dpmj/Bachelor_Thesis_TIK_Handheld_Device/ASSETS/IMAGES/DATASHEET SCREENSHOTS/ESP32_strapping_pins.png

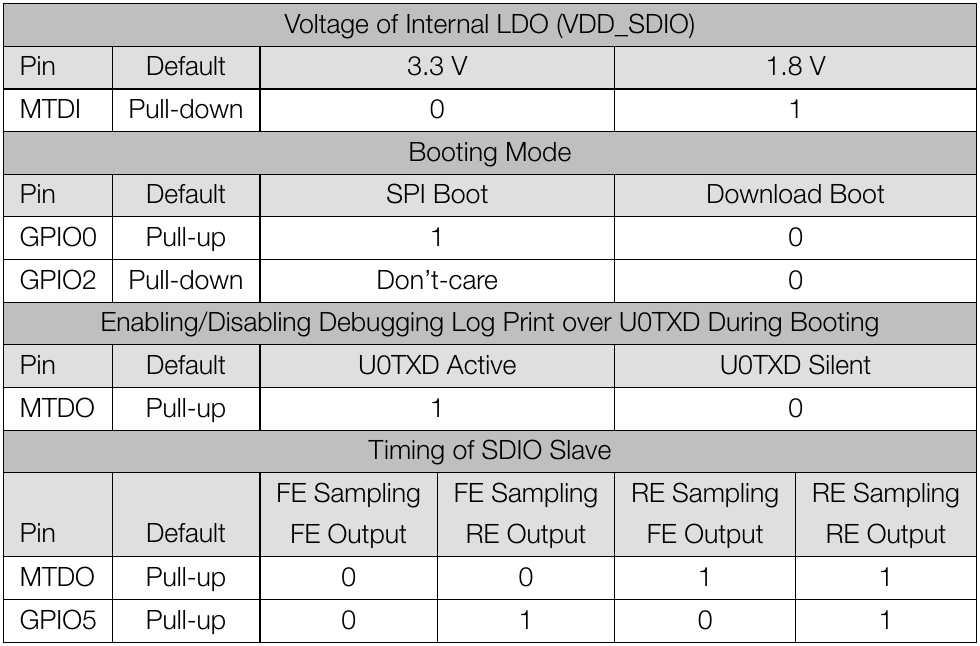
ASSETS/IMAGES/DATASHEET SCREENSHOTS/ESP32_strapping_pins.png
