dpmj/Bachelor_Thesis_TIK_Handheld_Device/ASSETS/IMAGES/PARTS/ESP32-WROOM-32D/esp32_pinout_datasheet.png

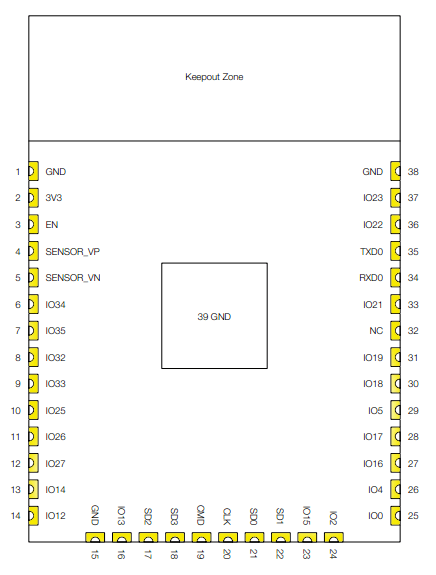
ASSETS/IMAGES/PARTS/ESP32-WROOM-32D/esp32_pinout_datasheet.png
