dpmj/Bachelor_Thesis_TIK_Handheld_Device/ASSETS/IMAGES/PARTS/ESP32-WROOM-32D/pinout_wroom_pinout_2.png

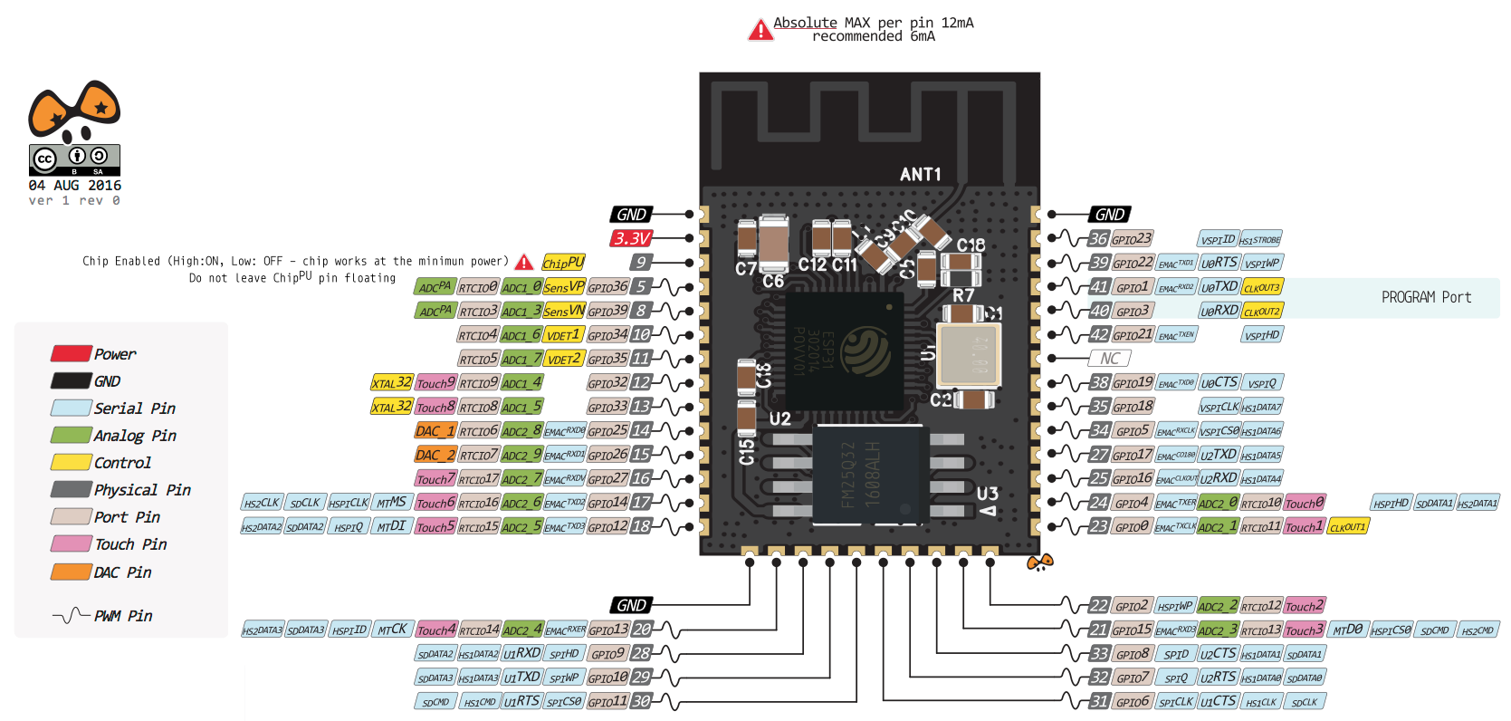
ASSETS/IMAGES/PARTS/ESP32-WROOM-32D/pinout_wroom_pinout_2.png
