dpmj/Bachelor_Thesis_TIK_Handheld_Device/ASSETS/IMAGES/PARTS/JACK/PINOUT.png

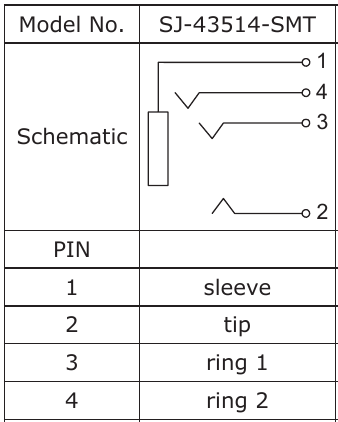
ASSETS/IMAGES/PARTS/JACK/PINOUT.png
