dpmj/Bachelor_Thesis_TIK_Handheld_Device/ASSETS/IMAGES/PARTS/JACK/PINOUT_6.png

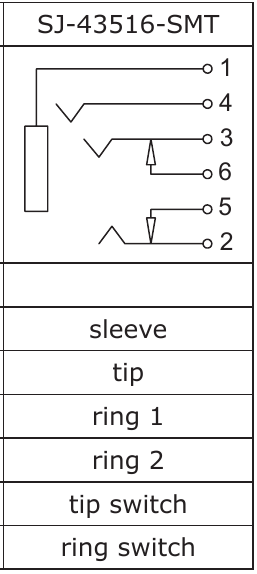
ASSETS/IMAGES/PARTS/JACK/PINOUT_6.png
