dpmj/Bachelor_Thesis_TIK_Handheld_Device/ASSETS/IMAGES/PCB RENDERS/bottom.png

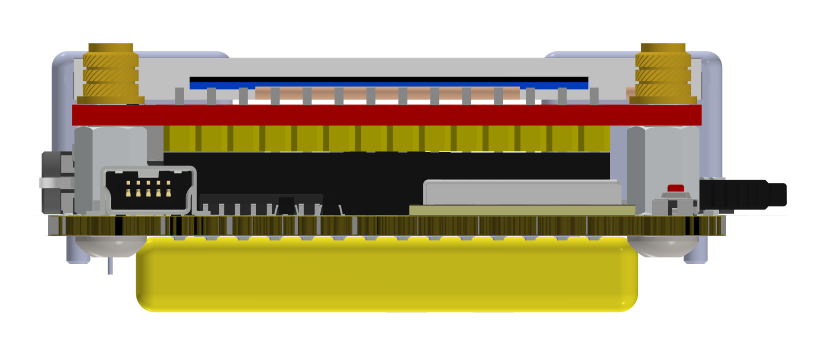
ASSETS/IMAGES/PCB RENDERS/bottom.png
