dpmj/Bachelor_Thesis_TIK_Handheld_Device/ASSETS/IMAGES/PCB RENDERS/FRONT.png

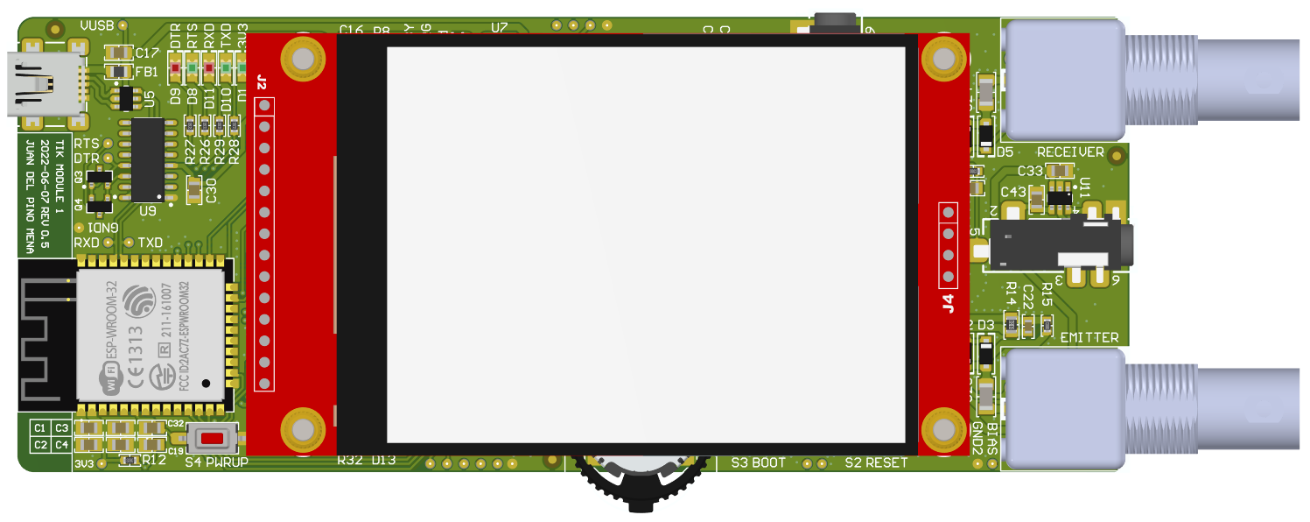
ASSETS/IMAGES/PCB RENDERS/FRONT.png
