dpmj/Bachelor_Thesis_TIK_Handheld_Device/ASSETS/IMAGES/PCB RENDERS/FRONT_NOSCREEN.png

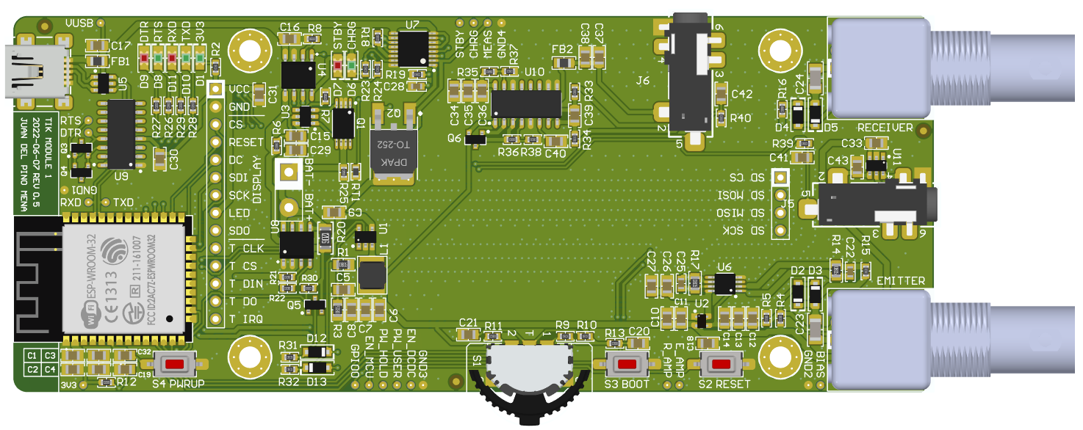
ASSETS/IMAGES/PCB RENDERS/FRONT_NOSCREEN.png
