dpmj/Bachelor_Thesis_TIK_Handheld_Device/ASSETS/IMAGES/PCB RENDERS/introduction2.png

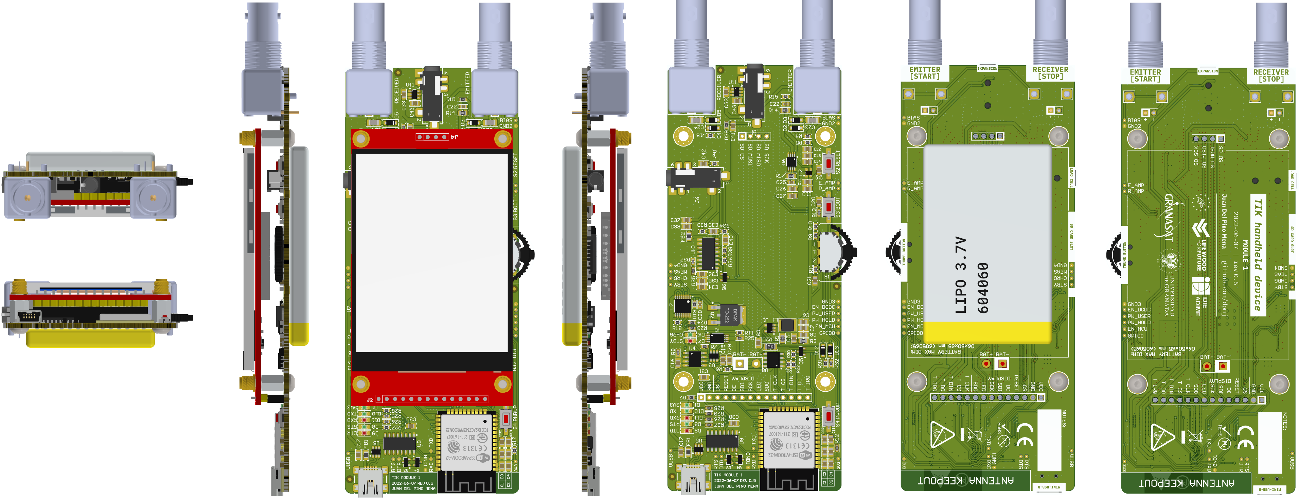
ASSETS/IMAGES/PCB RENDERS/introduction2.png
