dpmj/Bachelor_Thesis_TIK_Handheld_Device/ASSETS/IMAGES/PCB RENDERS/introduction.png

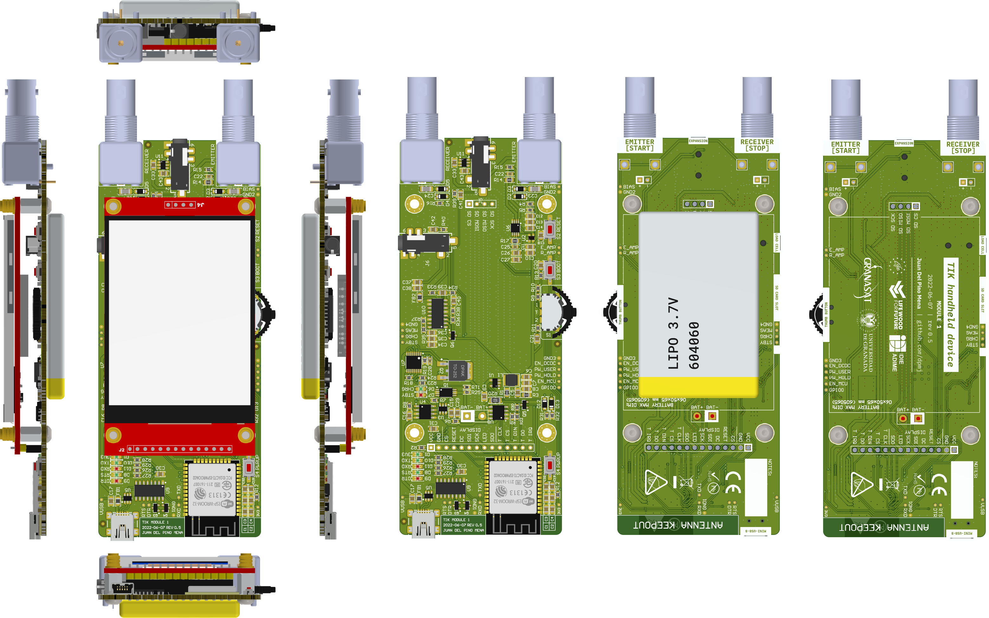
ASSETS/IMAGES/PCB RENDERS/introduction.png
