dpmj/Bachelor_Thesis_TIK_Handheld_Device/ASSETS/IMAGES/PCB RENDERS/PERSPECTIVE.png

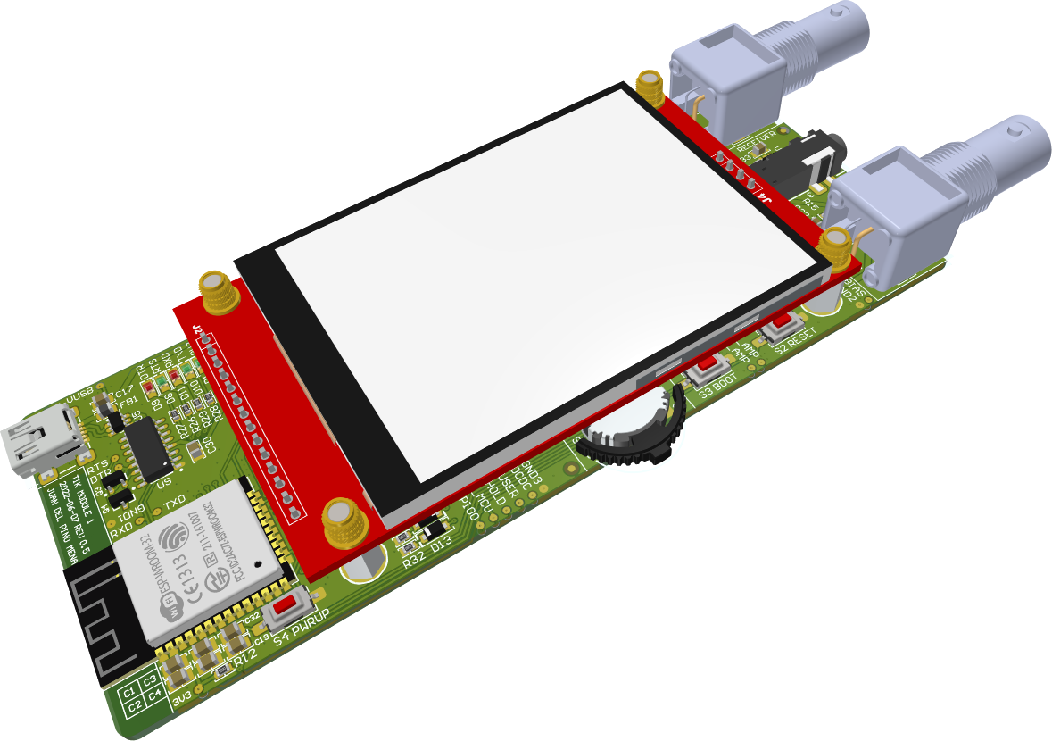
ASSETS/IMAGES/PCB RENDERS/PERSPECTIVE.png
