dpmj/Bachelor_Thesis_TIK_Handheld_Device/ASSETS/IMAGES/PCB RENDERS/SIDE_05.png

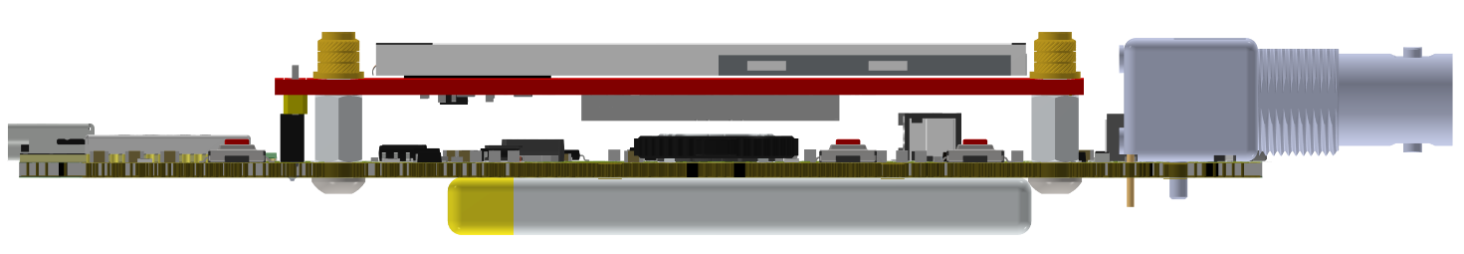
ASSETS/IMAGES/PCB RENDERS/SIDE_05.png
