dpmj/Bachelor_Thesis_TIK_Handheld_Device/ASSETS/IMAGES/PCB RENDERS/SIDE_05_2.png

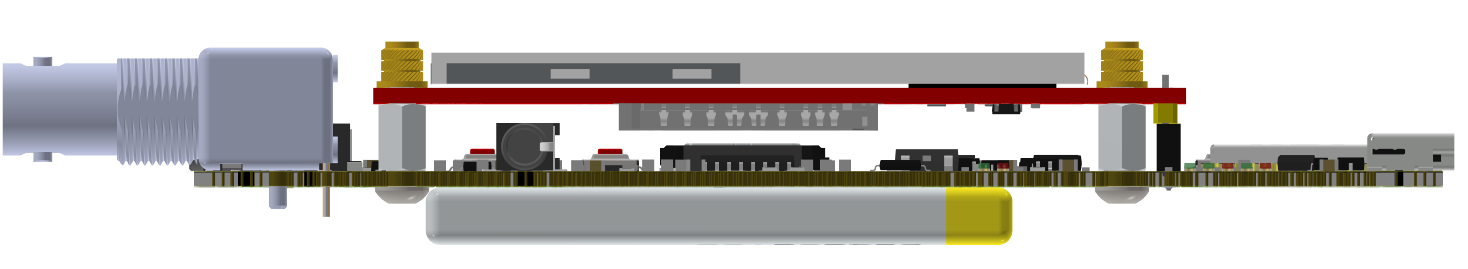
ASSETS/IMAGES/PCB RENDERS/SIDE_05_2.png
