dpmj/Bachelor_Thesis_TIK_Handheld_Device/ASSETS/IMAGES/SATURN PCB DESIGN/80MHZ_WL.png

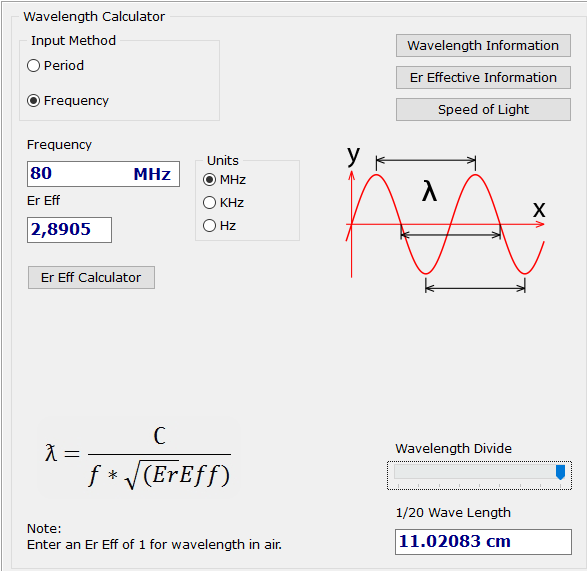
ASSETS/IMAGES/SATURN PCB DESIGN/80MHZ_WL.png
