dpmj/Bachelor_Thesis_TIK_Handheld_Device/ASSETS/IMAGES/SATURN PCB DESIGN/analog_crosstalk.png

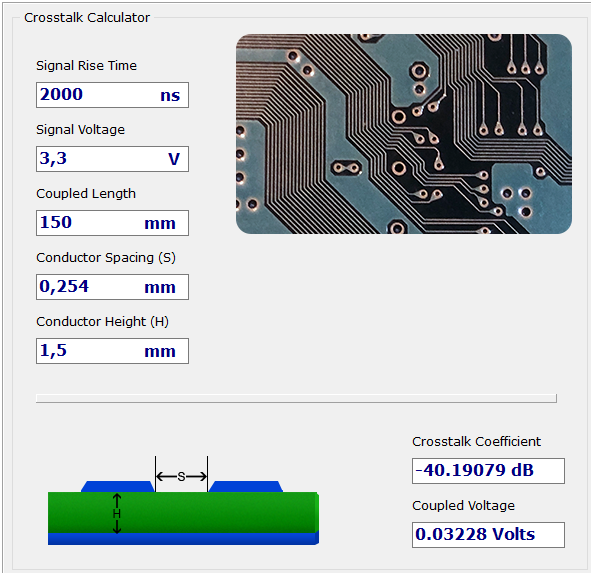
ASSETS/IMAGES/SATURN PCB DESIGN/analog_crosstalk.png
