dpmj/Bachelor_Thesis_TIK_Handheld_Device/ASSETS/IMAGES/SATURN PCB DESIGN/analog_er_Eff.png

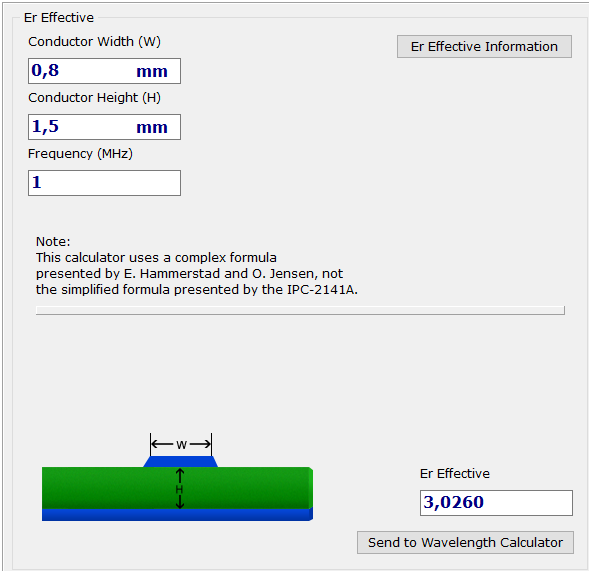
ASSETS/IMAGES/SATURN PCB DESIGN/analog_er_Eff.png
