dpmj/Bachelor_Thesis_TIK_Handheld_Device/ASSETS/IMAGES/SATURN PCB DESIGN/TRACE_0_8mm_COPLANAR_SIGNAL.png

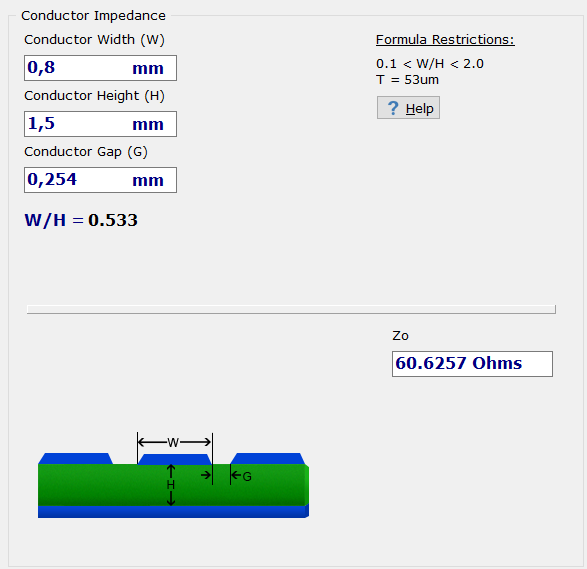
ASSETS/IMAGES/SATURN PCB DESIGN/TRACE_0_8mm_COPLANAR_SIGNAL.png
