dpmj/Bachelor_Thesis_TIK_Handheld_Device/ASSETS/IMAGES/SATURN PCB DESIGN/TRACE_05mm.png

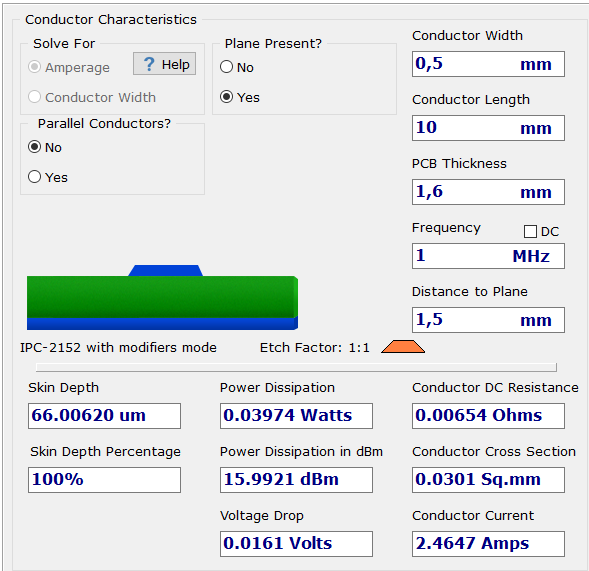
ASSETS/IMAGES/SATURN PCB DESIGN/TRACE_05mm.png
