dpmj/Bachelor_Thesis_TIK_Handheld_Device/ASSETS/IMAGES/SATURN PCB DESIGN/TRACE_08mm_2.png

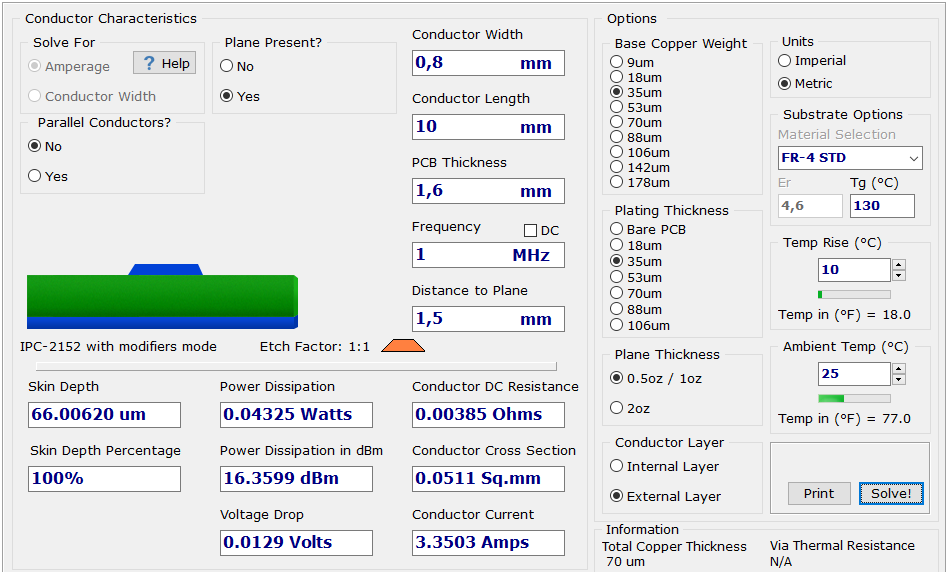
ASSETS/IMAGES/SATURN PCB DESIGN/TRACE_08mm_2.png
