dpmj/Bachelor_Thesis_TIK_Handheld_Device/ASSETS/IMAGES/SATURN PCB DESIGN/VIA_30_60.png

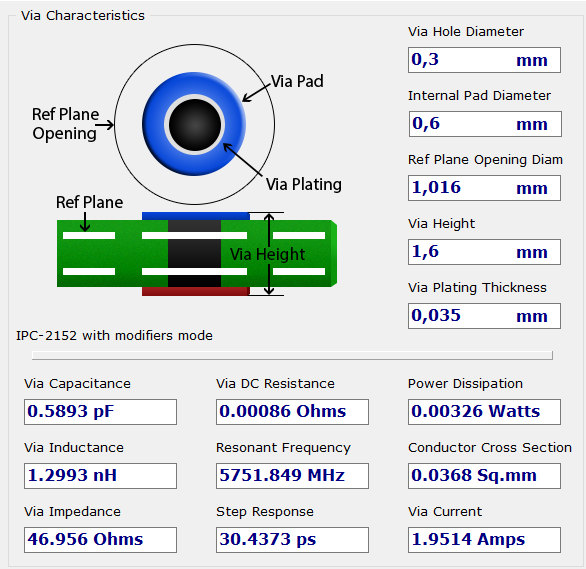
ASSETS/IMAGES/SATURN PCB DESIGN/VIA_30_60.png
