dpmj/Bachelor_Thesis_TIK_Handheld_Device/ASSETS/IMAGES/SIGNALS/psd.png

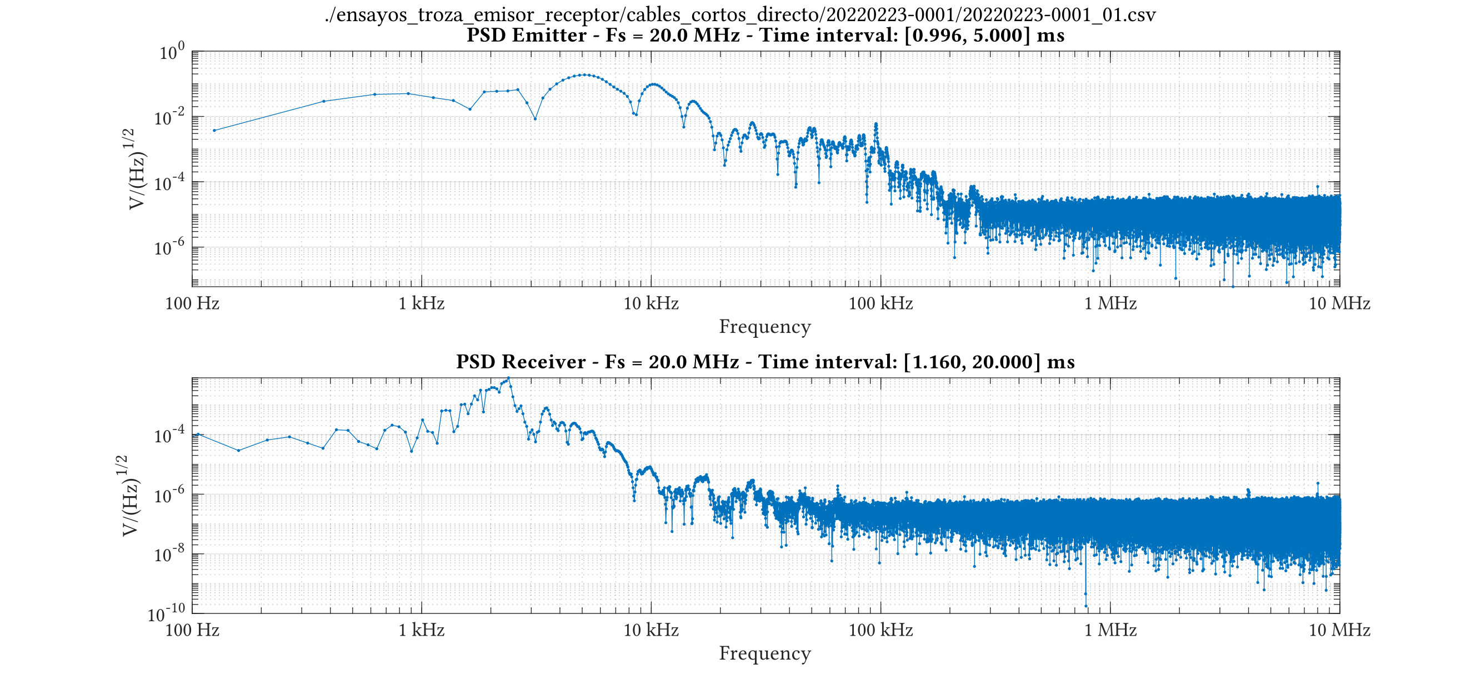
ASSETS/IMAGES/SIGNALS/psd.png
