dpmj/Bachelor_Thesis_TIK_Handheld_Device/ASSETS/power budget/power budget2.pdf.2022_08_09_00_11_06.0.png

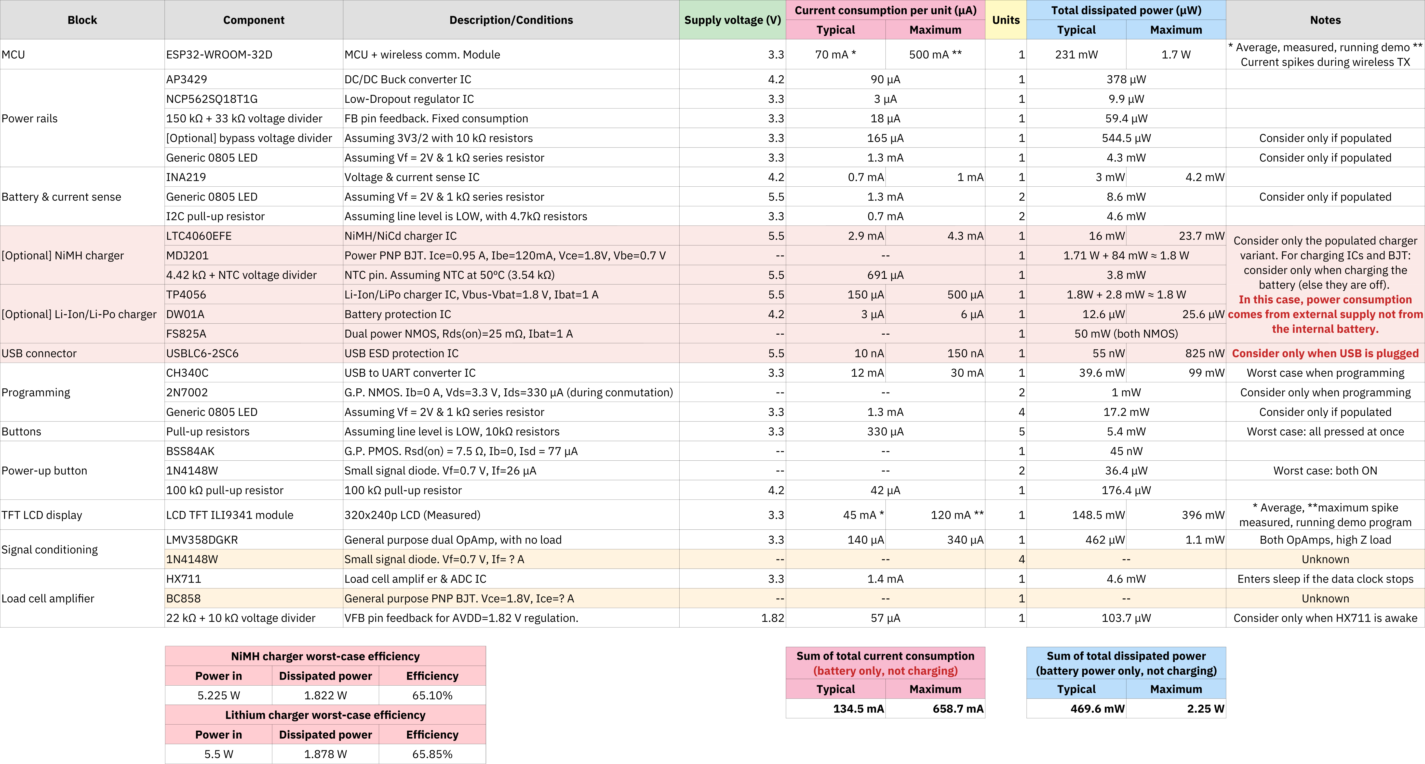
ASSETS/power budget/power budget2.pdf.2022_08_09_00_11_06.0.png
