dpmj/Bachelor_Thesis_TIK_Handheld_Device/ASSETS/power budget/power_budget.png

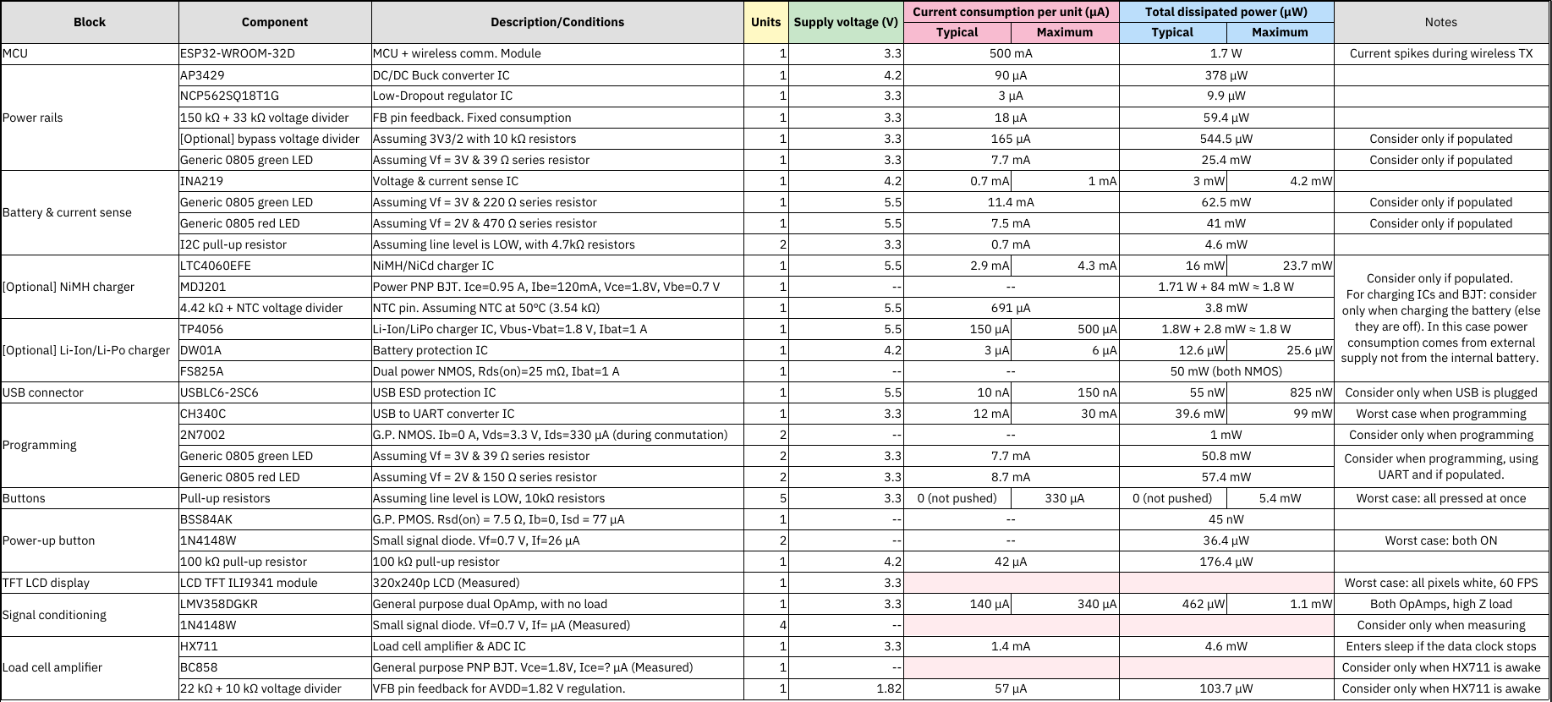
ASSETS/power budget/power_budget.png
