dpmj/Bachelor_Thesis_TIK_Handheld_Device/ASSETS/SPICE/ALTIUM/CLIPPED_SIGNALS.png

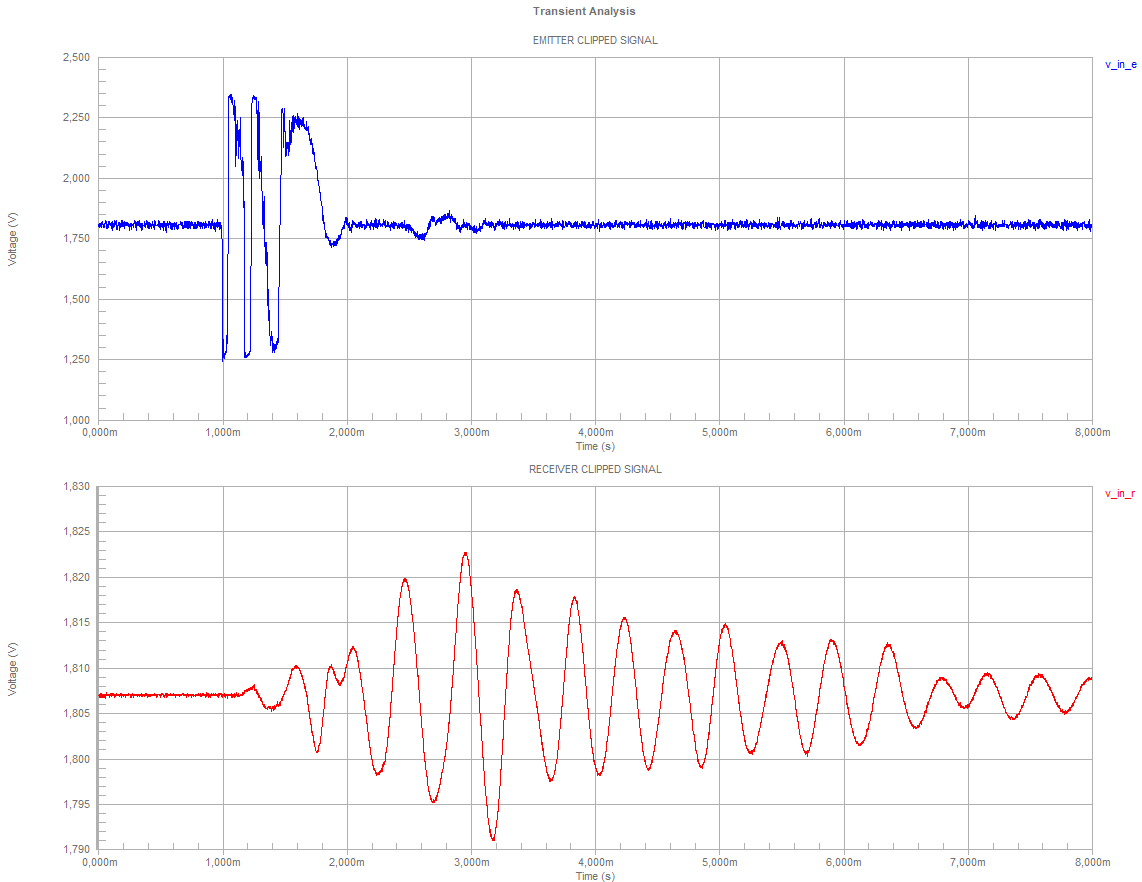
ASSETS/SPICE/ALTIUM/CLIPPED_SIGNALS.png
