dpmj/Bachelor_Thesis_TIK_Handheld_Device/ASSETS/SPICE/ALTIUM/emitter_all_signals.png

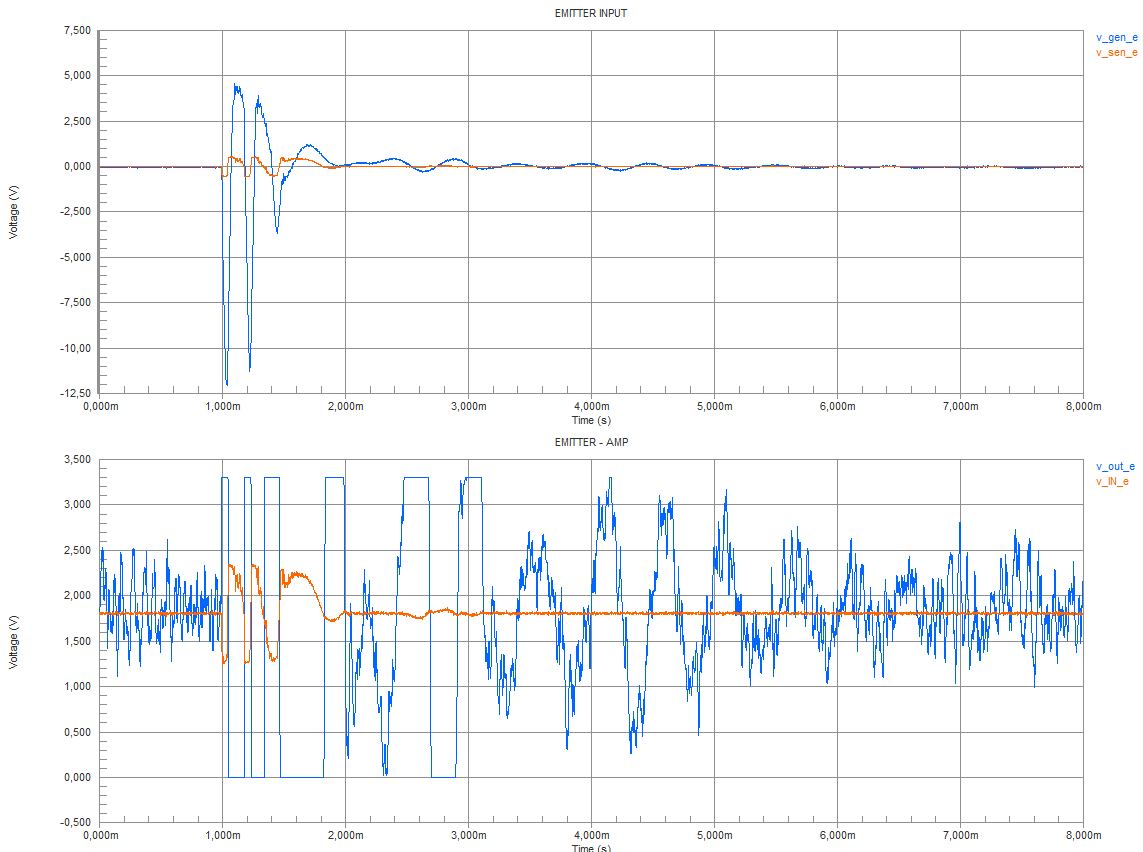
ASSETS/SPICE/ALTIUM/emitter_all_signals.png
