dpmj/Bachelor_Thesis_TIK_Handheld_Device/ASSETS/SPICE/ALTIUM/emitter_all_signals_fft.png

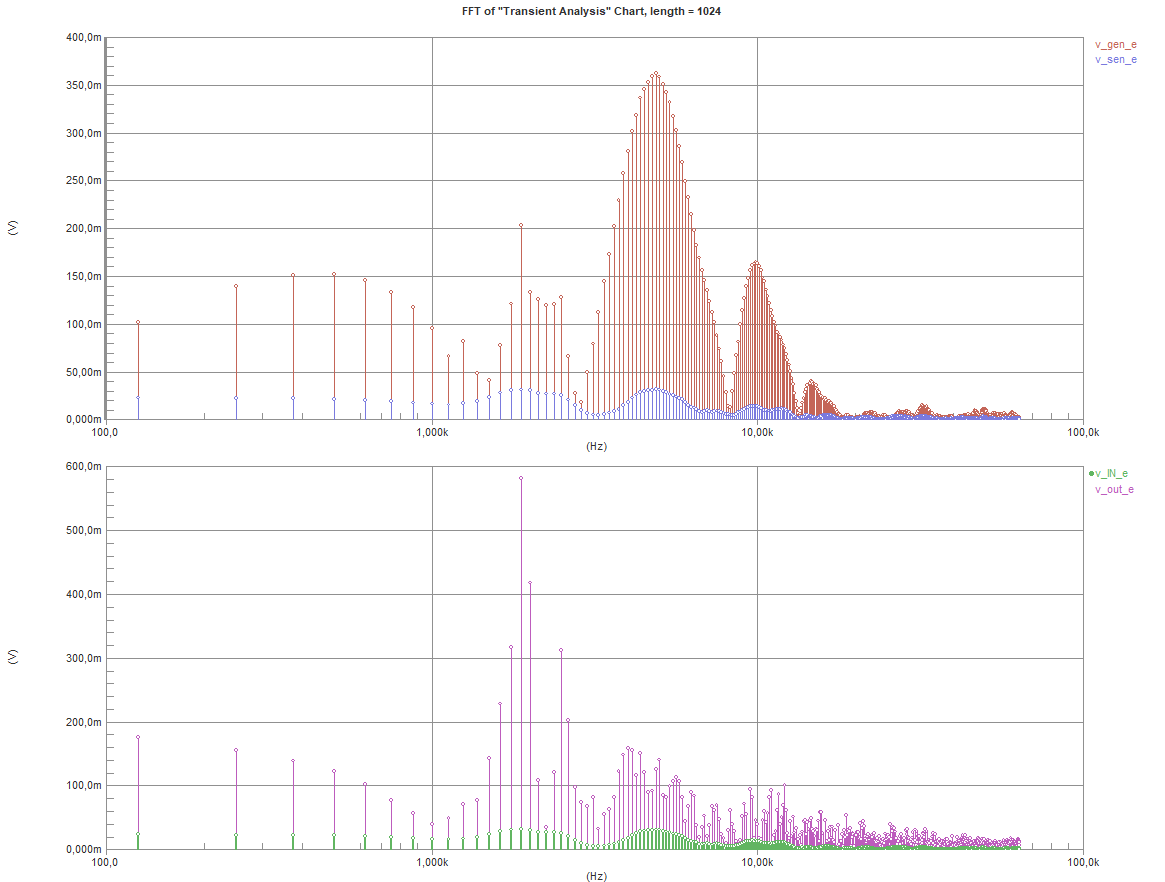
ASSETS/SPICE/ALTIUM/emitter_all_signals_fft.png
