dpmj/Bachelor_Thesis_TIK_Handheld_Device/ASSETS/SPICE/ALTIUM/receiver_all_signals.png

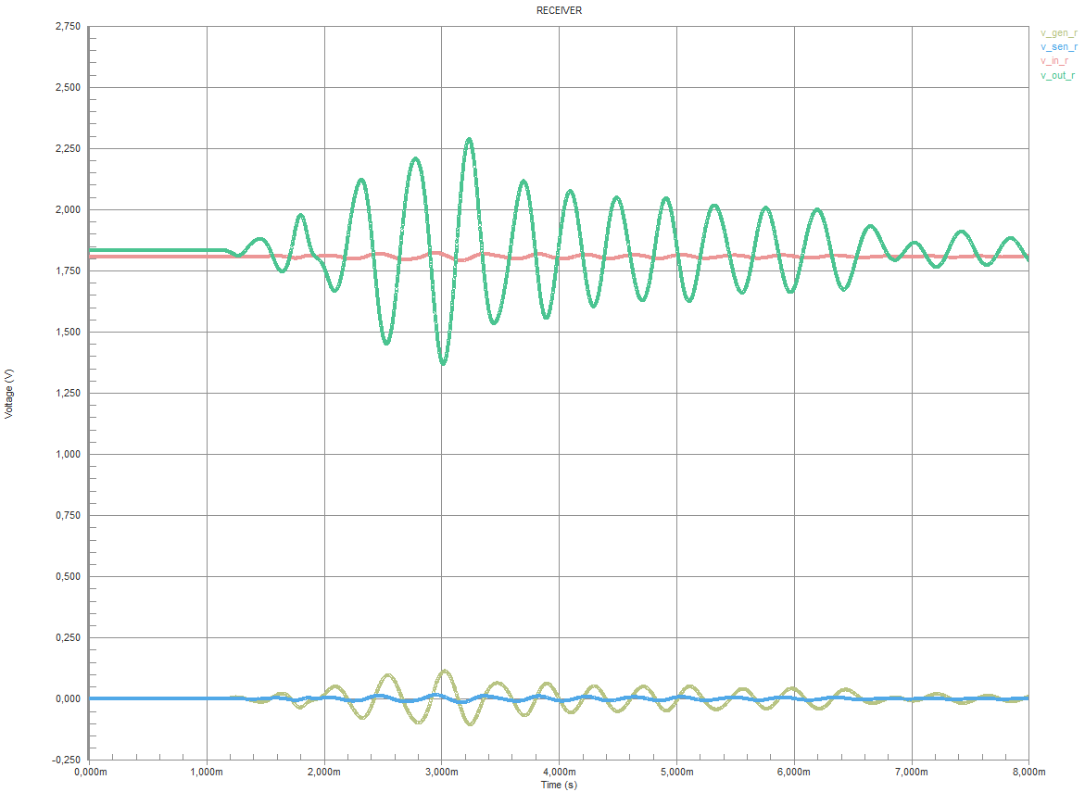
ASSETS/SPICE/ALTIUM/receiver_all_signals.png
