dpmj/Bachelor_Thesis_TIK_Handheld_Device/ASSETS/SPICE/ALTIUM/rise_time.png

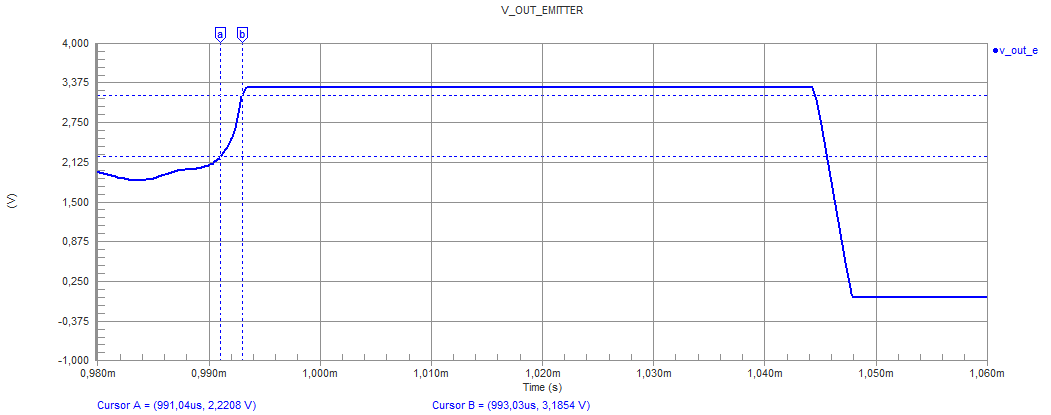
ASSETS/SPICE/ALTIUM/rise_time.png
