dpmj/Bachelor_Thesis_TIK_Handheld_Device/ASSETS/SPICE/ALTIUM/sim_circuit.png

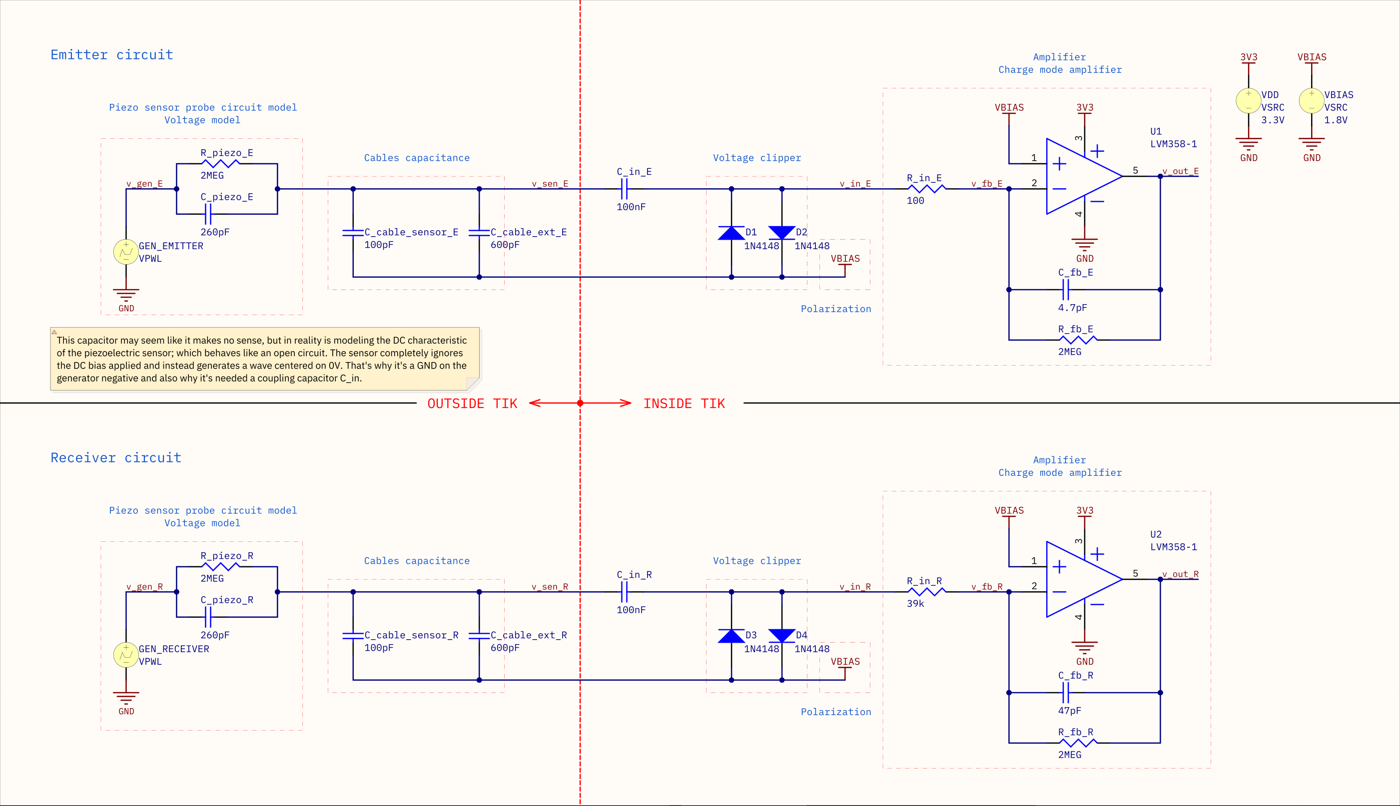
ASSETS/SPICE/ALTIUM/sim_circuit.png
