dpmj/Bachelor_Thesis_TIK_Handheld_Device/ASSETS/SPICE/LTSPICE/CONDITIONING/AC_1Hz_10Meg_CF22pF_RF10M_Rin100.png

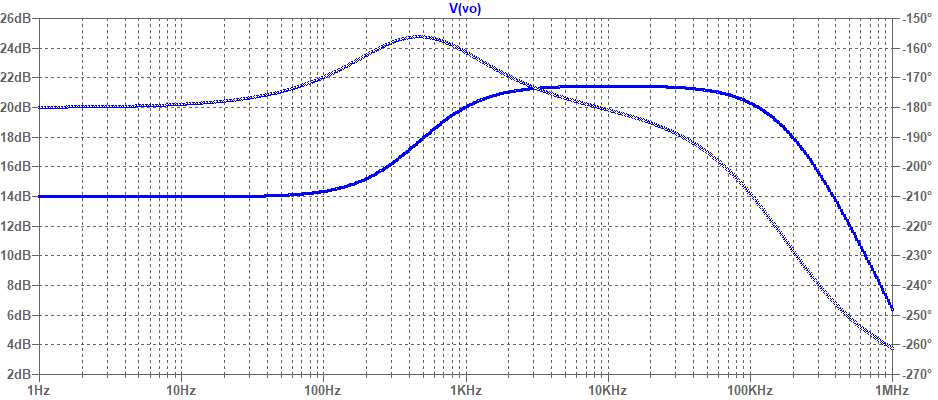
ASSETS/SPICE/LTSPICE/CONDITIONING/AC_1Hz_10Meg_CF22pF_RF10M_Rin100.png
