dpmj/Bachelor_Thesis_TIK_Handheld_Device/ASSETS/SPICE/LTSPICE/CONDITIONING/AC_1Hz_10Meg_CF47pF_RF10M_Rin10k.png

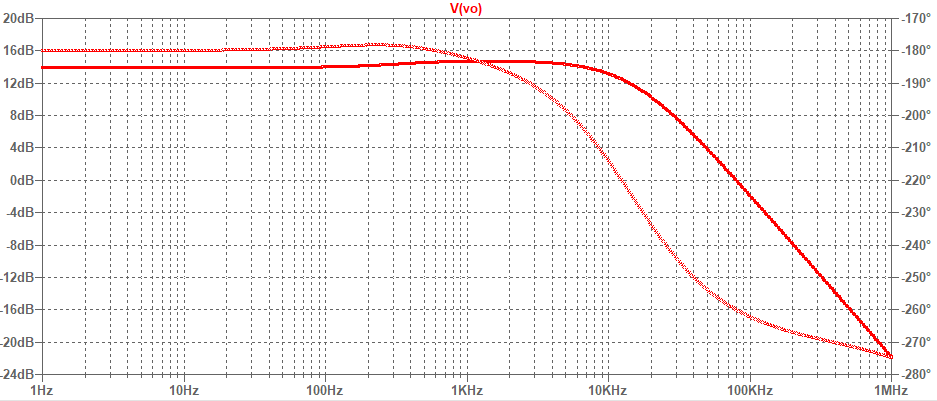
ASSETS/SPICE/LTSPICE/CONDITIONING/AC_1Hz_10Meg_CF47pF_RF10M_Rin10k.png
