dpmj/Bachelor_Thesis_TIK_Handheld_Device/ASSETS/SPICE/LTSPICE/CONDITIONING/emitter_receiver_time_behaviour.png

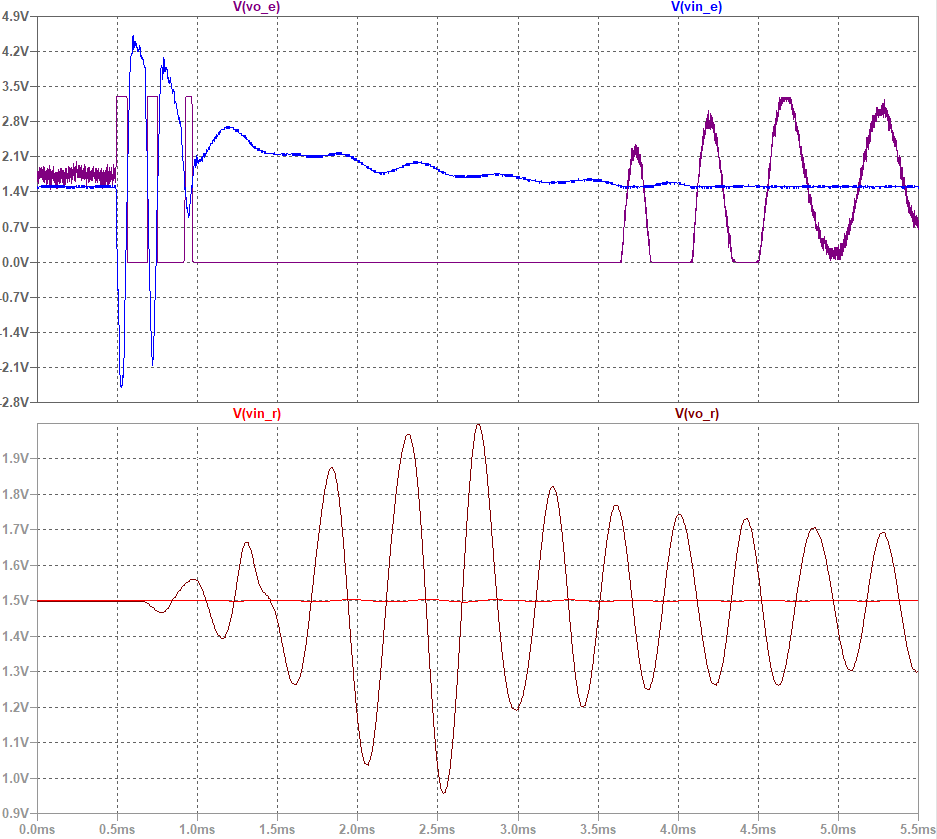
ASSETS/SPICE/LTSPICE/CONDITIONING/emitter_receiver_time_behaviour.png
