dpmj/Bachelor_Thesis_TIK_Handheld_Device/ASSETS/TIK_CASE/BOARD_NOSCREWS/bottom_decal.png

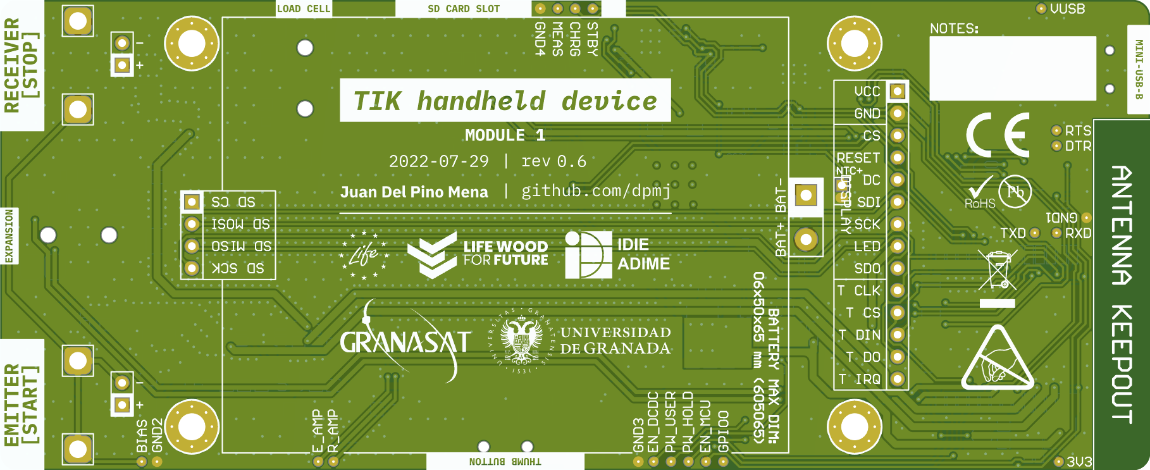
ASSETS/TIK_CASE/BOARD_NOSCREWS/bottom_decal.png
