dpmj/Bachelor_Thesis_TIK_Handheld_Device/ASSETS/TIK_CASE/BOARD_NOSCREWS/top_decal.png

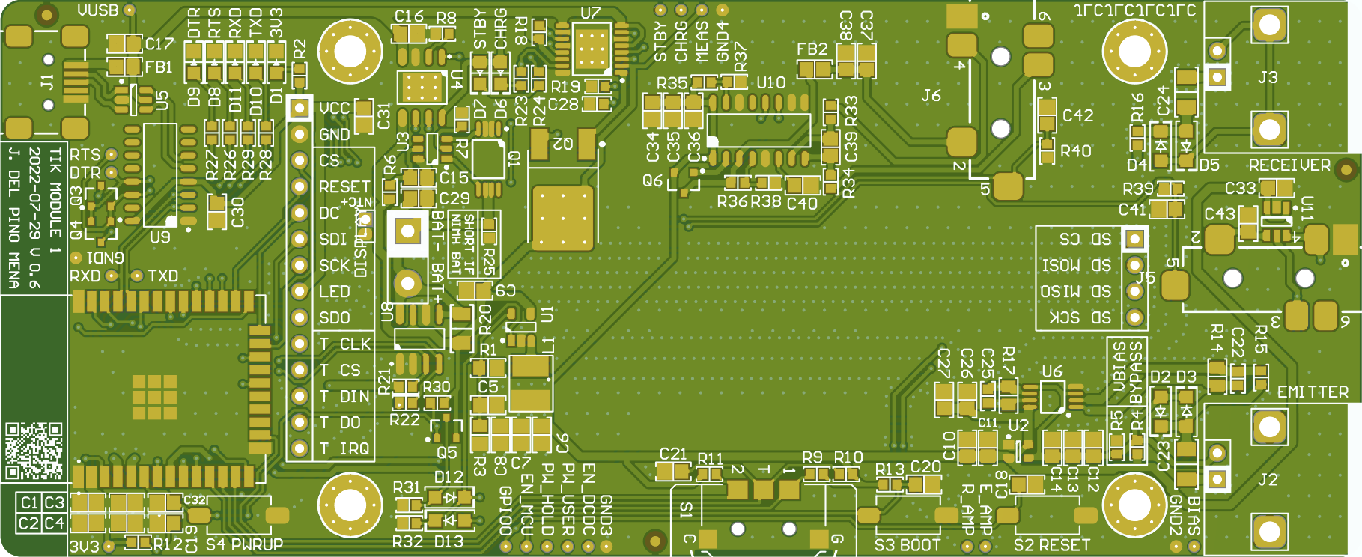
ASSETS/TIK_CASE/BOARD_NOSCREWS/top_decal.png
