dpmj/Bachelor_Thesis_TIK_Handheld_Device/ASSETS/TIK_CASE/DRAWINGS/Page 1.png

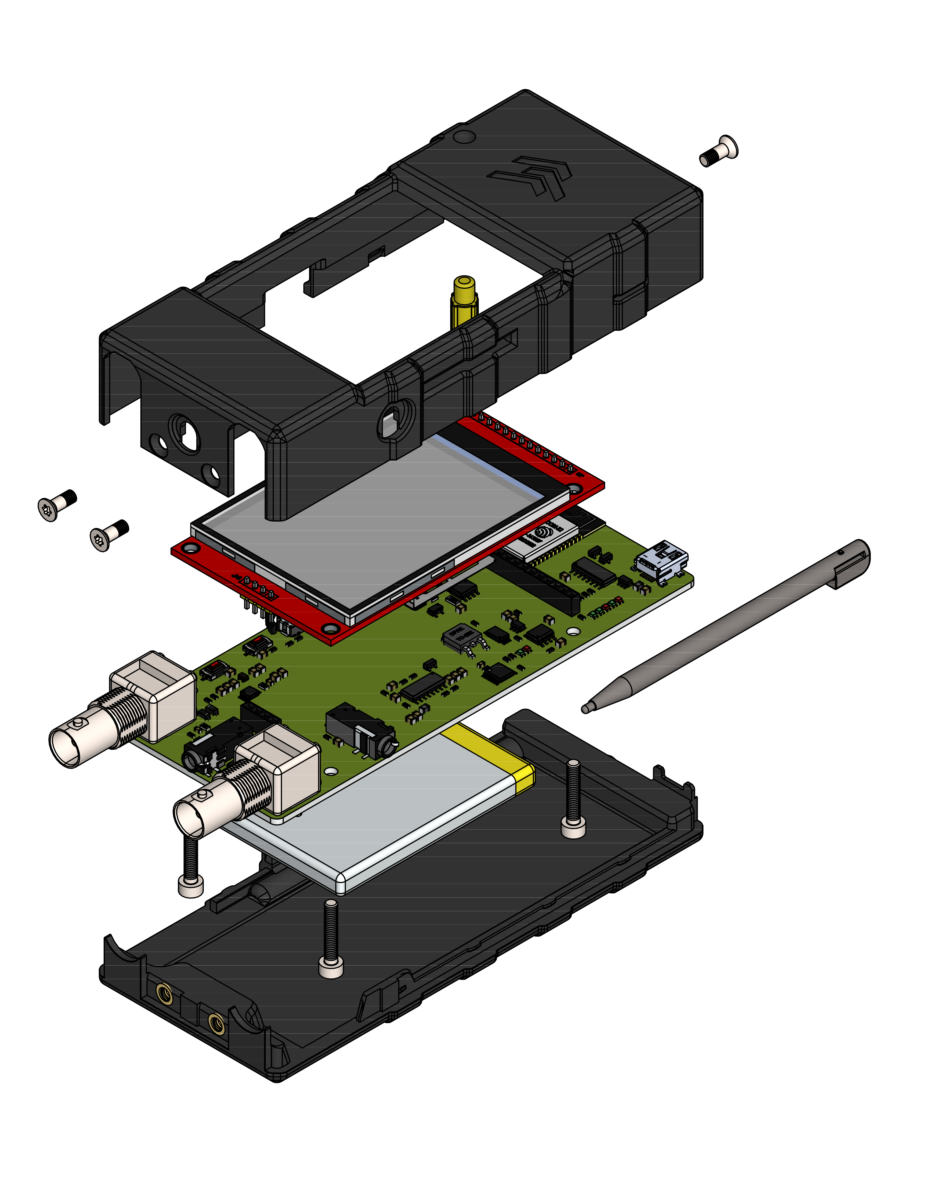
ASSETS/TIK_CASE/DRAWINGS/Page 1.png
