dpmj/Bachelor_Thesis_TIK_Handheld_Device/ASSETS/TIK_CASE/EXPORT/VIDEO/video_cover.png

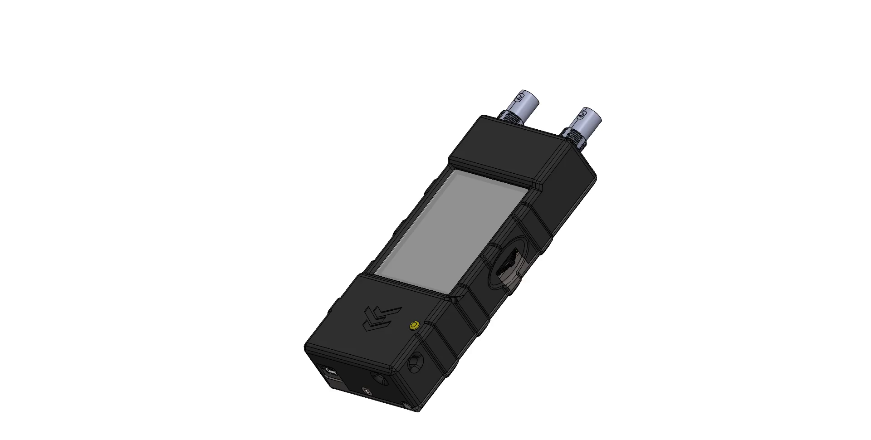
ASSETS/TIK_CASE/EXPORT/VIDEO/video_cover.png
