dpmj/Bachelor_Thesis_TIK_Handheld_Device/ASSETS/TIK_CASE/FUTURE/back.png

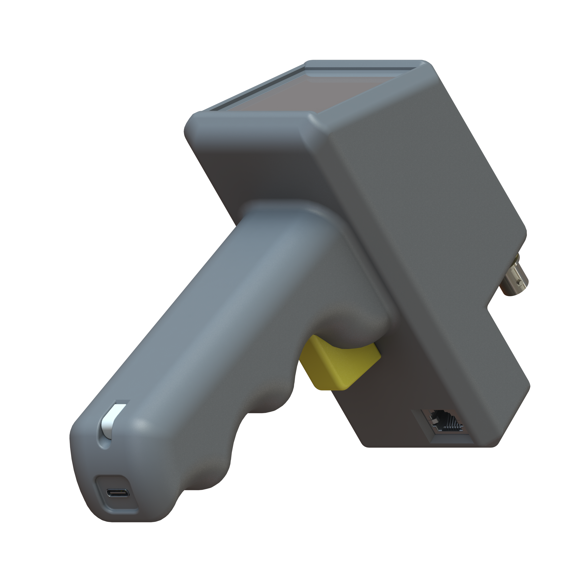
ASSETS/TIK_CASE/FUTURE/back.png
