dpmj/Bachelor_Thesis_TIK_Handheld_Device/ASSETS/TIK_CASE/FUTURE/front.png

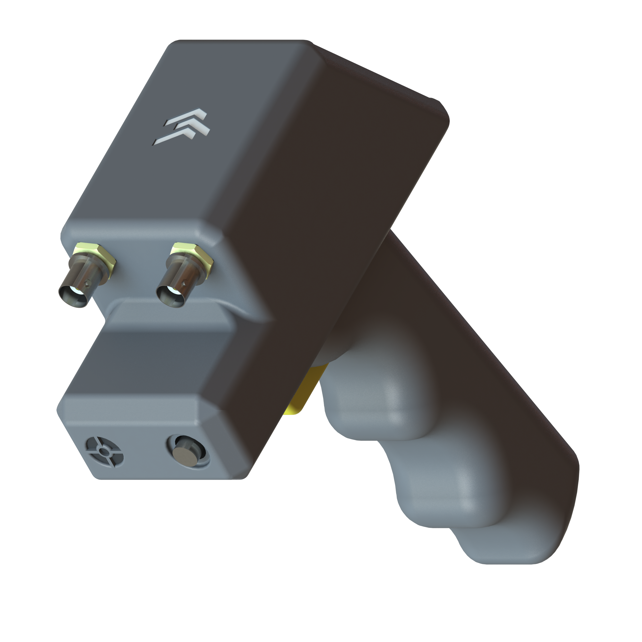
ASSETS/TIK_CASE/FUTURE/front.png
