dpmj/Bachelor_Thesis_TIK_Handheld_Device/ASSETS/TIK_CASE/FUTURE/levantada.png

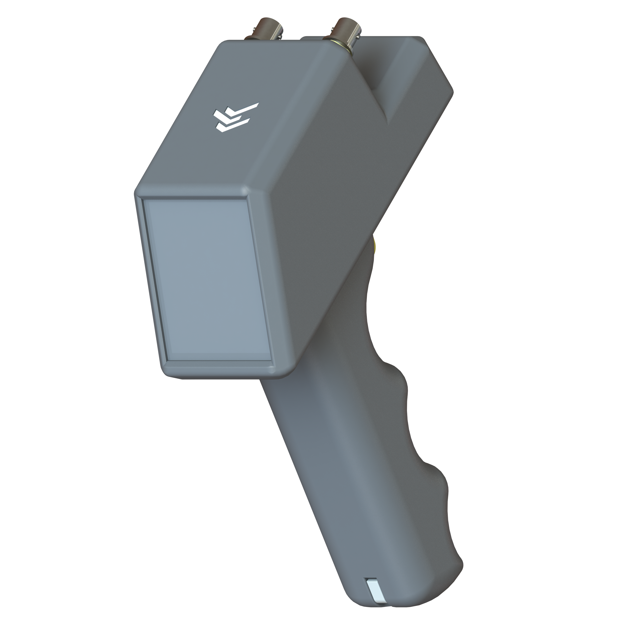
ASSETS/TIK_CASE/FUTURE/levantada.png
