dpmj/Bachelor_Thesis_TIK_Handheld_Device/ASSETS/TIK_CASE/FUTURE/tumbada2.png

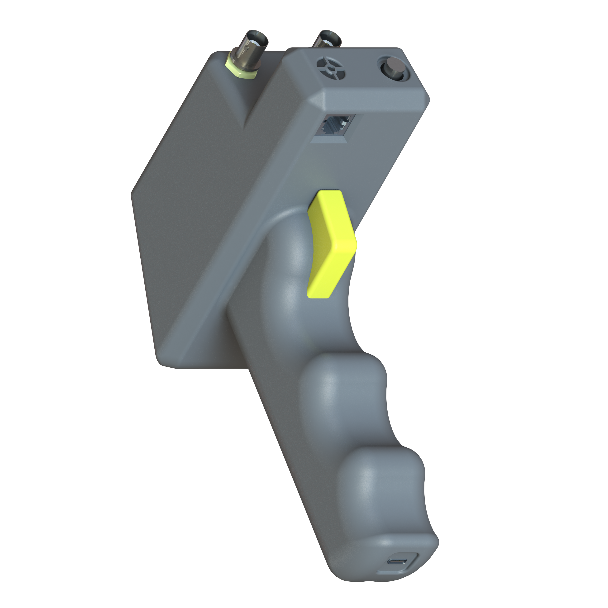
ASSETS/TIK_CASE/FUTURE/tumbada2.png
