dpmj/Bachelor_Thesis_TIK_Handheld_Device/ASSETS/TIK_CASE/FUTURE/tumbada.png

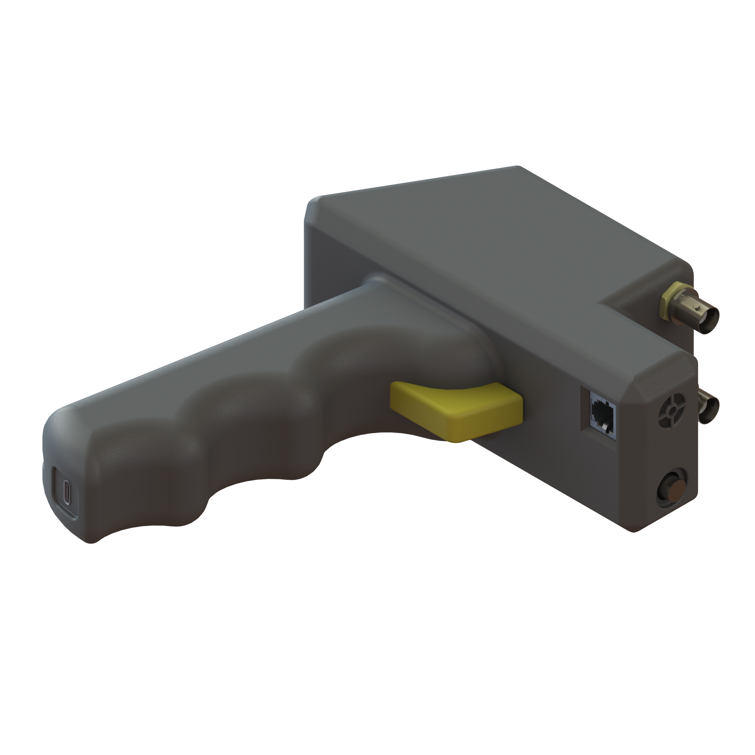
ASSETS/TIK_CASE/FUTURE/tumbada.png
