dpmj/Bachelor_Thesis_TIK_Handheld_Device/ASSETS/TIK_CASE/PROTO/BNC Connector/BNC Connector 02.jpg

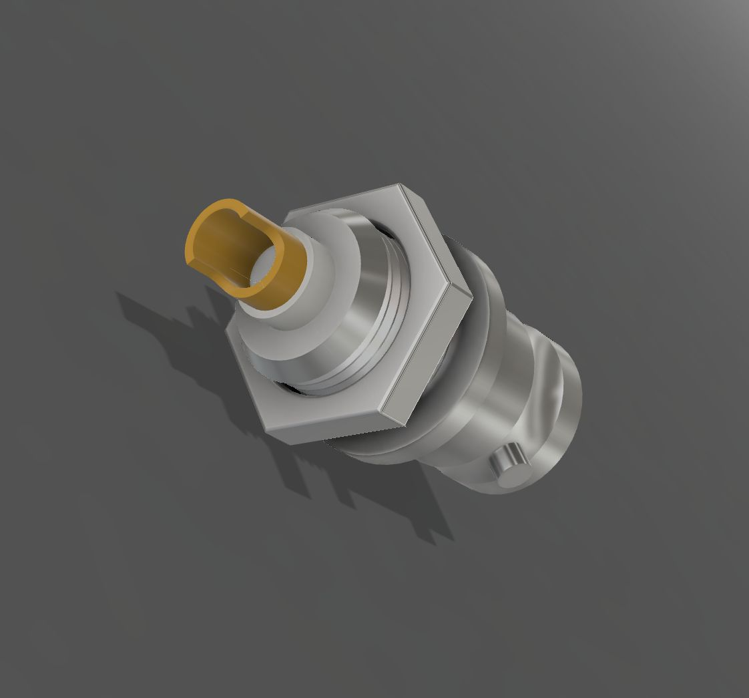
ASSETS/TIK_CASE/PROTO/BNC Connector/BNC Connector 02.jpg
