dpmj/Bachelor_Thesis_TIK_Handheld_Device/ASSETS/TIK_CASE/PROTO/bnc-connector--1.snapshot.1/bnc.jpg

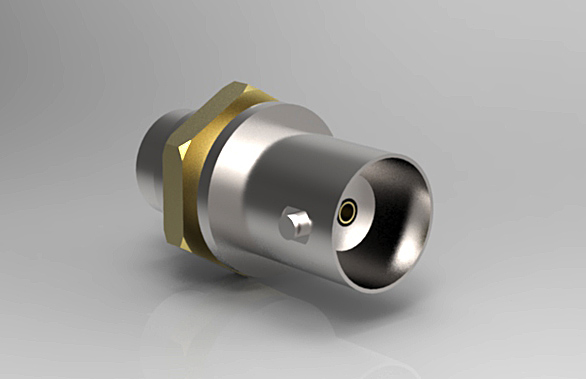
ASSETS/TIK_CASE/PROTO/bnc-connector--1.snapshot.1/bnc.jpg
