dpmj/Bachelor_Thesis_TIK_Handheld_Device/ASSETS/TIK_CASE/PROTO/proto_y_final.JPG

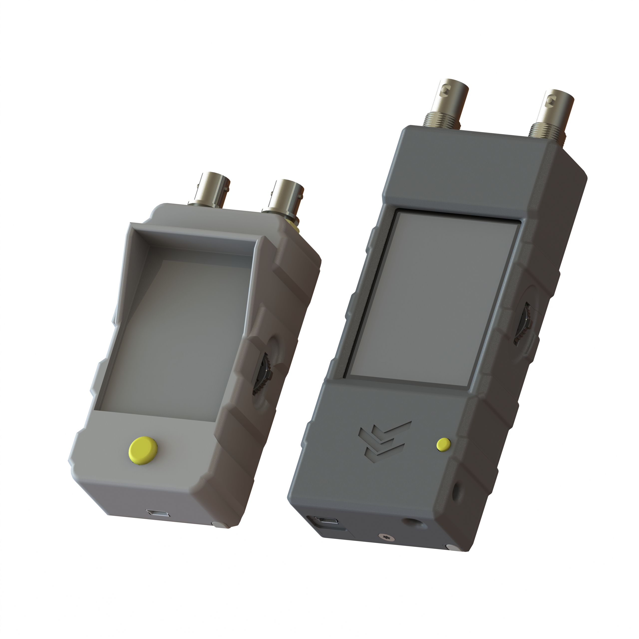
ASSETS/TIK_CASE/PROTO/proto_y_final.JPG
