dpmj/Bachelor_Thesis_TIK_Handheld_Device/ASSETS/TIK_CASE/PROTO/render.JPG

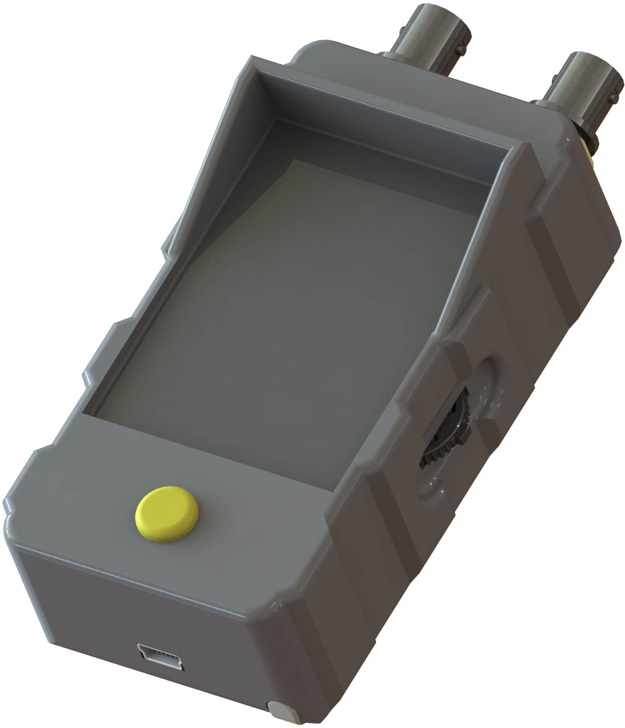
ASSETS/TIK_CASE/PROTO/render.JPG
