dpmj/Bachelor_Thesis_TIK_Handheld_Device/ASSETS/IMAGES/PARTS/1N4148W/FOOTPRINT.png

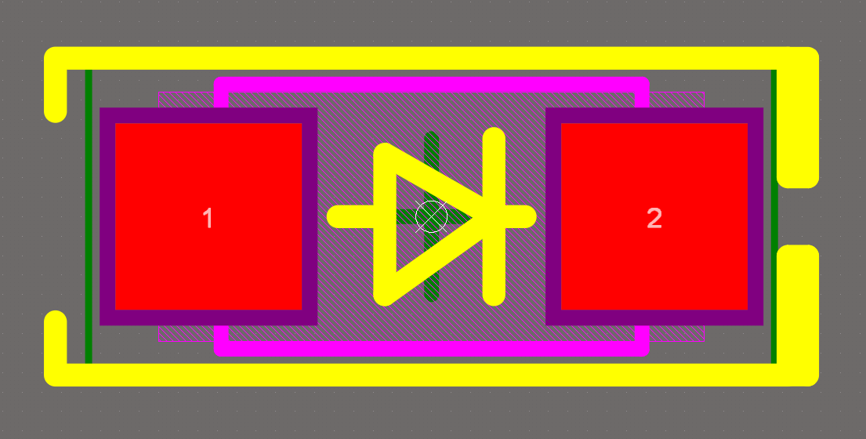
ASSETS/IMAGES/PARTS/1N4148W/FOOTPRINT.png
