dpmj/Bachelor_Thesis_TIK_Handheld_Device/ASSETS/IMAGES/PARTS/2N7002/FOOTPRINT.png

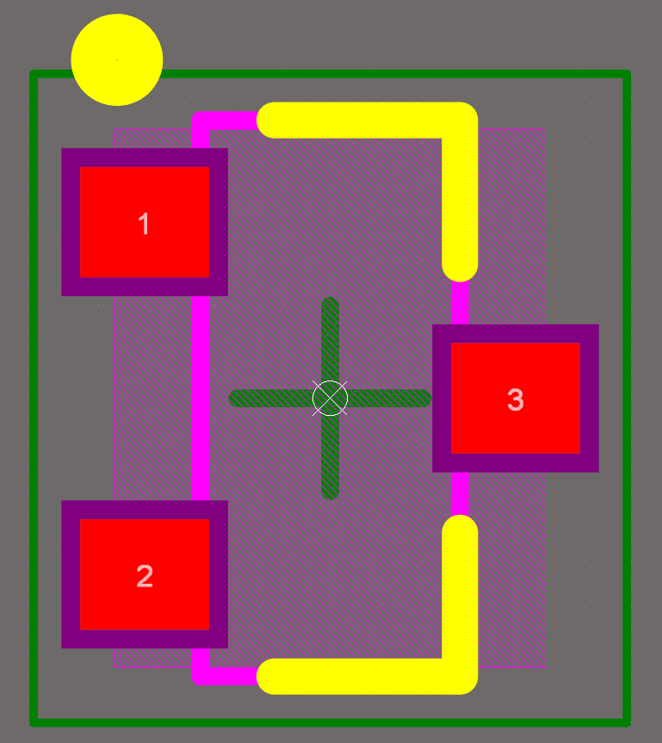
ASSETS/IMAGES/PARTS/2N7002/FOOTPRINT.png
