dpmj/Bachelor_Thesis_TIK_Handheld_Device/ASSETS/IMAGES/PARTS/2N7002/SOT-23-3 PKG.png

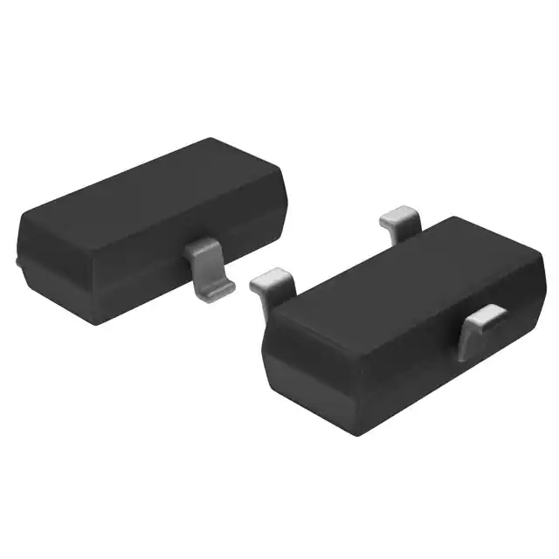
ASSETS/IMAGES/PARTS/2N7002/SOT-23-3 PKG.png
