dpmj/Bachelor_Thesis_TIK_Handheld_Device/ASSETS/IMAGES/PARTS/AP3429/FOOTPRINT.png

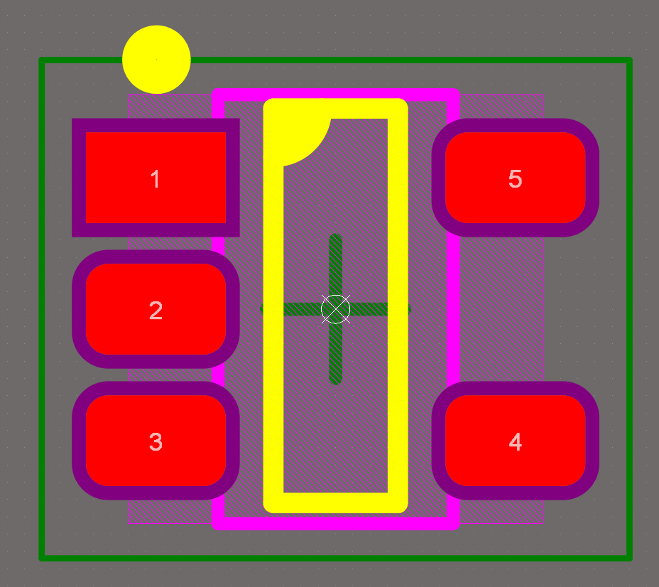
ASSETS/IMAGES/PARTS/AP3429/FOOTPRINT.png
