dpmj/Bachelor_Thesis_TIK_Handheld_Device/ASSETS/IMAGES/PARTS/AP3429/TSOT-25.jpg

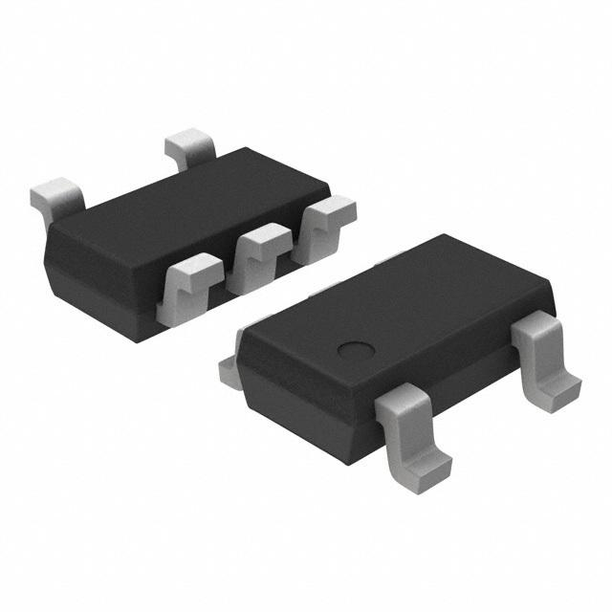
ASSETS/IMAGES/PARTS/AP3429/TSOT-25.jpg
