dpmj/Bachelor_Thesis_TIK_Handheld_Device/ASSETS/IMAGES/PARTS/BATTERY/MIKROE-4473_SPL.webp

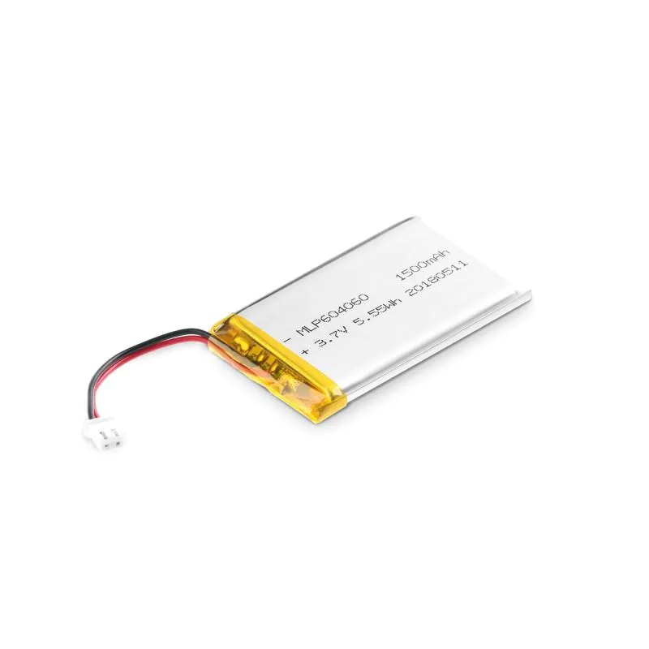
ASSETS/IMAGES/PARTS/BATTERY/MIKROE-4473_SPL.webp
