dpmj/Bachelor_Thesis_TIK_Handheld_Device/ASSETS/IMAGES/PARTS/BNC/031-71043.png

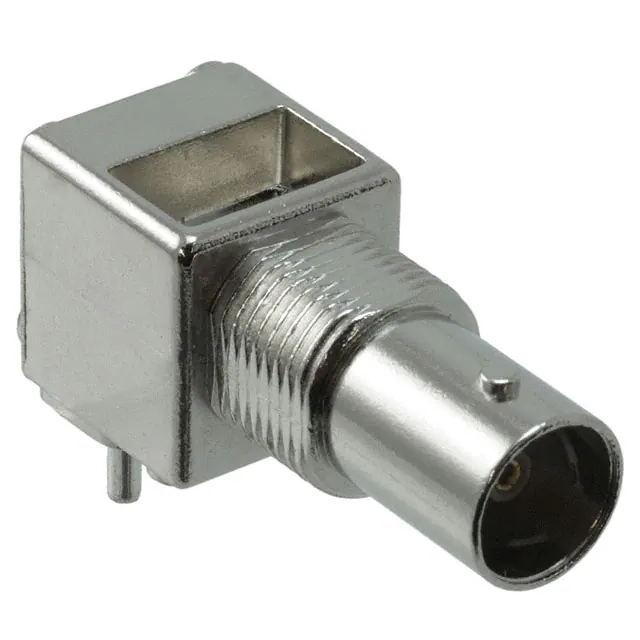
ASSETS/IMAGES/PARTS/BNC/031-71043.png
