dpmj/Bachelor_Thesis_TIK_Handheld_Device/ASSETS/IMAGES/PARTS/BNC/bnc side.jpg

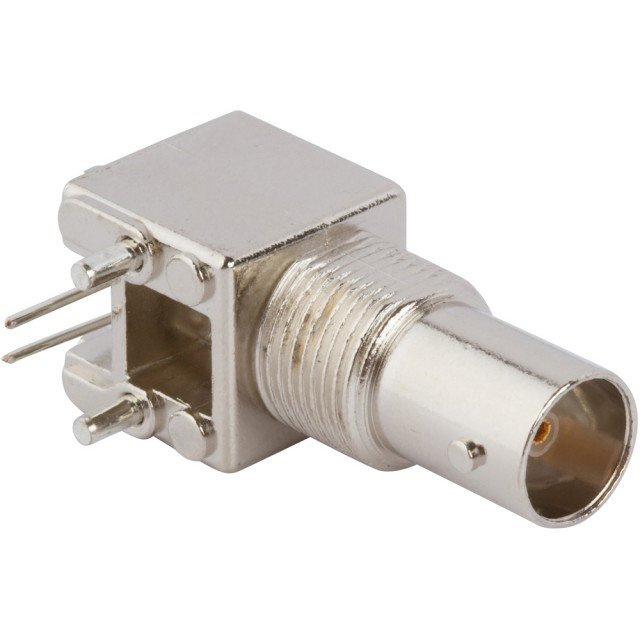
ASSETS/IMAGES/PARTS/BNC/bnc side.jpg
