dpmj/Bachelor_Thesis_TIK_Handheld_Device/ASSETS/IMAGES/PARTS/BNC/FOOTPRINT.png

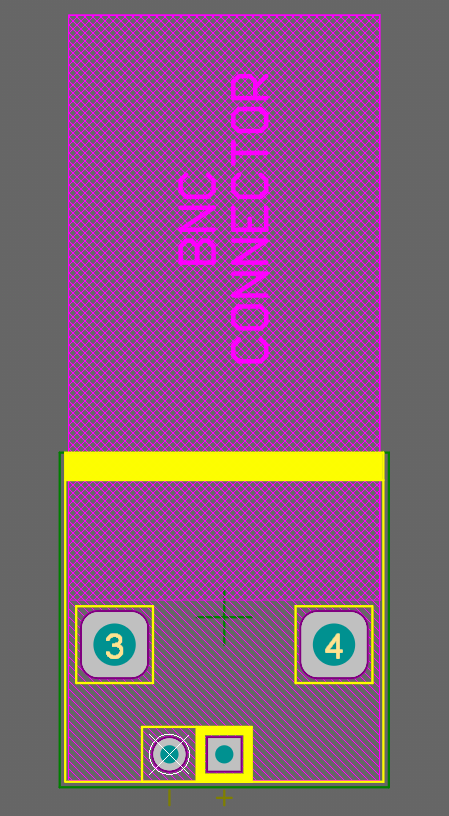
ASSETS/IMAGES/PARTS/BNC/FOOTPRINT.png
