dpmj/Bachelor_Thesis_TIK_Handheld_Device/ASSETS/IMAGES/PARTS/BUTTON GENERIC/FOOTPRINT.png

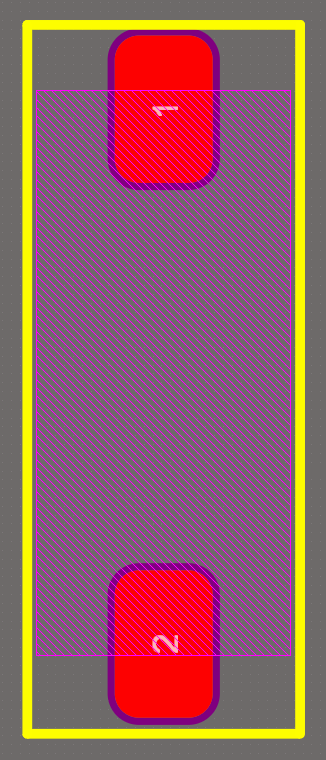
ASSETS/IMAGES/PARTS/BUTTON GENERIC/FOOTPRINT.png
