dpmj/Bachelor_Thesis_TIK_Handheld_Device/ASSETS/IMAGES/PARTS/CH340C/FOOTPRINT.png

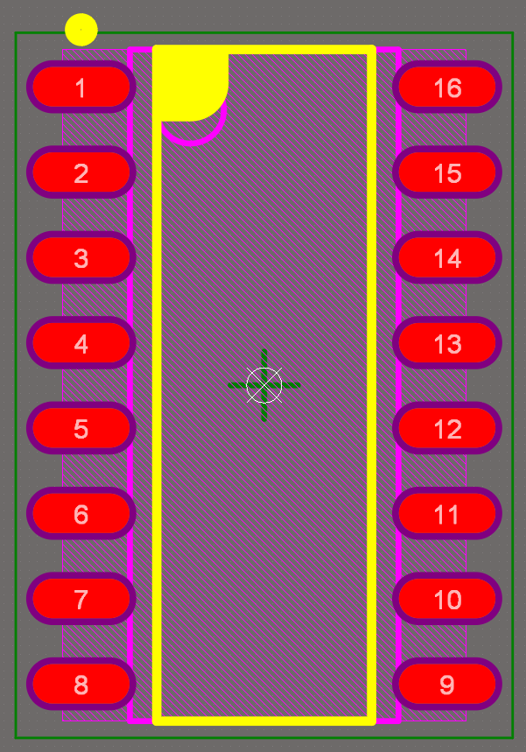
ASSETS/IMAGES/PARTS/CH340C/FOOTPRINT.png
