dpmj/Bachelor_Thesis_TIK_Handheld_Device/ASSETS/IMAGES/PARTS/CH340C/sop-16.png

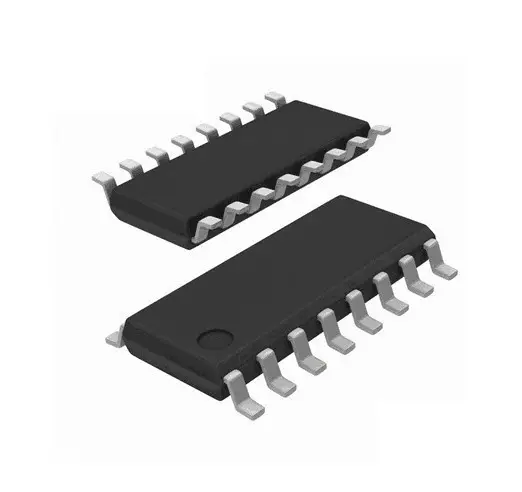
ASSETS/IMAGES/PARTS/CH340C/sop-16.png
