dpmj/Bachelor_Thesis_TIK_Handheld_Device/ASSETS/IMAGES/PARTS/DW01A/FOOTPRINT.png

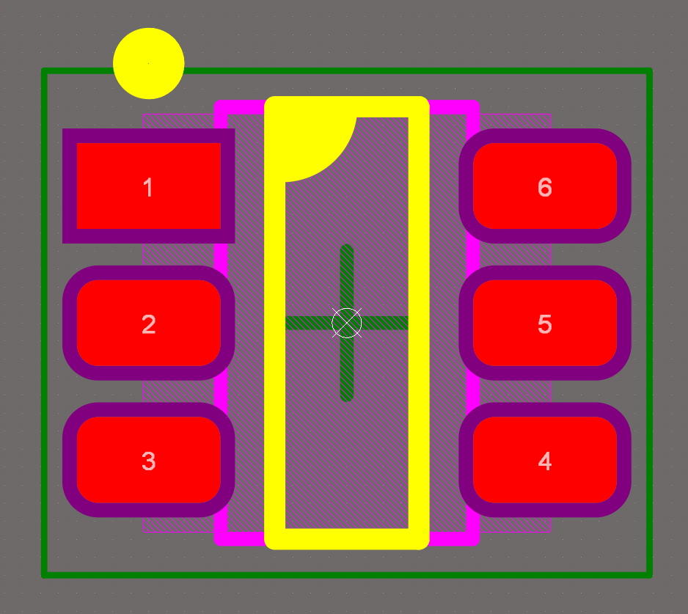
ASSETS/IMAGES/PARTS/DW01A/FOOTPRINT.png
