dpmj/Bachelor_Thesis_TIK_Handheld_Device/ASSETS/IMAGES/PARTS/DW01A/sot-23-6.jpg

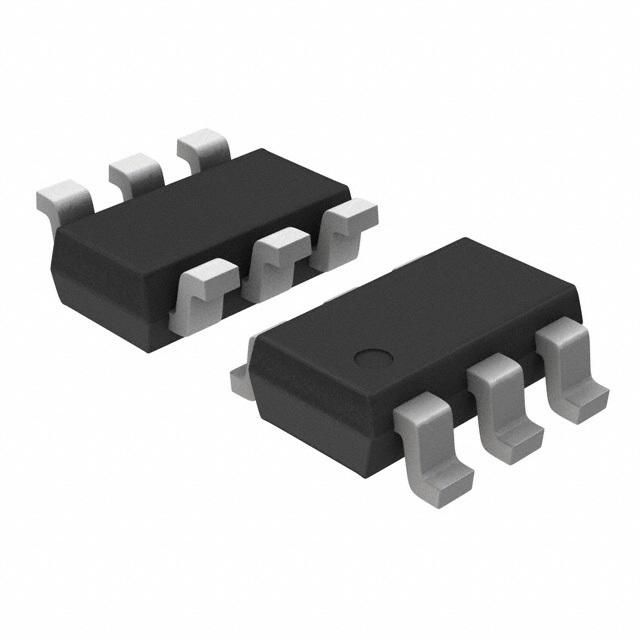
ASSETS/IMAGES/PARTS/DW01A/sot-23-6.jpg
