dpmj/Bachelor_Thesis_TIK_Handheld_Device/ASSETS/IMAGES/PARTS/ESD-prot/footprint usblc6-2sc6.png

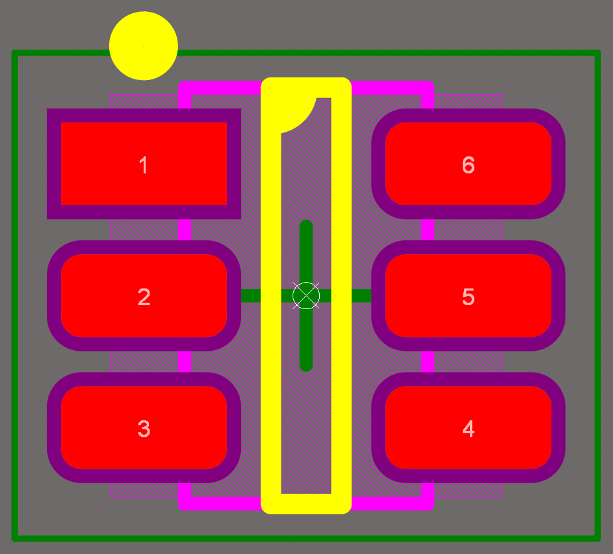
ASSETS/IMAGES/PARTS/ESD-prot/footprint usblc6-2sc6.png
