dpmj/Bachelor_Thesis_TIK_Handheld_Device/ASSETS/IMAGES/PARTS/ESD-prot/SOT_23_6.jpg

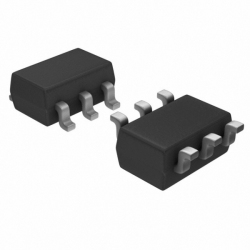
ASSETS/IMAGES/PARTS/ESD-prot/SOT_23_6.jpg
