dpmj/Bachelor_Thesis_TIK_Handheld_Device/ASSETS/IMAGES/PARTS/ESP32-WROOM-32D/ESP32-WROOM-32D_BACK.jpg

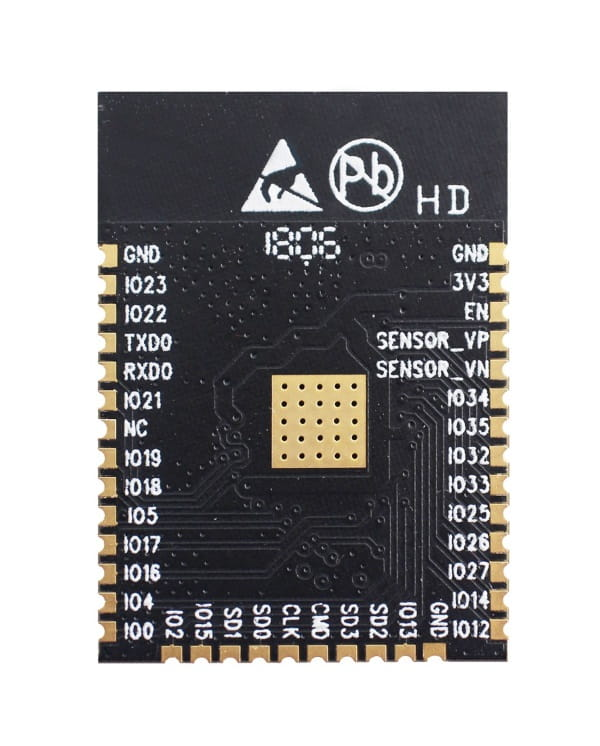
ASSETS/IMAGES/PARTS/ESP32-WROOM-32D/ESP32-WROOM-32D_BACK.jpg
