dpmj/Bachelor_Thesis_TIK_Handheld_Device/ASSETS/IMAGES/PARTS/ESP32-WROOM-32D/esp32-wroom-32d_FRONT.jpg

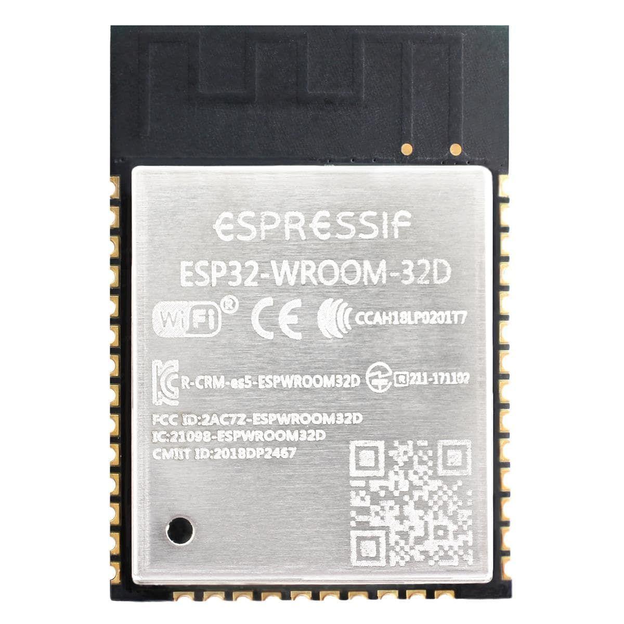
ASSETS/IMAGES/PARTS/ESP32-WROOM-32D/esp32-wroom-32d_FRONT.jpg
