dpmj/Bachelor_Thesis_TIK_Handheld_Device/ASSETS/IMAGES/PARTS/ESP32-WROOM-32D/esp32_wroom32_footprint.png

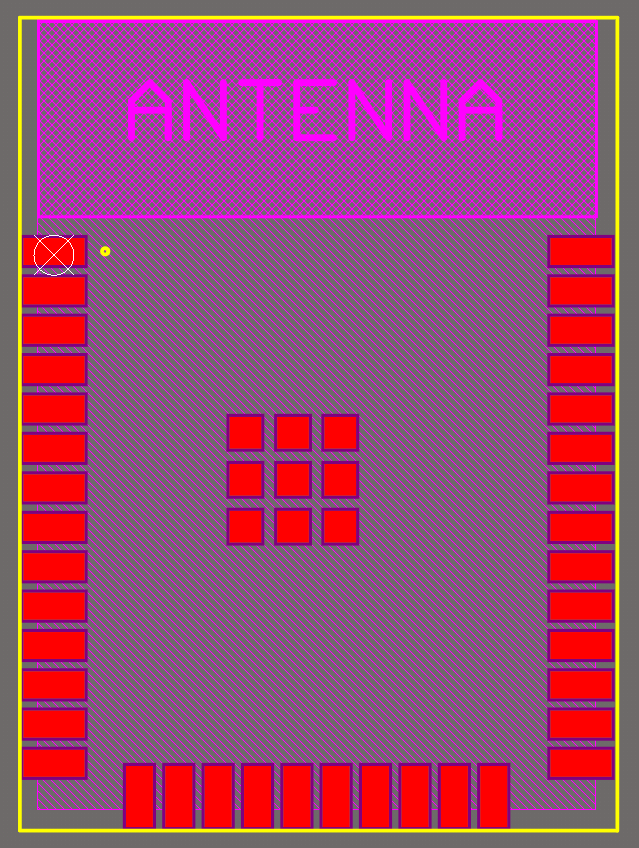
ASSETS/IMAGES/PARTS/ESP32-WROOM-32D/esp32_wroom32_footprint.png
