dpmj/Bachelor_Thesis_TIK_Handheld_Device/ASSETS/IMAGES/PARTS/FS8205A/FOOTPRINT.png

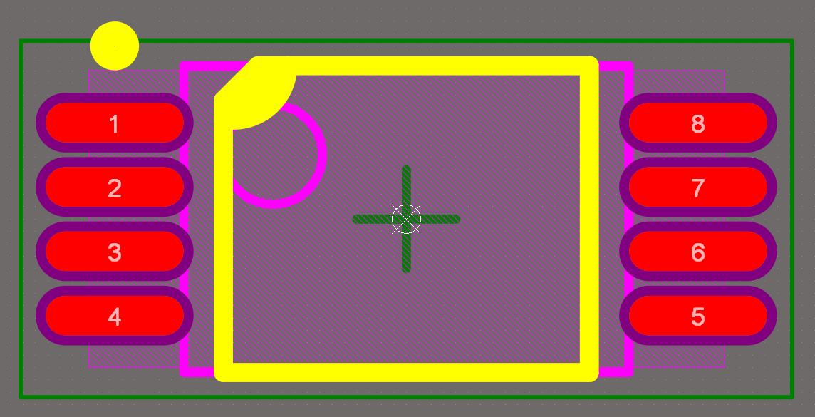
ASSETS/IMAGES/PARTS/FS8205A/FOOTPRINT.png
