dpmj/Bachelor_Thesis_TIK_Handheld_Device/ASSETS/IMAGES/PARTS/FS8205A/tssop-8-l.jpg

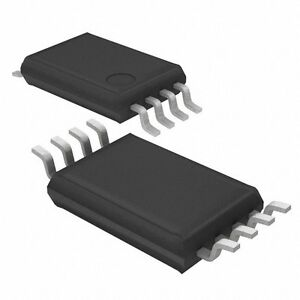
ASSETS/IMAGES/PARTS/FS8205A/tssop-8-l.jpg
