dpmj/Bachelor_Thesis_TIK_Handheld_Device/ASSETS/IMAGES/PARTS/INA219/FOOTPRINT.png

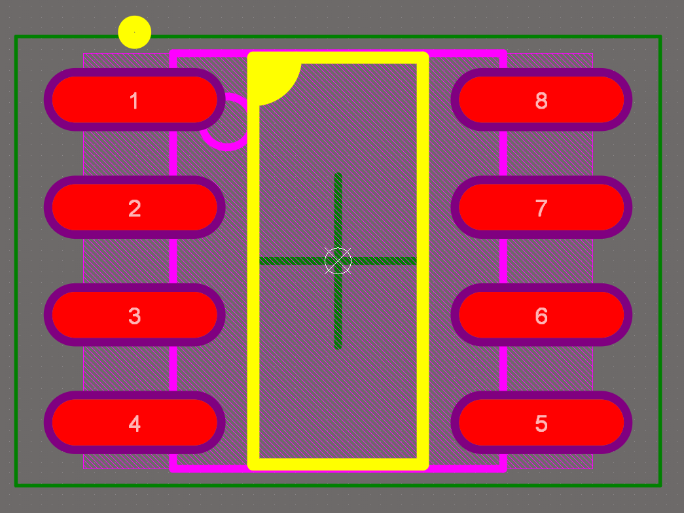
ASSETS/IMAGES/PARTS/INA219/FOOTPRINT.png
