dpmj/Bachelor_Thesis_TIK_Handheld_Device/ASSETS/IMAGES/PARTS/INA219/soic-8.webp

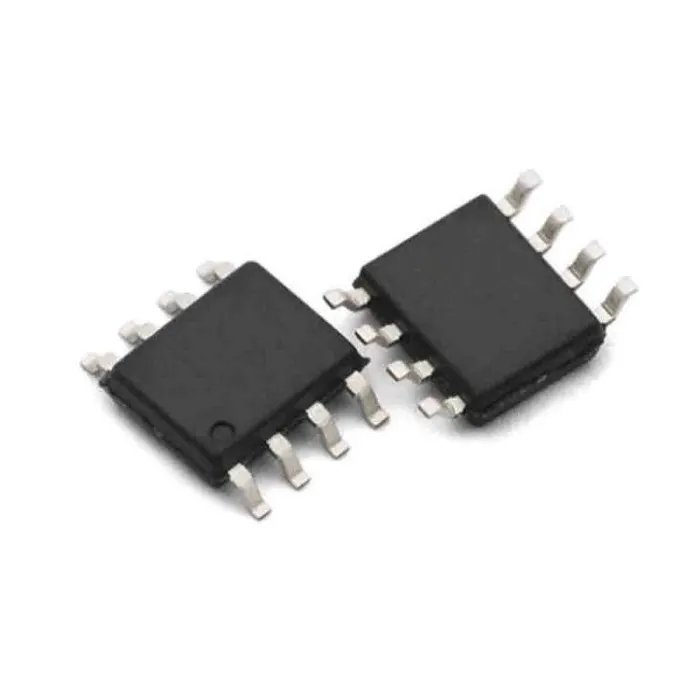
ASSETS/IMAGES/PARTS/INA219/soic-8.webp
