dpmj/Bachelor_Thesis_TIK_Handheld_Device/ASSETS/IMAGES/PARTS/INA219/soic-8_reder.png

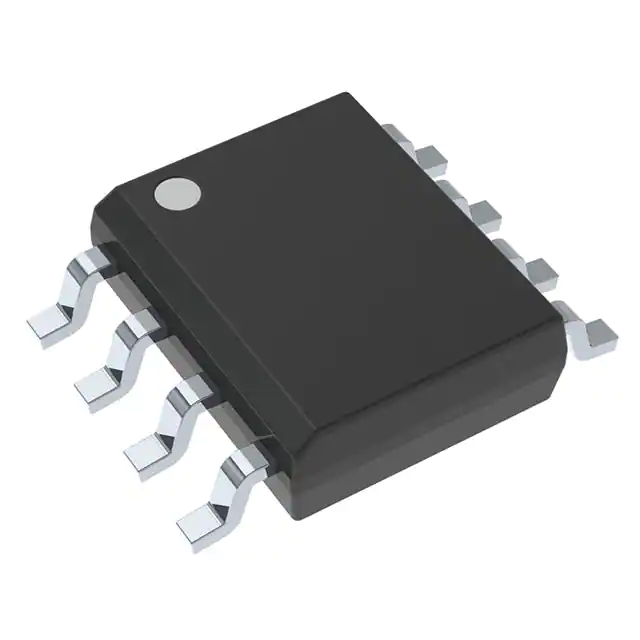
ASSETS/IMAGES/PARTS/INA219/soic-8_reder.png
