dpmj/Bachelor_Thesis_TIK_Handheld_Device/ASSETS/IMAGES/PARTS/JACK/3214.png

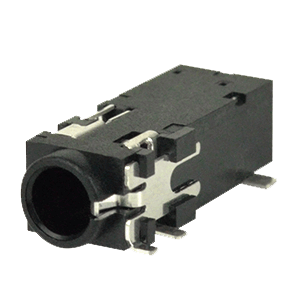
ASSETS/IMAGES/PARTS/JACK/3214.png
