dpmj/Bachelor_Thesis_TIK_Handheld_Device/ASSETS/IMAGES/PARTS/JACK/FOOTPRINT.png

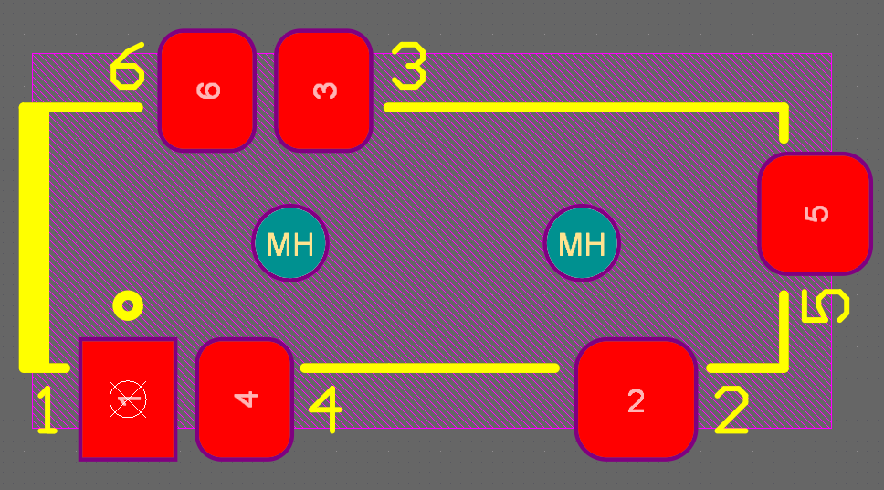
ASSETS/IMAGES/PARTS/JACK/FOOTPRINT.png
