dpmj/Bachelor_Thesis_TIK_Handheld_Device/ASSETS/IMAGES/PARTS/JACK/PINOUT_order.png

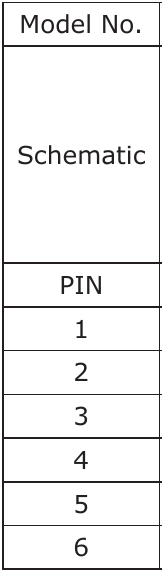
ASSETS/IMAGES/PARTS/JACK/PINOUT_order.png
