dpmj/Bachelor_Thesis_TIK_Handheld_Device/ASSETS/IMAGES/PARTS/JACK/PLUG.png

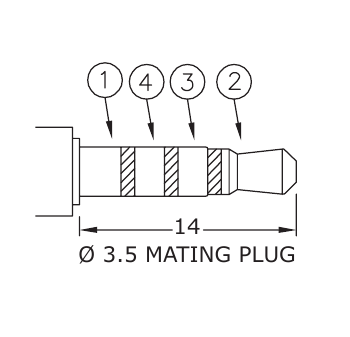
ASSETS/IMAGES/PARTS/JACK/PLUG.png
