dpmj/Bachelor_Thesis_TIK_Handheld_Device/ASSETS/IMAGES/PARTS/JACK/SJ-43516-SMT .webp

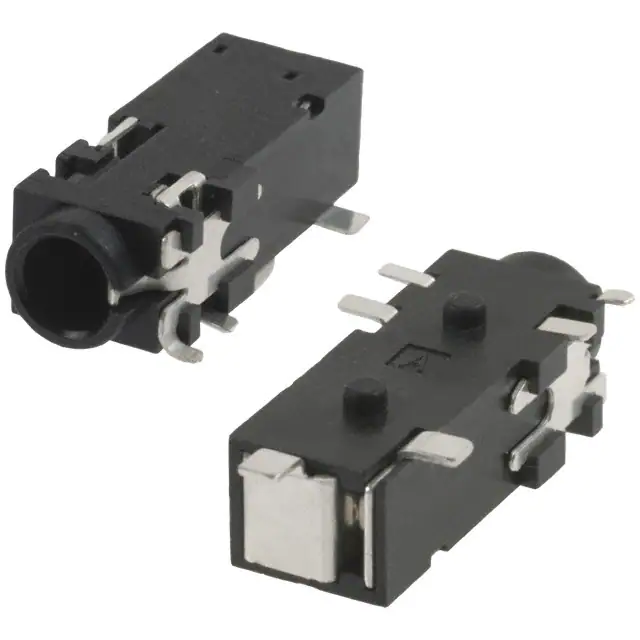
ASSETS/IMAGES/PARTS/JACK/SJ-43516-SMT .webp
