dpmj/Bachelor_Thesis_TIK_Handheld_Device/ASSETS/IMAGES/PARTS/K1-1502SA-01/FOOTPRINT.png

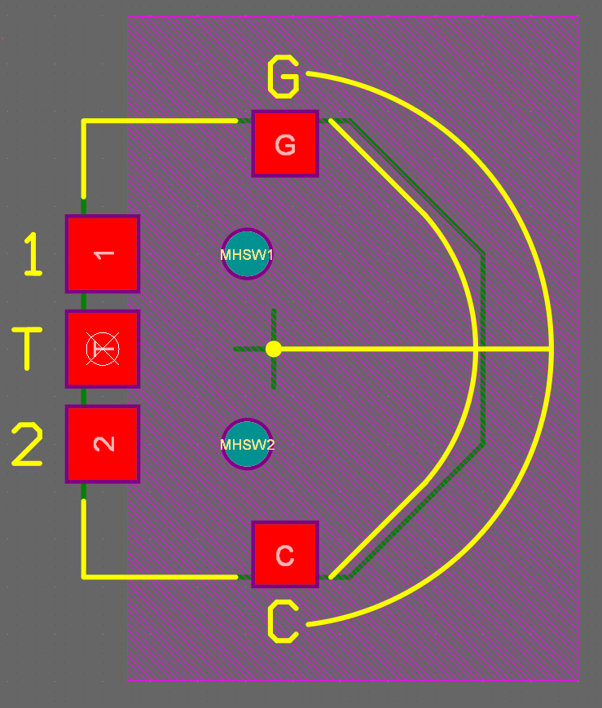
ASSETS/IMAGES/PARTS/K1-1502SA-01/FOOTPRINT.png
