dpmj/Bachelor_Thesis_TIK_Handheld_Device/ASSETS/IMAGES/PARTS/K1-1502SA-01/K1-1502SA-01.jpg

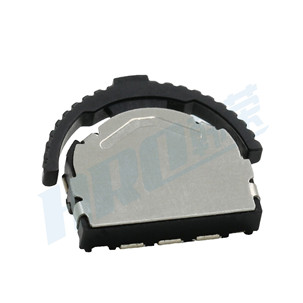
ASSETS/IMAGES/PARTS/K1-1502SA-01/K1-1502SA-01.jpg
