dpmj/Bachelor_Thesis_TIK_Handheld_Device/ASSETS/IMAGES/PARTS/LMV358/FOOTPRINT.png

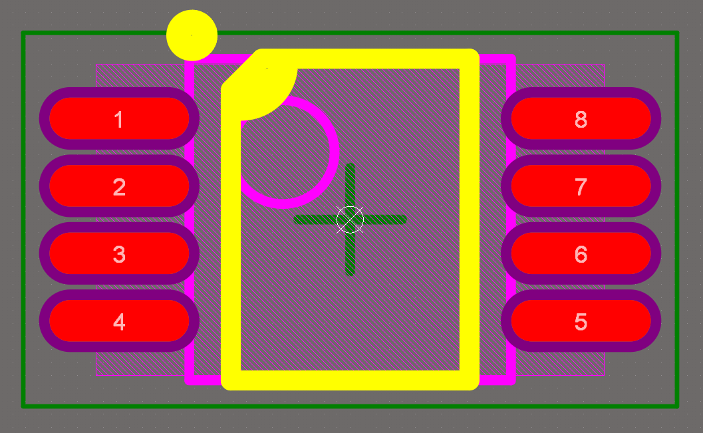
ASSETS/IMAGES/PARTS/LMV358/FOOTPRINT.png
