dpmj/Bachelor_Thesis_TIK_Handheld_Device/ASSETS/IMAGES/PARTS/LMV358/MSOP-8.jpg

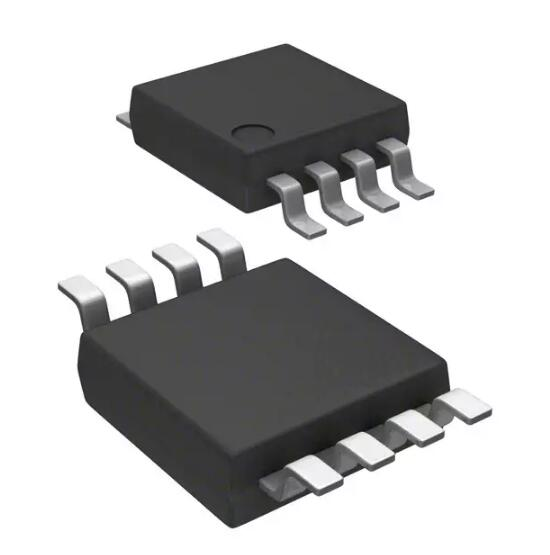
ASSETS/IMAGES/PARTS/LMV358/MSOP-8.jpg
