dpmj/Bachelor_Thesis_TIK_Handheld_Device/ASSETS/IMAGES/PARTS/LTC4060/FOOTPRINT.png

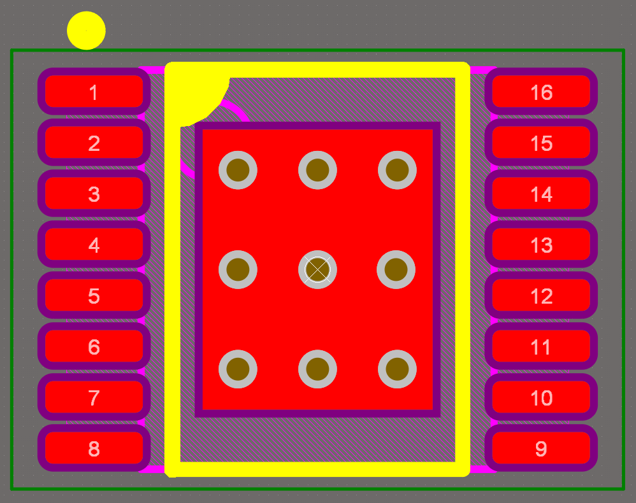
ASSETS/IMAGES/PARTS/LTC4060/FOOTPRINT.png
