dpmj/Bachelor_Thesis_TIK_Handheld_Device/ASSETS/IMAGES/PARTS/LTC4060/TSSOP-16-pOWER.jpg

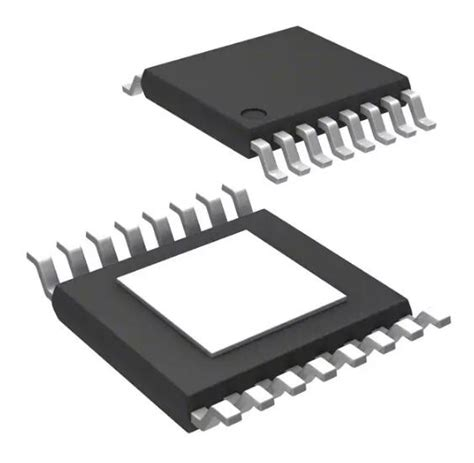
ASSETS/IMAGES/PARTS/LTC4060/TSSOP-16-pOWER.jpg
