dpmj/Bachelor_Thesis_TIK_Handheld_Device/ASSETS/IMAGES/PARTS/MJD210/DPAK_TO-252_001.jpg

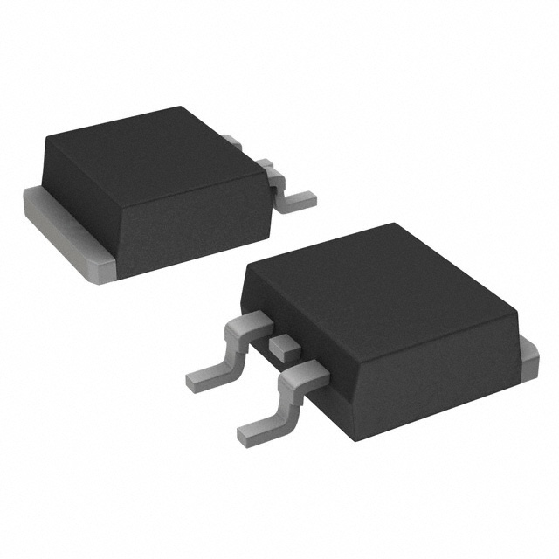
ASSETS/IMAGES/PARTS/MJD210/DPAK_TO-252_001.jpg
