dpmj/Bachelor_Thesis_TIK_Handheld_Device/ASSETS/IMAGES/PARTS/MJD210/FOOTPRINT.png

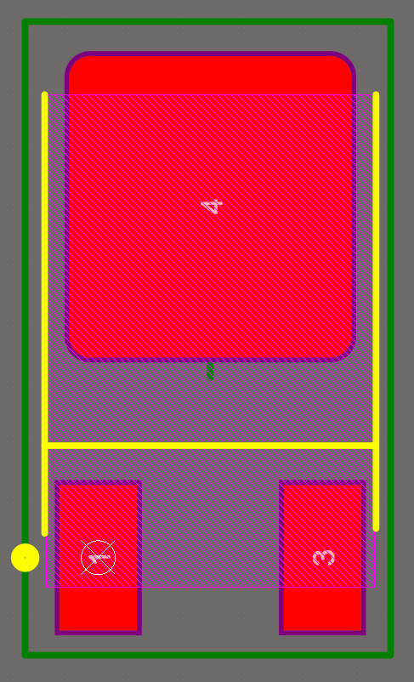
ASSETS/IMAGES/PARTS/MJD210/FOOTPRINT.png
