dpmj/Bachelor_Thesis_TIK_Handheld_Device/ASSETS/IMAGES/PARTS/MJD210/FOOTPRINT_2.png

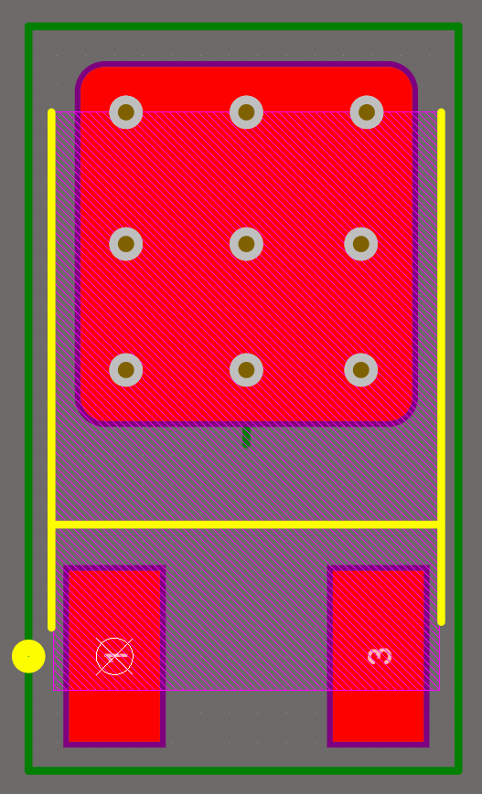
ASSETS/IMAGES/PARTS/MJD210/FOOTPRINT_2.png
