dpmj/Bachelor_Thesis_TIK_Handheld_Device/ASSETS/IMAGES/PARTS/MJD210/s-l300.jpg

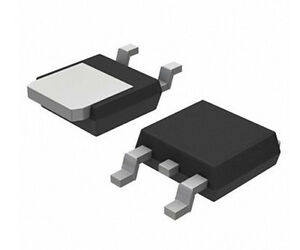
ASSETS/IMAGES/PARTS/MJD210/s-l300.jpg
