dpmj/Bachelor_Thesis_TIK_Handheld_Device/ASSETS/IMAGES/PARTS/NCP562/FOOTPRINT.png

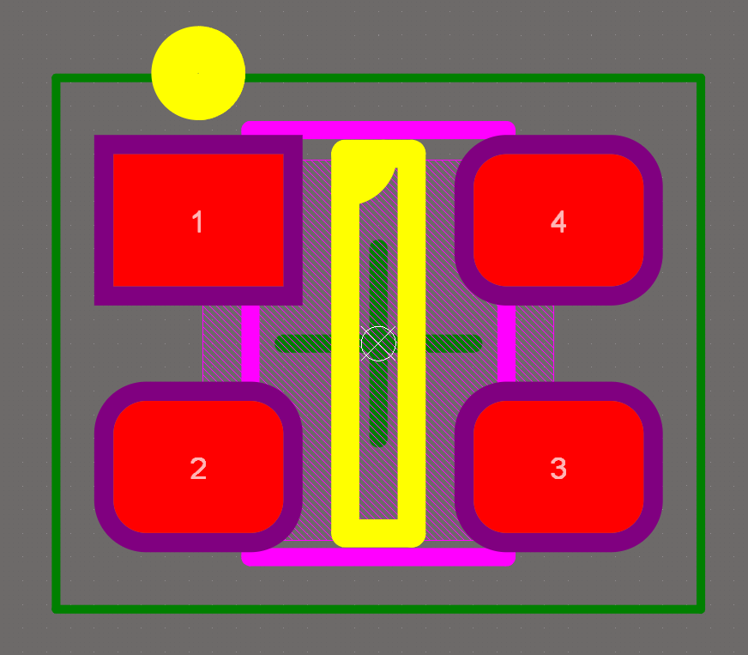
ASSETS/IMAGES/PARTS/NCP562/FOOTPRINT.png
