dpmj/Bachelor_Thesis_TIK_Handheld_Device/ASSETS/IMAGES/PARTS/NCP562/sc70-4.jpg

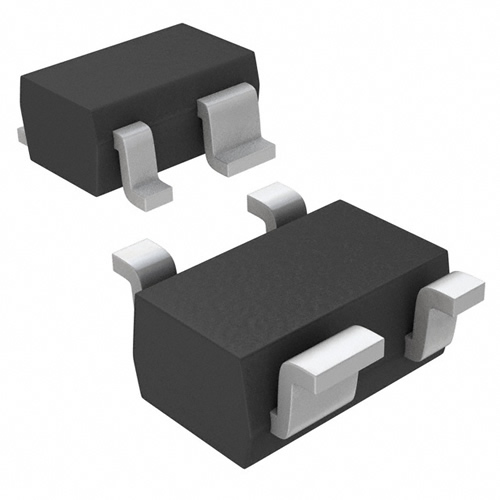
ASSETS/IMAGES/PARTS/NCP562/sc70-4.jpg
