dpmj/Bachelor_Thesis_TIK_Handheld_Device/ASSETS/IMAGES/PARTS/NCP562/sc82-ab.jpg

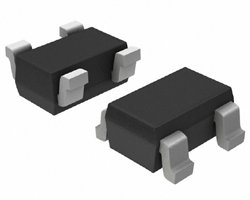
ASSETS/IMAGES/PARTS/NCP562/sc82-ab.jpg
