dpmj/Bachelor_Thesis_TIK_Handheld_Device/ASSETS/IMAGES/PARTS/RJ11/0438600026.webp

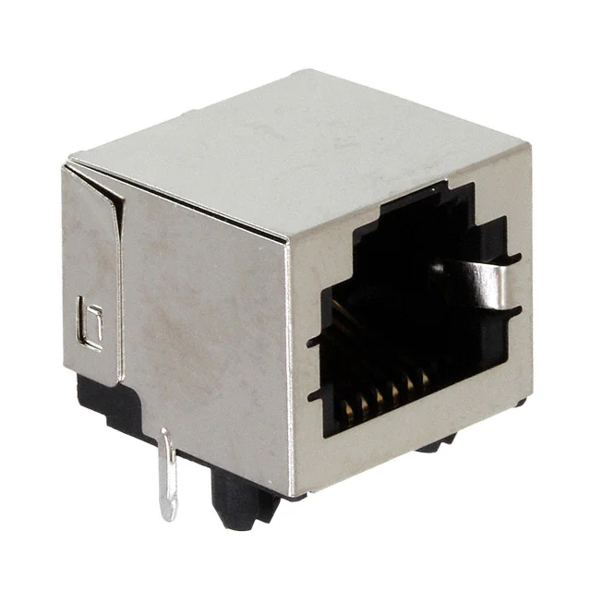
ASSETS/IMAGES/PARTS/RJ11/0438600026.webp
