dpmj/Bachelor_Thesis_TIK_Handheld_Device/ASSETS/IMAGES/PARTS/RJ11/FOOTPRINT.png

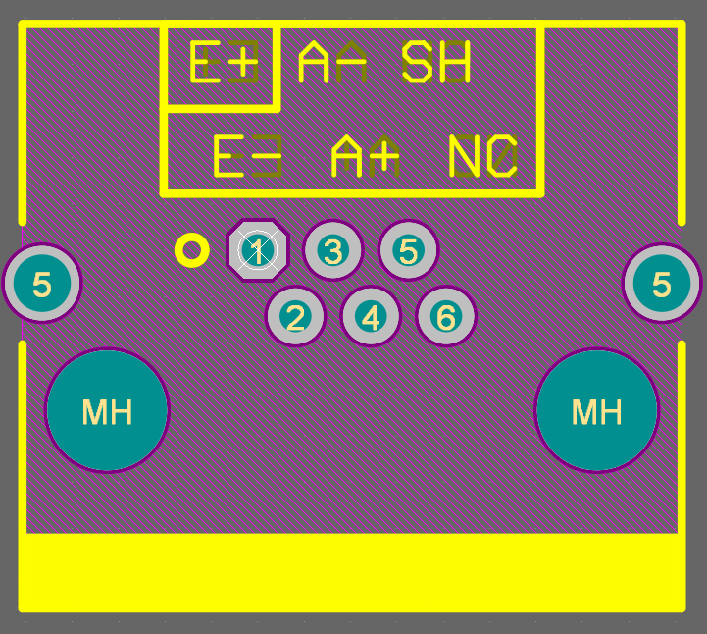
ASSETS/IMAGES/PARTS/RJ11/FOOTPRINT.png
