dpmj/Bachelor_Thesis_TIK_Handheld_Device/ASSETS/IMAGES/PARTS/ROTARY ENCODERS/horizontal.png

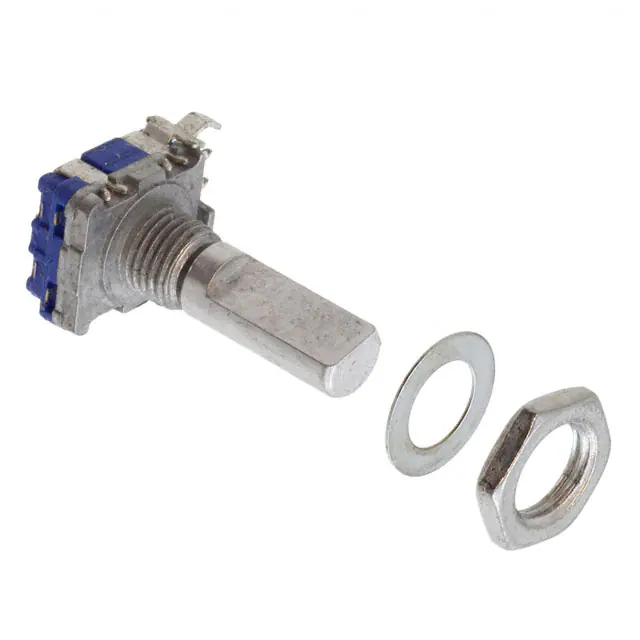
ASSETS/IMAGES/PARTS/ROTARY ENCODERS/horizontal.png
