dpmj/Bachelor_Thesis_TIK_Handheld_Device/ASSETS/IMAGES/PARTS/ROTARY ENCODERS/HORIZONTAL_FOOTPRINT.png

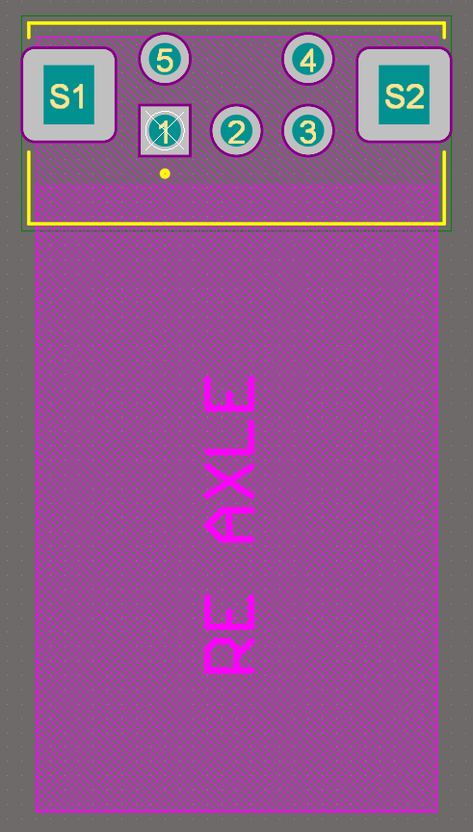
ASSETS/IMAGES/PARTS/ROTARY ENCODERS/HORIZONTAL_FOOTPRINT.png
