dpmj/Bachelor_Thesis_TIK_Handheld_Device/ASSETS/IMAGES/PARTS/ROTARY ENCODERS/vertical.png

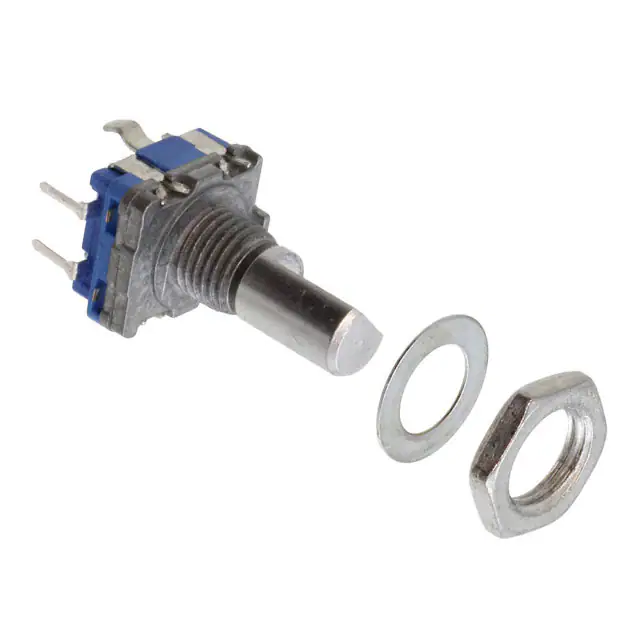
ASSETS/IMAGES/PARTS/ROTARY ENCODERS/vertical.png
