dpmj/Bachelor_Thesis_TIK_Handheld_Device/ASSETS/IMAGES/PARTS/ROTARY ENCODERS/VERTICAL_FOOTPRINT.png

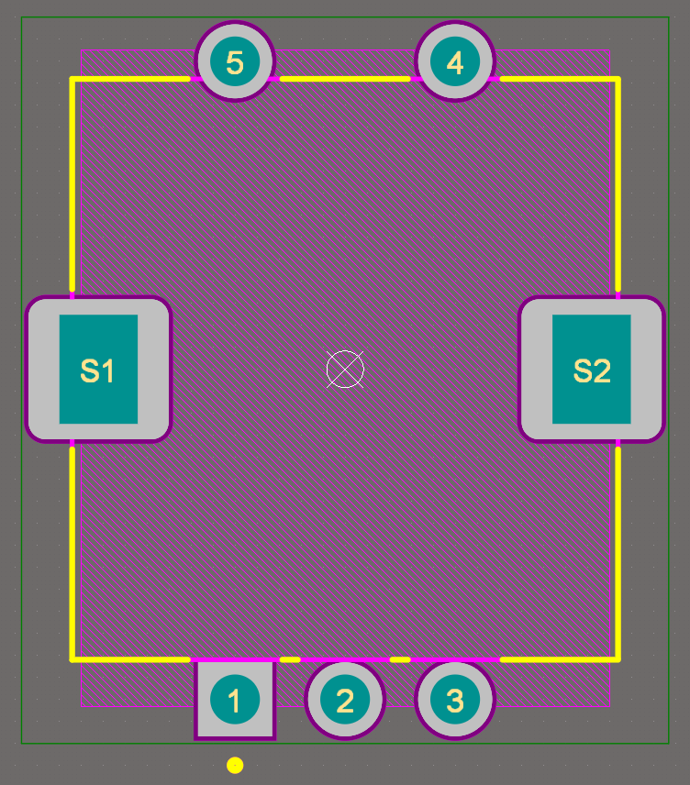
ASSETS/IMAGES/PARTS/ROTARY ENCODERS/VERTICAL_FOOTPRINT.png
