dpmj/Bachelor_Thesis_TIK_Handheld_Device/ASSETS/IMAGES/PARTS/TFT LCD/back.jpg

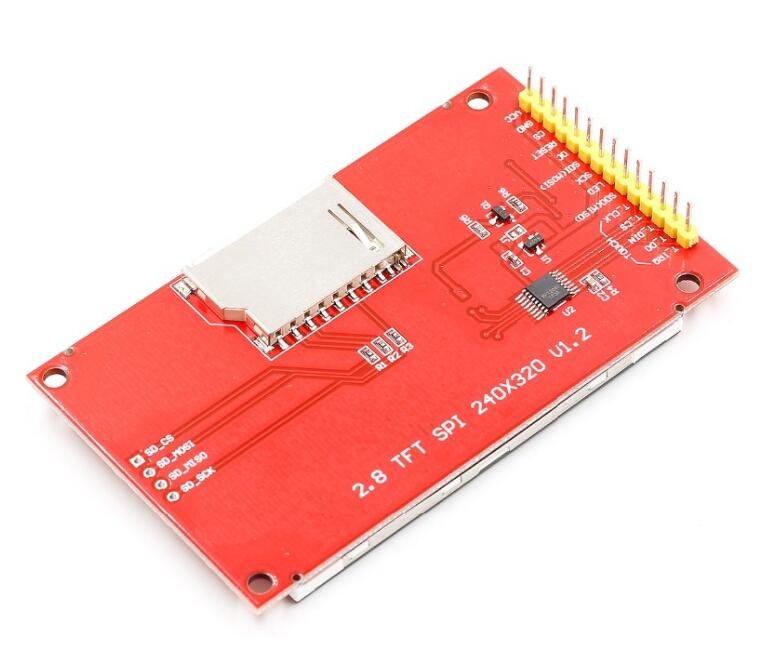
ASSETS/IMAGES/PARTS/TFT LCD/back.jpg
