dpmj/Bachelor_Thesis_TIK_Handheld_Device/ASSETS/IMAGES/PARTS/TFT LCD/FOOTPRINT.png

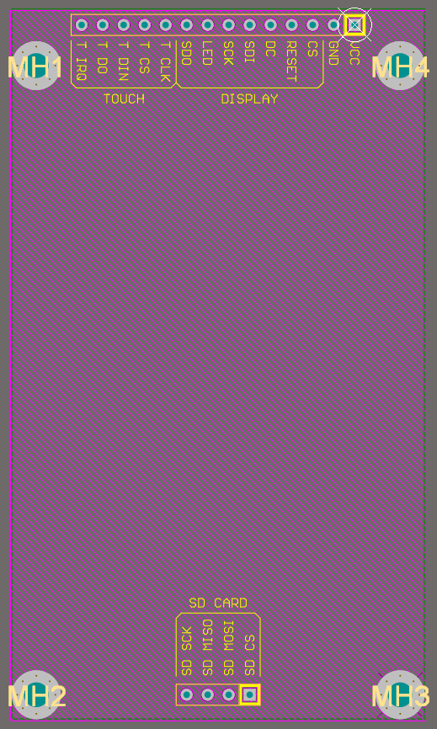
ASSETS/IMAGES/PARTS/TFT LCD/FOOTPRINT.png
