dpmj/Bachelor_Thesis_TIK_Handheld_Device/ASSETS/IMAGES/PARTS/TFT LCD/front.jpg

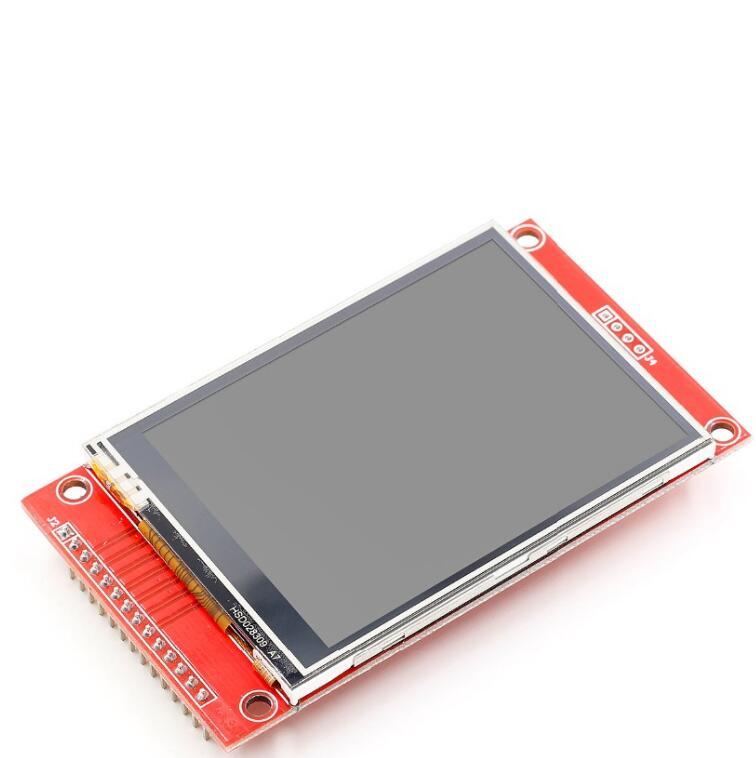
ASSETS/IMAGES/PARTS/TFT LCD/front.jpg
