dpmj/Bachelor_Thesis_TIK_Handheld_Device/ASSETS/IMAGES/PARTS/TFT LCD/tft lcd.jpg

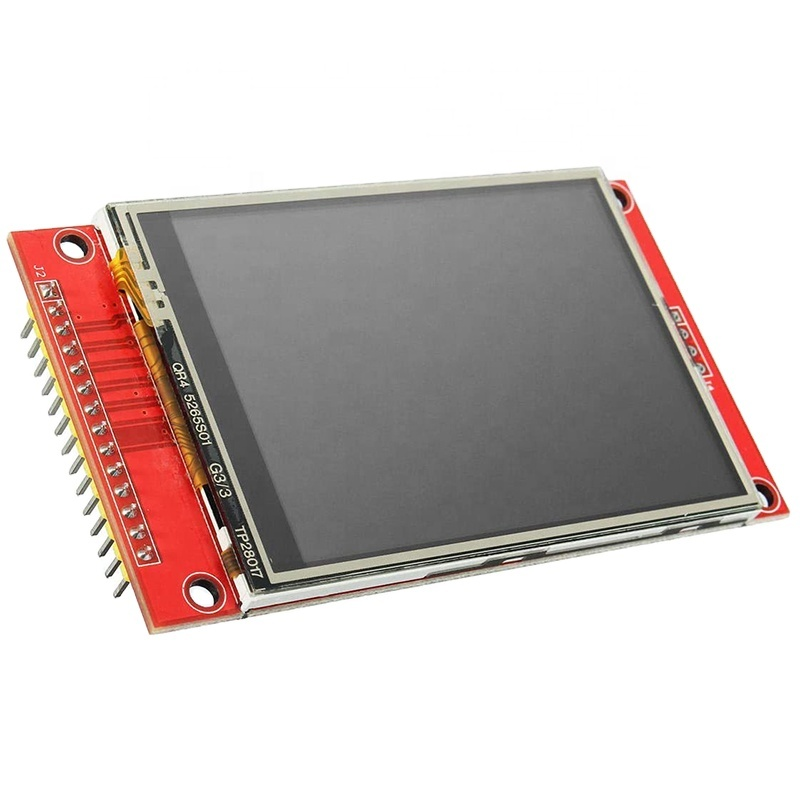
ASSETS/IMAGES/PARTS/TFT LCD/tft lcd.jpg
