dpmj/Bachelor_Thesis_TIK_Handheld_Device/ASSETS/IMAGES/PARTS/TP4056/sop-8 pad.jpg

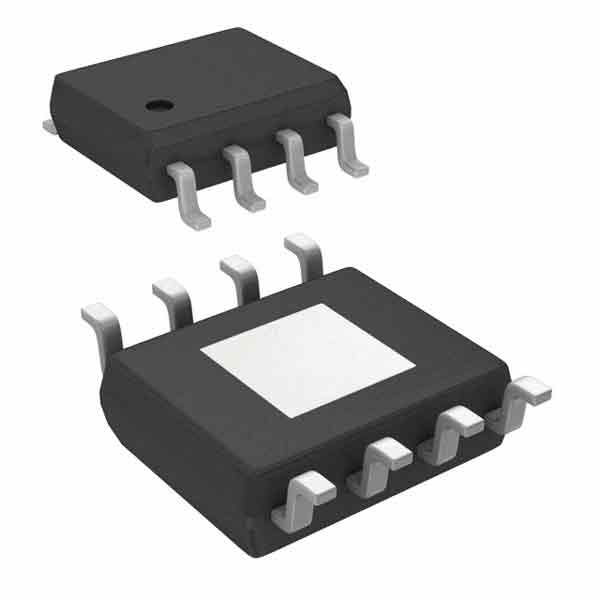
ASSETS/IMAGES/PARTS/TP4056/sop-8 pad.jpg
