dpmj/Bachelor_Thesis_TIK_Handheld_Device/ASSETS/IMAGES/PARTS/USB/usb-mini-b.png

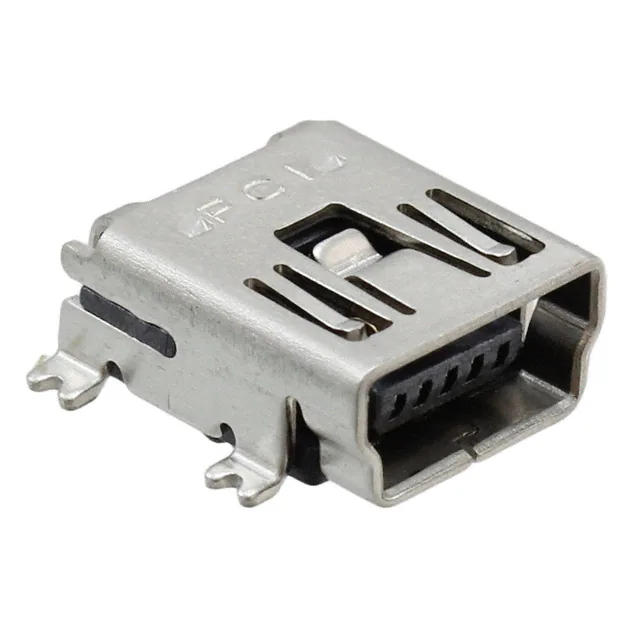
ASSETS/IMAGES/PARTS/USB/usb-mini-b.png
