dpmj/Bachelor_Thesis_TIK_Handheld_Device/ASSETS/IMAGES/PARTS/USB/usb_mini_b_footprint.png

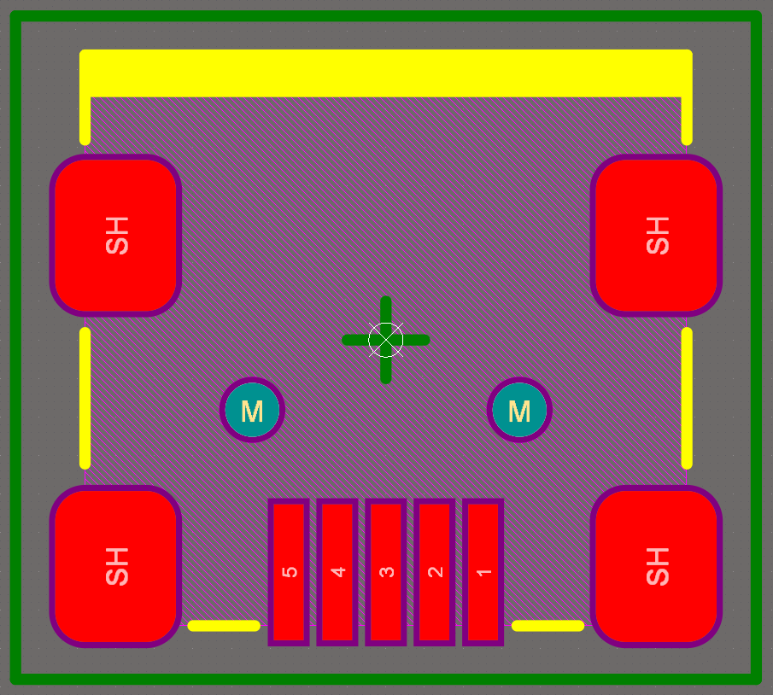
ASSETS/IMAGES/PARTS/USB/usb_mini_b_footprint.png
