dpmj/Bachelor_Thesis_TIK_Handheld_Device/OUTPUT/BOM/BOM_29062022.jpg

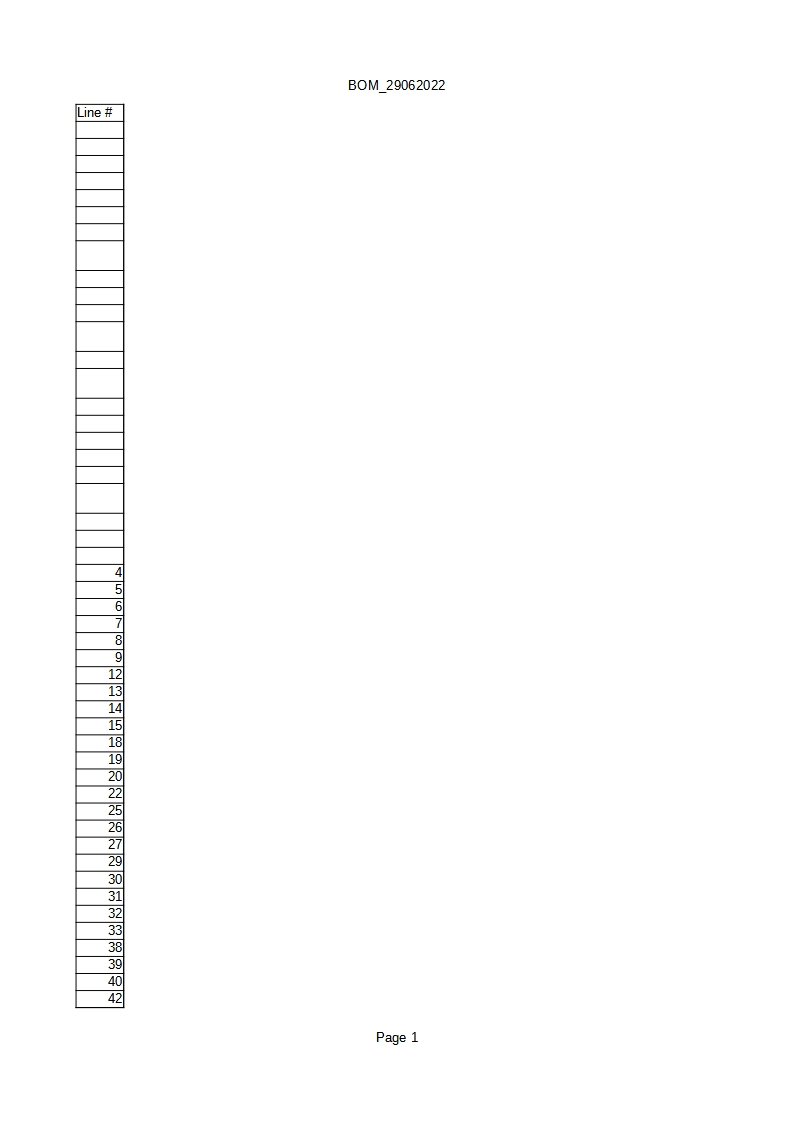
OUTPUT/BOM/BOM_29062022.jpg
