dpmj/Bachelor_Thesis_TIK_Handheld_Device/ASSETS/3D/Rotary encoder vertical generic/EC11B-SW-Vert-20F-blue.step

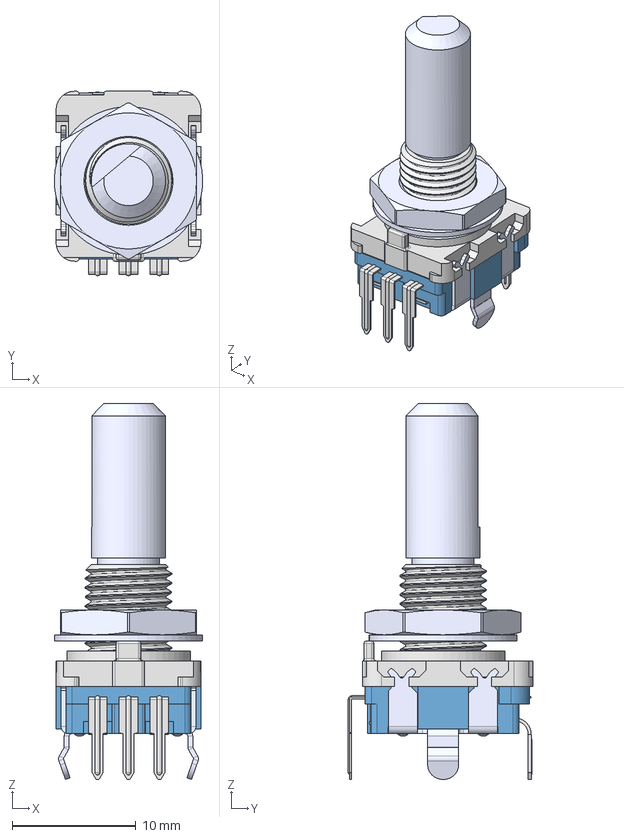
[picture p130: CAD file, 2025-09-22]
ASSETS/3D/Rotary encoder vertical generic/EC11B-SW-Vert-20F-blue.step
12.0 x 14.9 x 30.4 mm
