dpmj/Bachelor_Thesis_TIK_Handheld_Device/ASSETS/3D/SC-82AB/sc_82ab.step

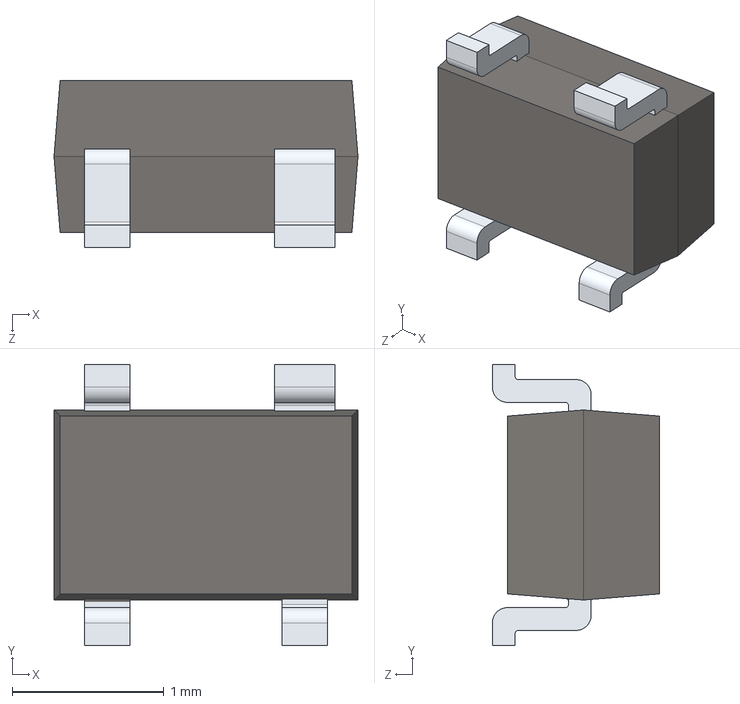
[picture p131: CAD file, 2025-09-22]
ASSETS/3D/SC-82AB/sc_82ab.step
2.00 x 1.85 x 1.10 mm
