dpmj/Bachelor_Thesis_TIK_Handheld_Device/ASSETS/3D/SPACER/Standoff mf - M5 x 30 across flats 8mm.step

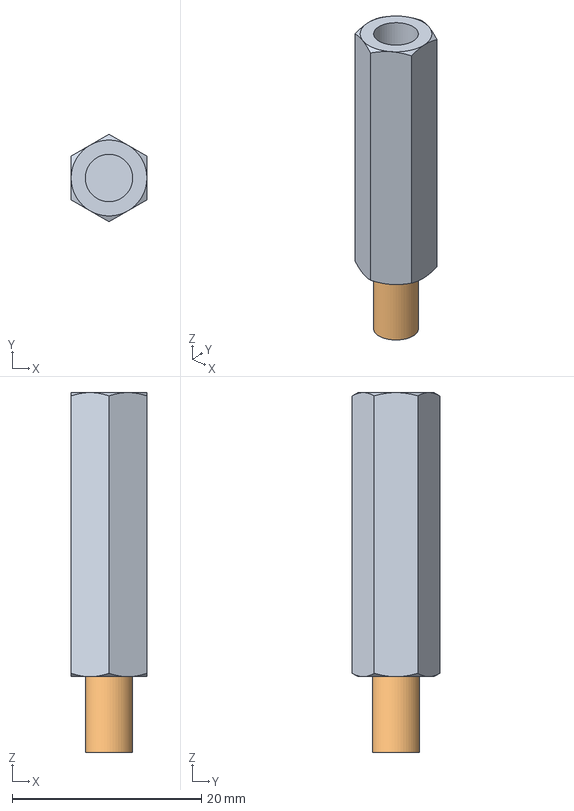
[picture p132: CAD file, 2025-09-22]
ASSETS/3D/SPACER/Standoff mf - M5 x 30 across flats 8mm.step
8.00 x 9.24 x 38.0 mm
