dpmj/Bachelor_Thesis_TIK_Handheld_Device/ASSETS/3D/THREADED INSERT/F2-B-M3-Pressfit_2.STEP

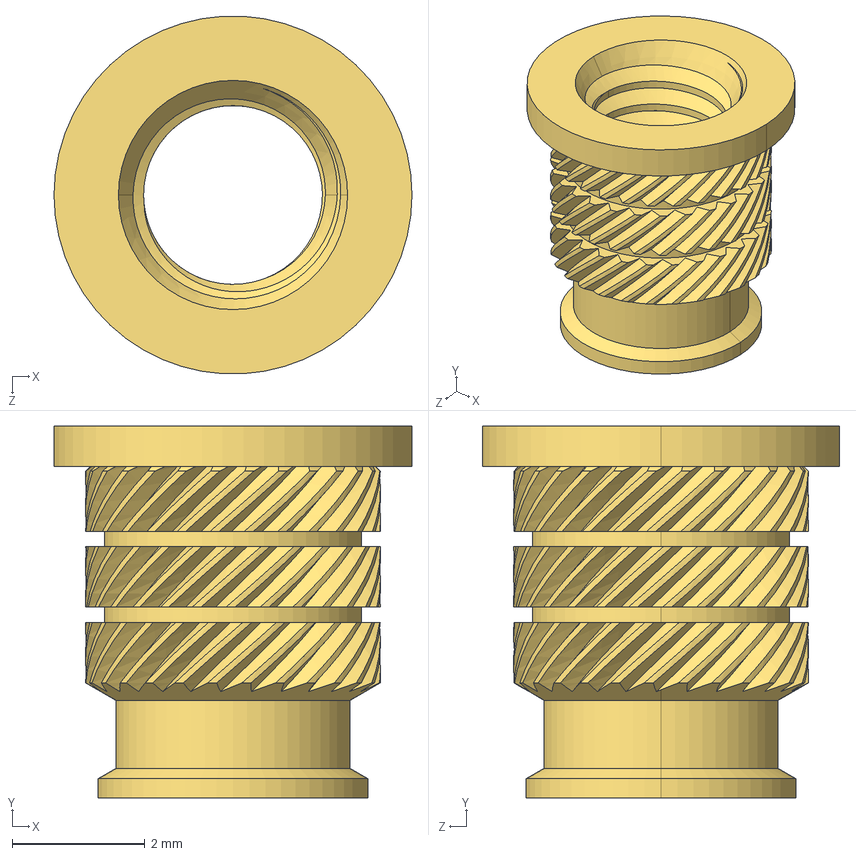
[picture p133: CAD file, 2025-09-22]
ASSETS/3D/THREADED INSERT/F2-B-M3-Pressfit_2.STEP
5.40 x 5.60 x 5.39 mm
