dpmj/Bachelor_Thesis_TIK_Handheld_Device/ASSETS/3D/TO-252 DPAK/User Library-DPAK_TO-252AA.step

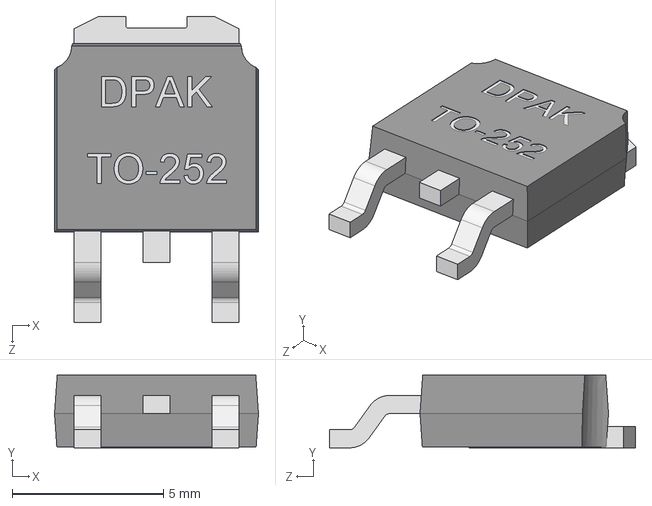
[picture p134: CAD file, 2025-09-22]
ASSETS/3D/TO-252 DPAK/User Library-DPAK_TO-252AA.step
6.73 x 2.40 x 10.1 mm
