dpmj/Bachelor_Thesis_TIK_Handheld_Device/ASSETS/TIK_CASE/CASE_PARTS/TOP_COVER.SLDPRT

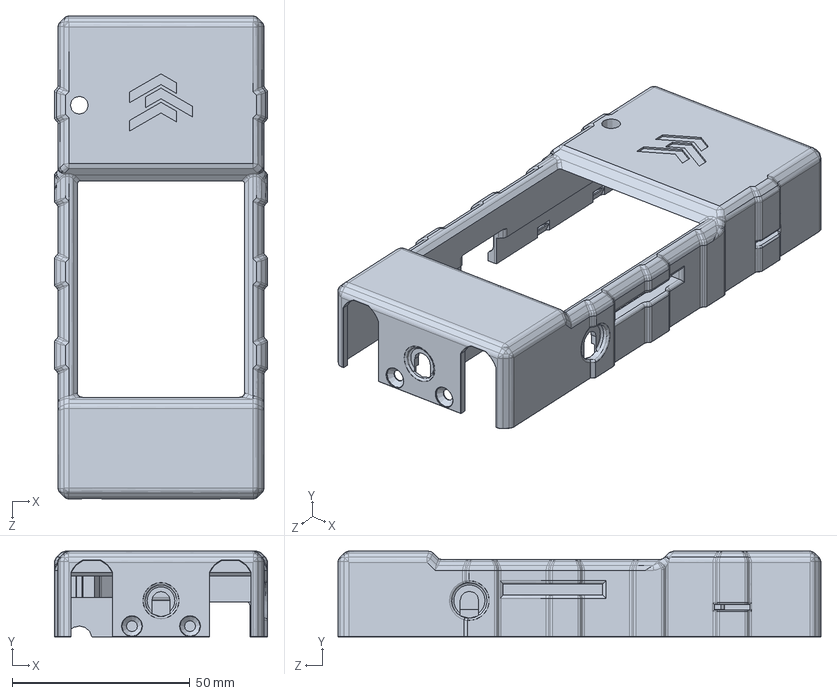
[picture p135: CAD file, 2025-09-22]
ASSETS/TIK_CASE/CASE_PARTS/TOP_COVER.SLDPRT
60.0 x 24.1 x 136.0 mm
