dpmj/Bachelor_Thesis_TIK_Handheld_Device/ASSETS/TIK_CASE/EXPORT/GCODE/CE3PRO_TOP_COVER_AVELLANADA_ALREVES.3mf

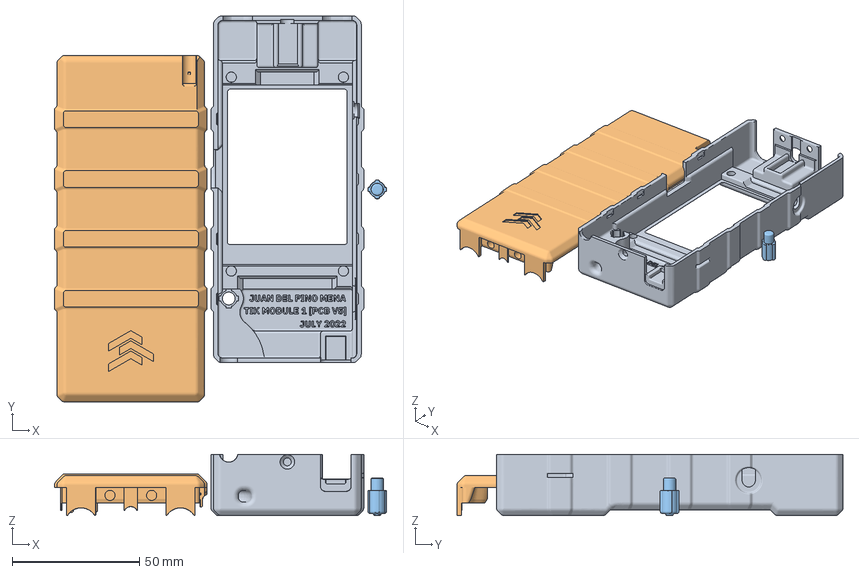
[picture p136: CAD file, 2025-09-22]
ASSETS/TIK_CASE/EXPORT/GCODE/CE3PRO_TOP_COVER_AVELLANADA_ALREVES.3mf
130.4 x 151.5 x 24.1 mm
TOP_COVER_AVELLANADA.STL
BOTTOM_COVER.STL
BUTTON.STL
