dpmj/Bachelor_Thesis_TIK_Handheld_Device/ASSETS/TIK_CASE/EXPORT/STL/BUTTON.STL

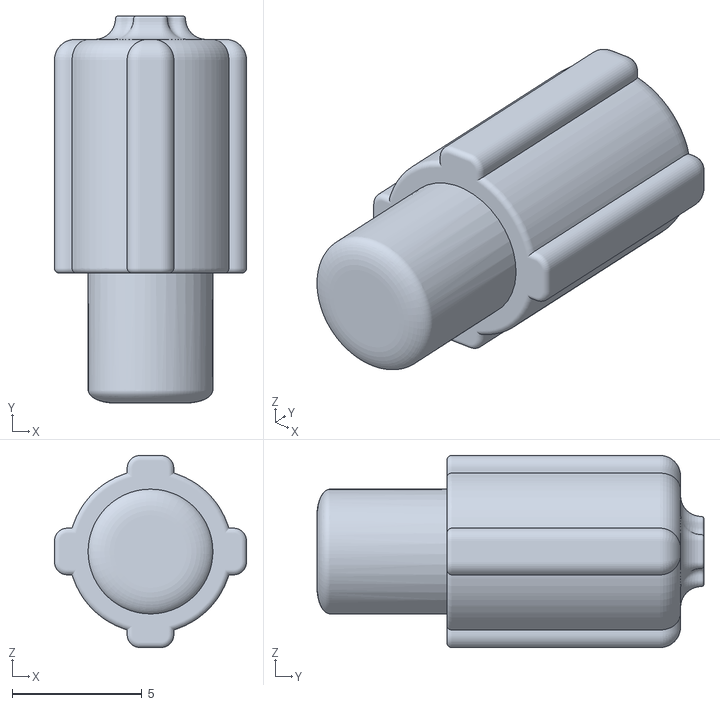
[picture p137: CAD file, 2025-09-22]
ASSETS/TIK_CASE/EXPORT/STL/BUTTON.STL
7.40 x 14.9 x 7.40
