dpmj/Bachelor_Thesis_TIK_Handheld_Device/ASSETS/TIK_CASE/FUTURE/CUI_DEVICES_UJC-VP-3-SMT-TR/CUI_DEVICES_UJC-VP-3-SMT-TR.sldprt

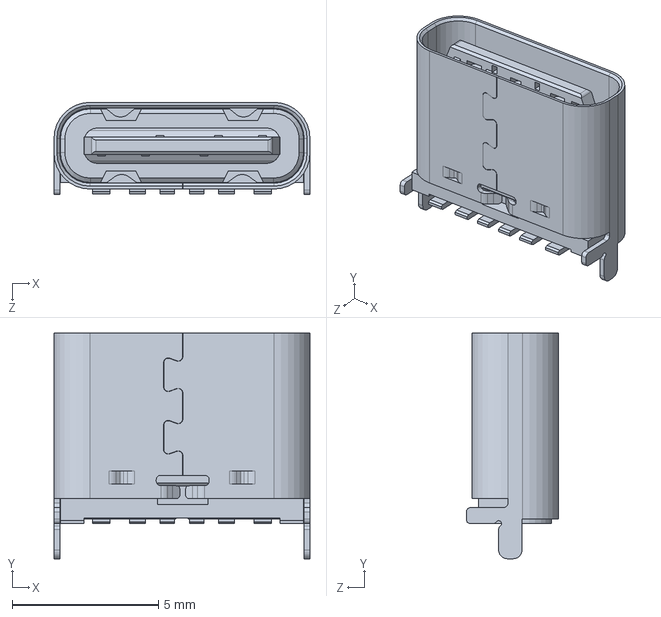
[picture p138: CAD file, 2025-09-22]
ASSETS/TIK_CASE/FUTURE/CUI_DEVICES_UJC-VP-3-SMT-TR/CUI_DEVICES_UJC-VP-3-SMT-TR.sldprt
8.74 x 7.70 x 3.15 mm
