dpmj/Bachelor_Thesis_TIK_Handheld_Device/ASSETS/TIK_CASE/FUTURE/PISTOL.SLDPRT

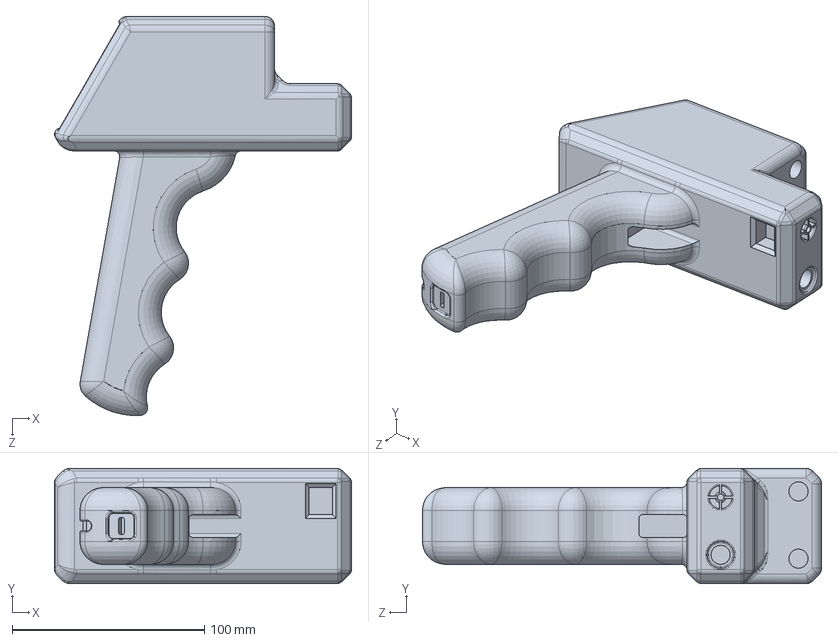
[picture p139: CAD file, 2025-09-22]
ASSETS/TIK_CASE/FUTURE/PISTOL.SLDPRT
154.5 x 60.0 x 207.6 mm
