dpmj/Bachelor_Thesis_TIK_Handheld_Device/ASSETS/TIK_CASE/PCB/PARTS/GLASS.SLDPRT

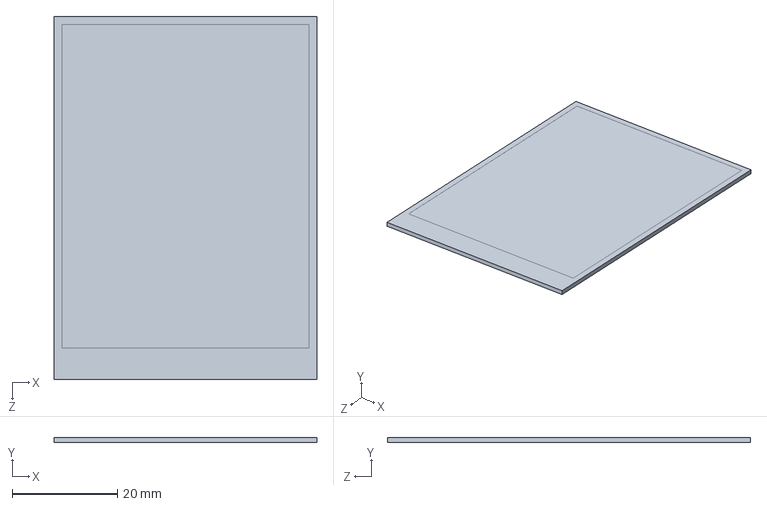
[picture p140: CAD file, 2025-09-22]
ASSETS/TIK_CASE/PCB/PARTS/GLASS.SLDPRT
50.0 x 1.00 x 69.0 mm
