dpmj/Bachelor_Thesis_TIK_Handheld_Device/ASSETS/TIK_CASE/PROTO/BNC Connector/BNC Connector.stl

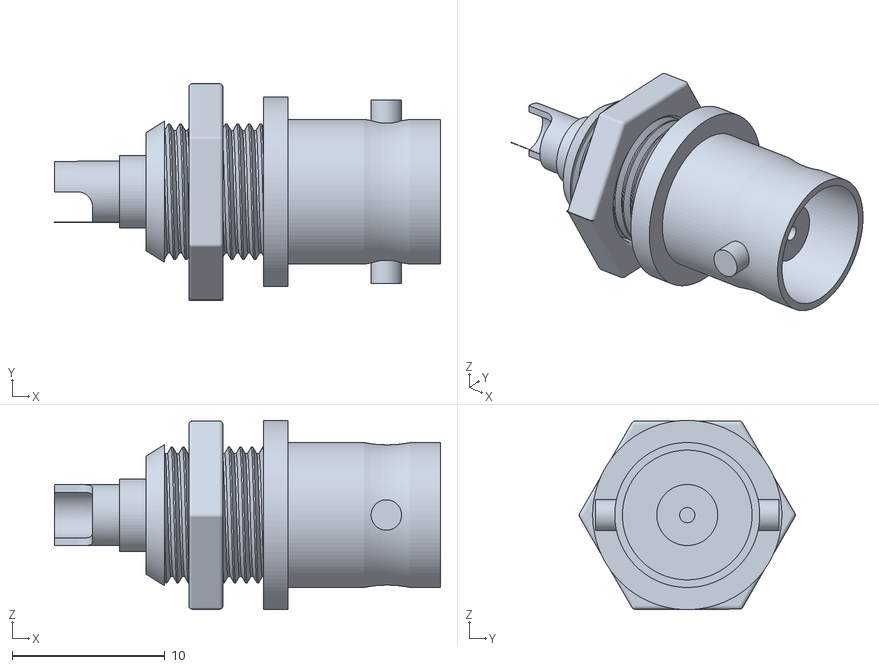
[picture p141: CAD file, 2025-09-22]
ASSETS/TIK_CASE/PROTO/BNC Connector/BNC Connector.stl
25.3 x 14.2 x 12.4
