dpmj/Bachelor_Thesis_TIK_Handheld_Device/ASSETS/TIK_CASE/PROTO/bnc-connector--1.snapshot.1/ACX1046-ND_BNC.STEP

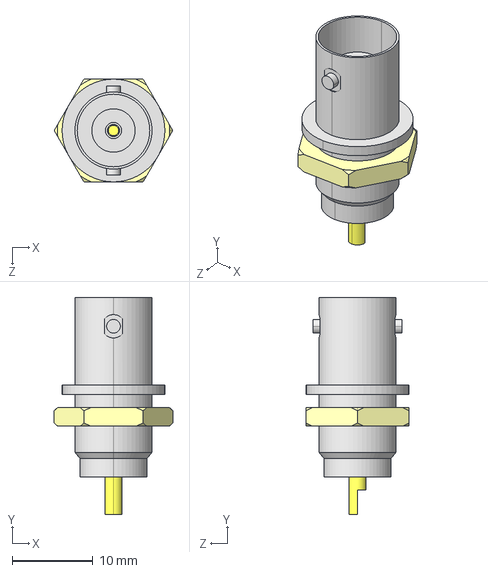
[picture p142: CAD file, 2025-09-22]
ASSETS/TIK_CASE/PROTO/bnc-connector--1.snapshot.1/ACX1046-ND_BNC.STEP
14.7 x 26.8 x 12.7 mm
