dpmj/Bachelor_Thesis_TIK_Handheld_Device/ASSETS/TIK_CASE/PROTO/SCREEN.SLDPRT

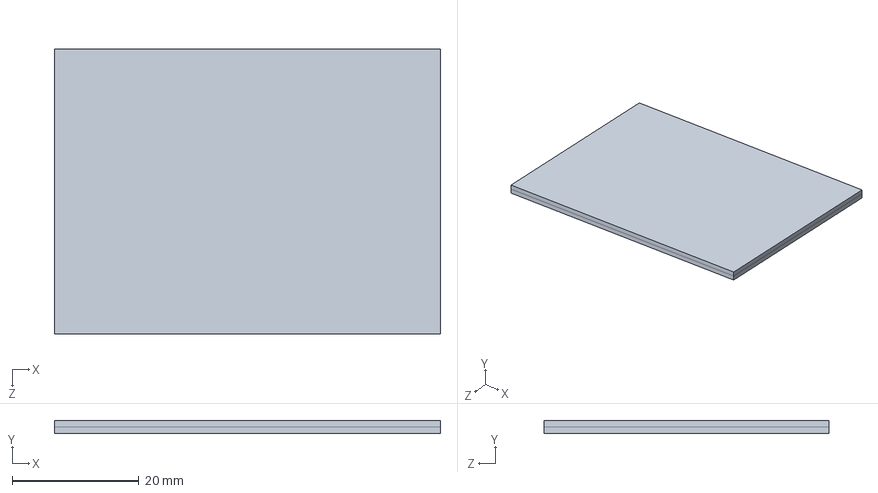
[picture p143: CAD file, 2025-09-22]
ASSETS/TIK_CASE/PROTO/SCREEN.SLDPRT
61.0 x 2.00 x 45.0 mm
