dpmj/Bachelor_Thesis_TIK_Handheld_Device/ASSETS/TIK_CASE/STYLUS/ds-lite-stylus.SLDPRT

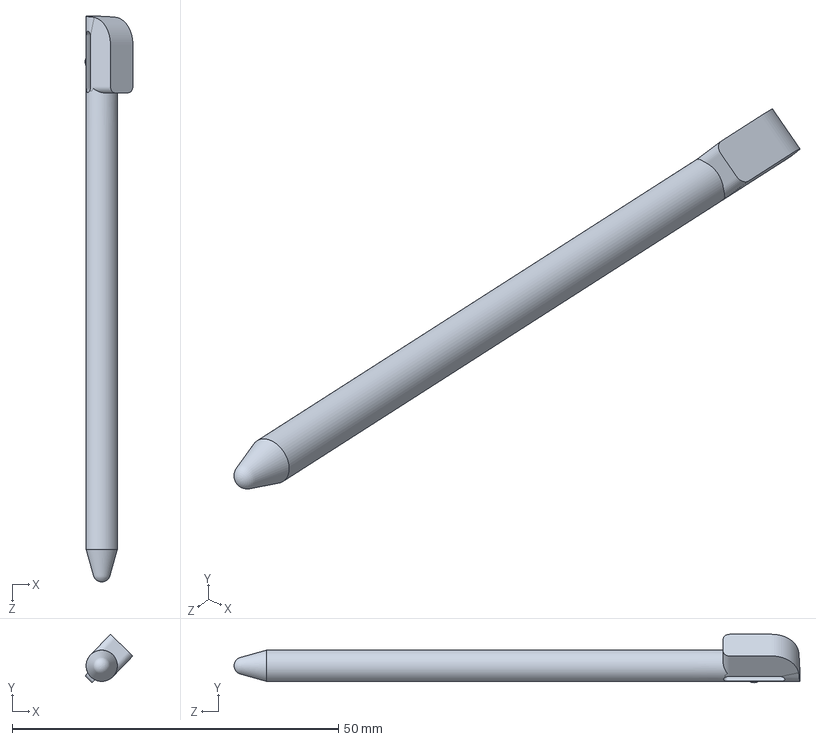
[picture p144: CAD file, 2025-09-22]
ASSETS/TIK_CASE/STYLUS/ds-lite-stylus.SLDPRT
7.34 x 7.44 x 86.8 mm
