dpmj/Bachelor_Thesis_TIK_Handheld_Device/ASSETS/TIK_CASE/TOOLING/SPACER/spacer_m3_7cm.STEP

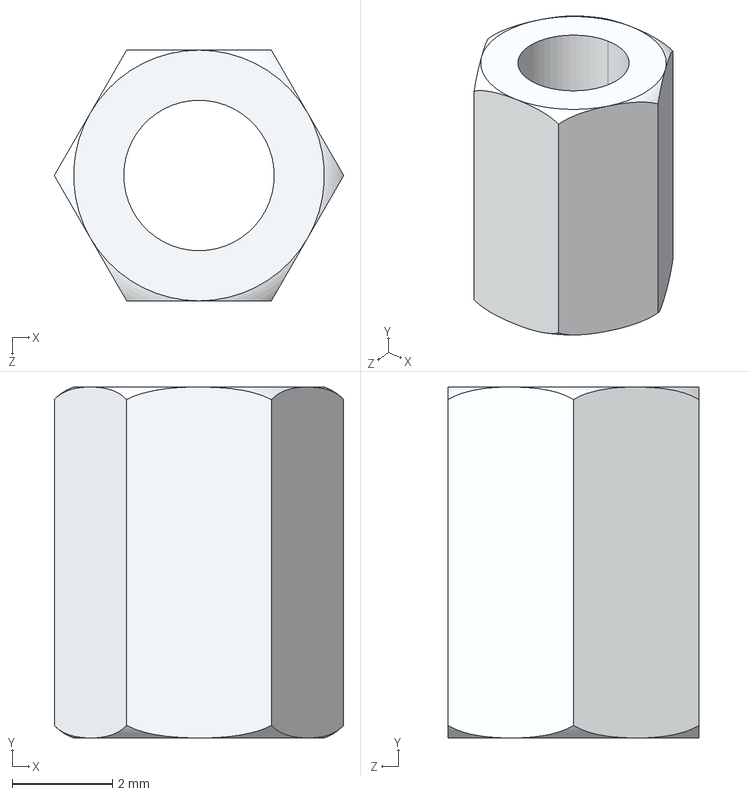
[picture p145: CAD file, 2025-09-22]
ASSETS/TIK_CASE/TOOLING/SPACER/spacer_m3_7cm.STEP
5.77 x 7.00 x 5.00 mm
