dpmj/Bachelor_Thesis_TIK_Handheld_Device/ASSETS/TIK_CASE/TOOLING/THREADED INSERT/F2-B-M3-Pressfit_2.SLDPRT

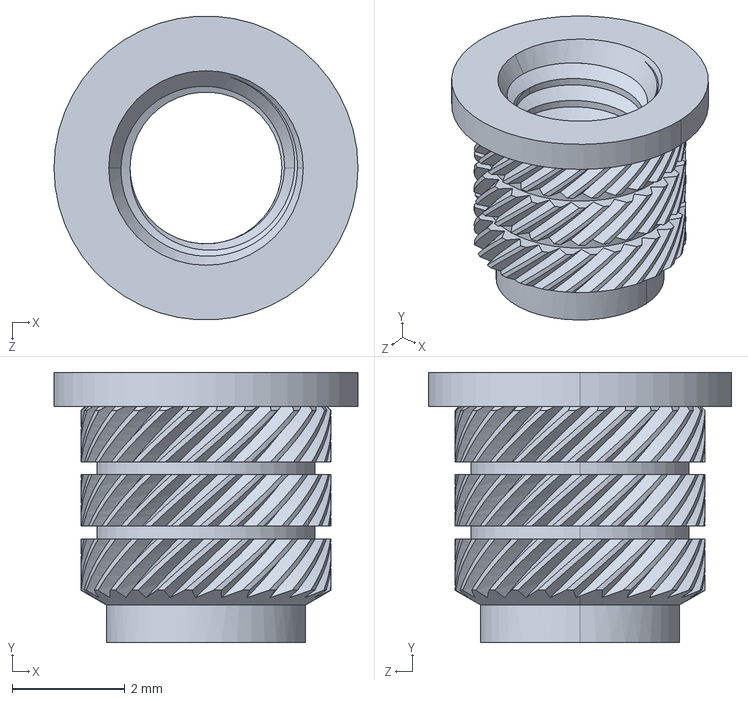
[picture p146: CAD file, 2025-09-22]
ASSETS/TIK_CASE/TOOLING/THREADED INSERT/F2-B-M3-Pressfit_2.SLDPRT
5.40 x 4.80 x 5.38 mm
