dpmj/Bachelor_Thesis_TIK_Handheld_Device/ASSETS/3D/Alps Alpine SLLB/SLLB510100_SCALED.STEP

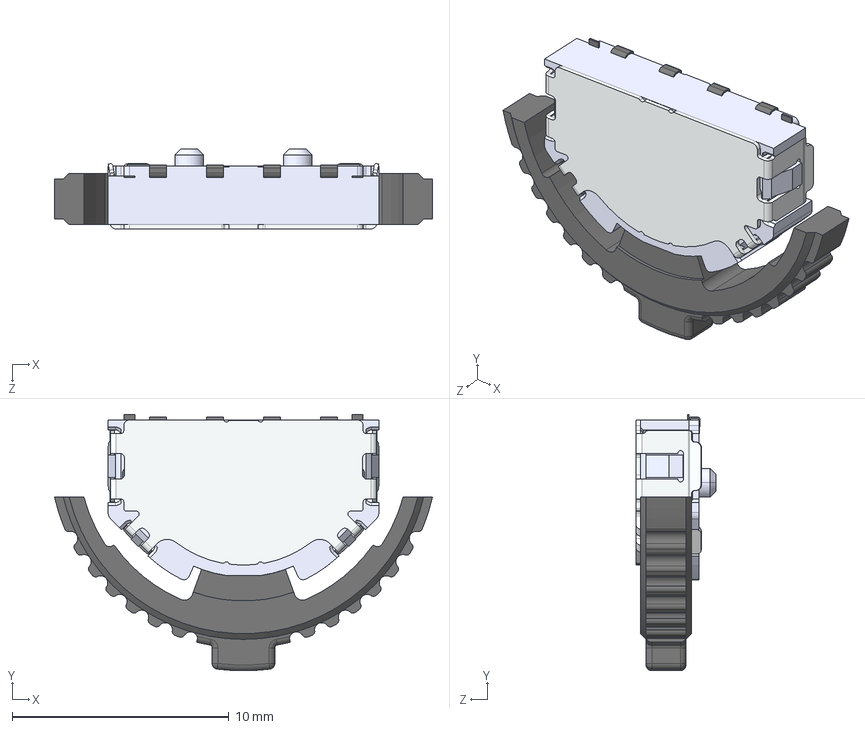
[picture p147: CAD file, 2025-09-22]
ASSETS/3D/Alps Alpine SLLB/SLLB510100_SCALED.STEP
17.5 x 11.8 x 3.68 mm
