dpmj/Bachelor_Thesis_TIK_Handheld_Device/ASSETS/3D/BATTERY/LIPO_805660.STEP

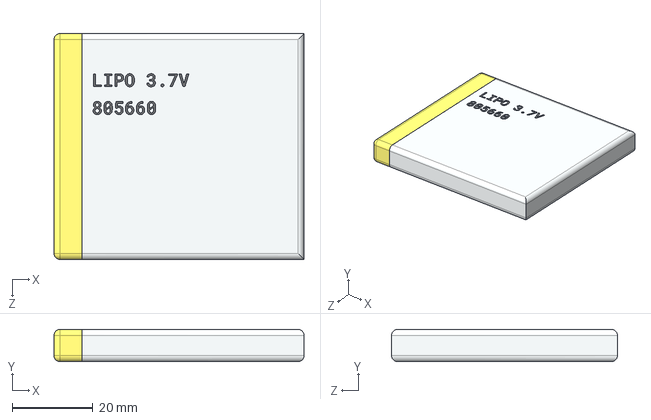
[picture p148: CAD file, 2025-09-22]
ASSETS/3D/BATTERY/LIPO_805660.STEP
62.0 x 8.01 x 56.0 mm
