dpmj/Bachelor_Thesis_TIK_Handheld_Device/ASSETS/3D/MALE HEADER PIN ARRAY/6PIN.SLDPRT

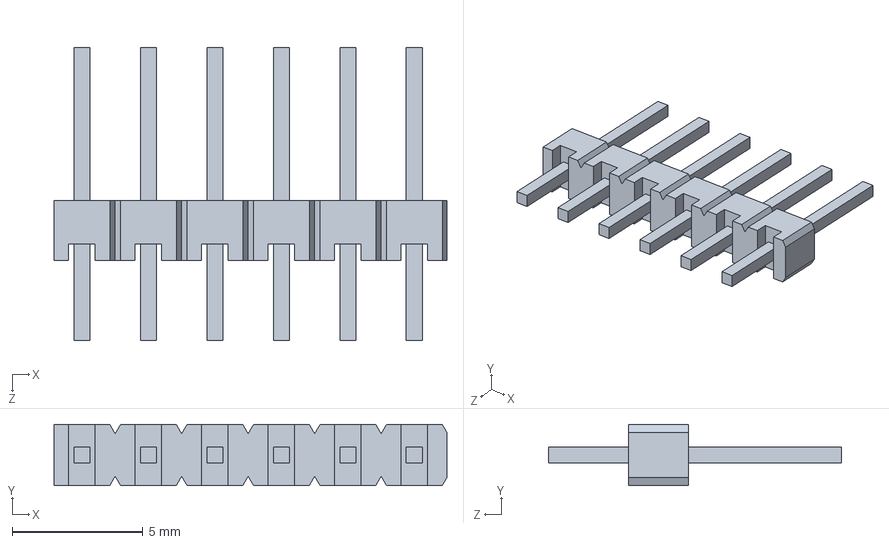
[picture p150: CAD file, 2025-09-22]
ASSETS/3D/MALE HEADER PIN ARRAY/6PIN.SLDPRT
15.0 x 2.34 x 11.2 mm
