dpmj/Bachelor_Thesis_TIK_Handheld_Device/ASSETS/3D/Rotary encoder right angle generic/Rotary Encoder with Switch, Model EN11-VSB (TT Electronics).stp

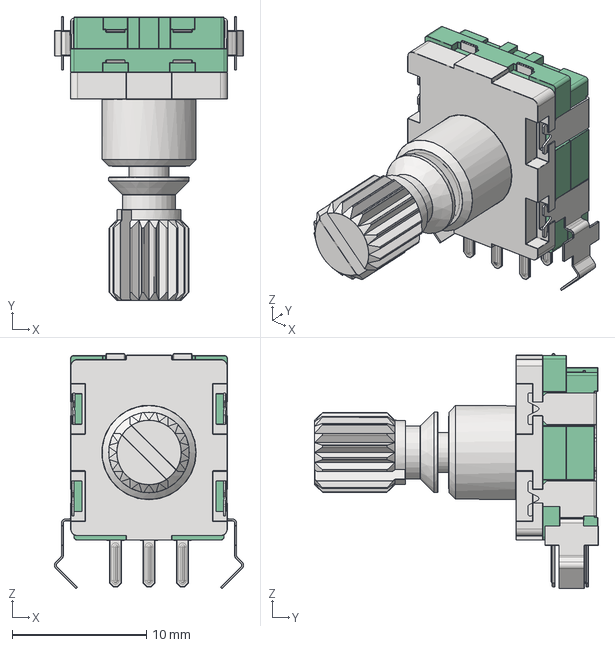
[picture p151: CAD file, 2025-09-22]
ASSETS/3D/Rotary encoder right angle generic/Rotary Encoder with Switch, Model EN11-VSB (TT Electronics).stp
14.1 x 21.1 x 17.5 mm
