dpmj/Bachelor_Thesis_TIK_Handheld_Device/ASSETS/3D/SPACER/Standoff mf - M4 x 10 across flats 7mm.step

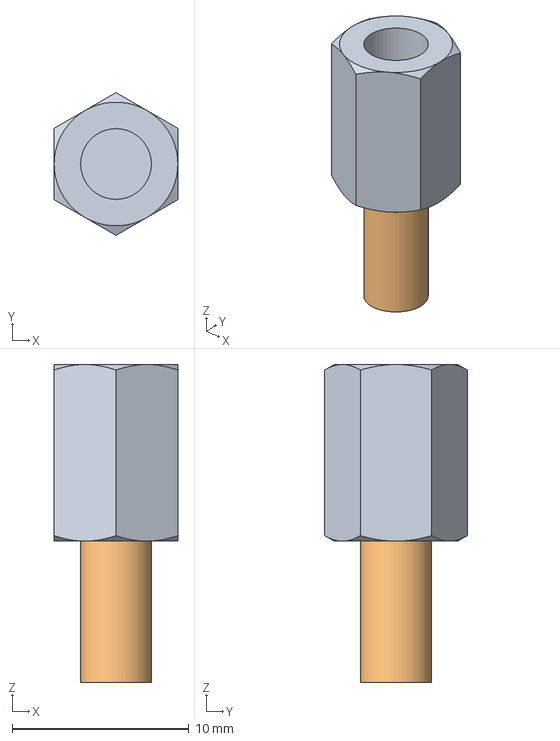
[picture p152: CAD file, 2025-09-22]
ASSETS/3D/SPACER/Standoff mf - M4 x 10 across flats 7mm.step
7.00 x 8.08 x 18.0 mm
