dpmj/Bachelor_Thesis_TIK_Handheld_Device/ASSETS/3D/THREADED INSERT/F2-H-B-M3-Pressfit.STEP

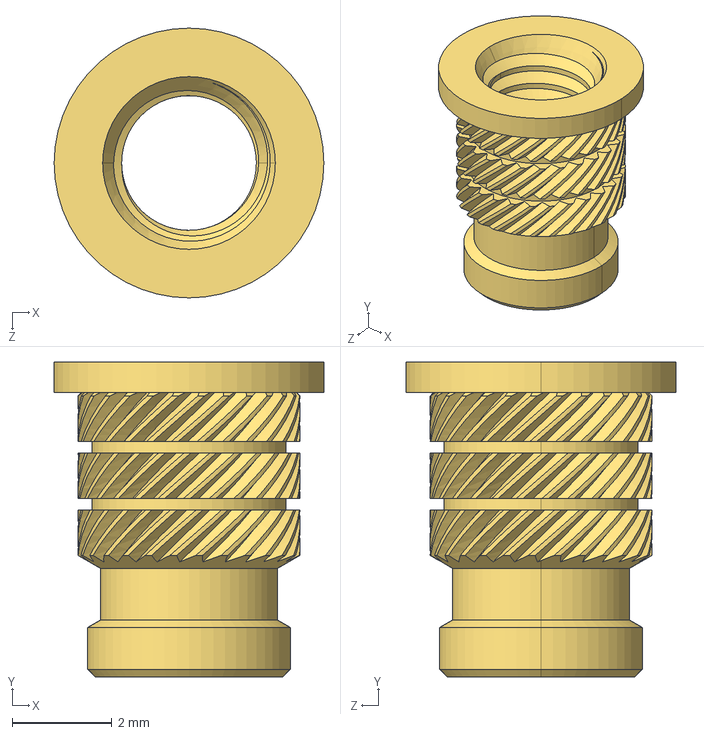
[picture p153: CAD file, 2025-09-22]
ASSETS/3D/THREADED INSERT/F2-H-B-M3-Pressfit.STEP
5.40 x 6.30 x 5.40 mm
