dpmj/Bachelor_Thesis_TIK_Handheld_Device/ASSETS/TIK_CASE/CASE_PARTS/BUTTON.SLDPRT

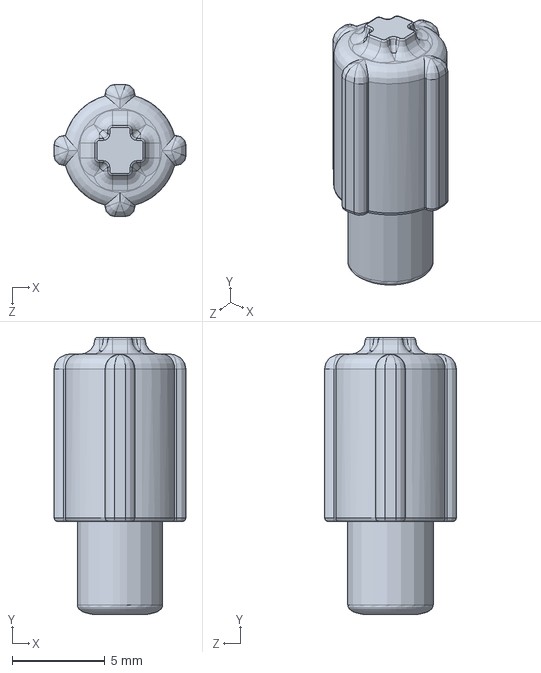
[picture p154: CAD file, 2025-09-22]
ASSETS/TIK_CASE/CASE_PARTS/BUTTON.SLDPRT
7.10 x 14.9 x 7.10 mm
