dpmj/Bachelor_Thesis_TIK_Handheld_Device/ASSETS/TIK_CASE/FUTURE/STYLUS.SLDPRT

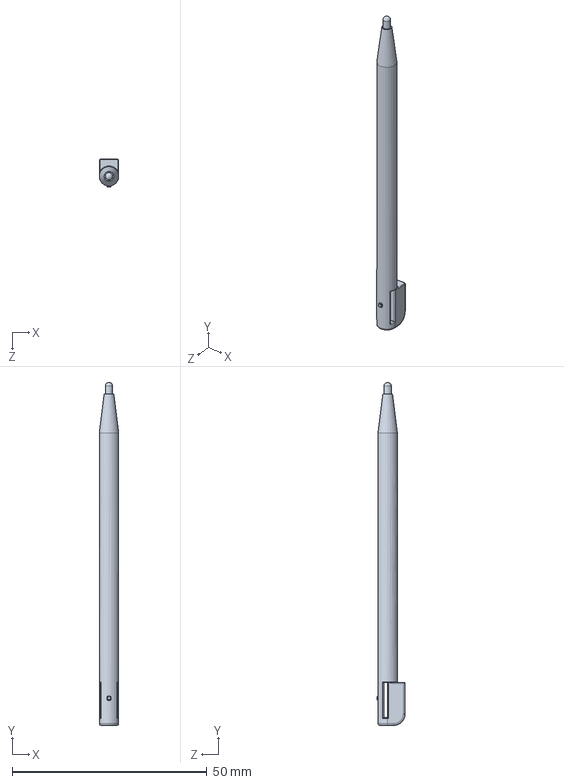
[picture p156: CAD file, 2025-09-22]
ASSETS/TIK_CASE/FUTURE/STYLUS.SLDPRT
5.00 x 88.0 x 7.30 mm
