dpmj/Bachelor_Thesis_TIK_Handheld_Device/ASSETS/TIK_CASE/PCB/PARTS/LIPO_604060.SLDPRT

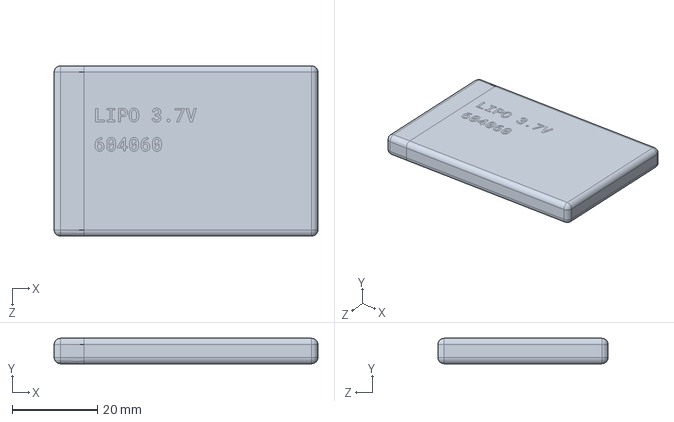
[picture p157: CAD file, 2025-09-22]
ASSETS/TIK_CASE/PCB/PARTS/LIPO_604060.SLDPRT
62.0 x 6.01 x 40.0 mm
