dpmj/Bachelor_Thesis_TIK_Handheld_Device/ASSETS/3D/BATTERY/LIPO_803035.STEP

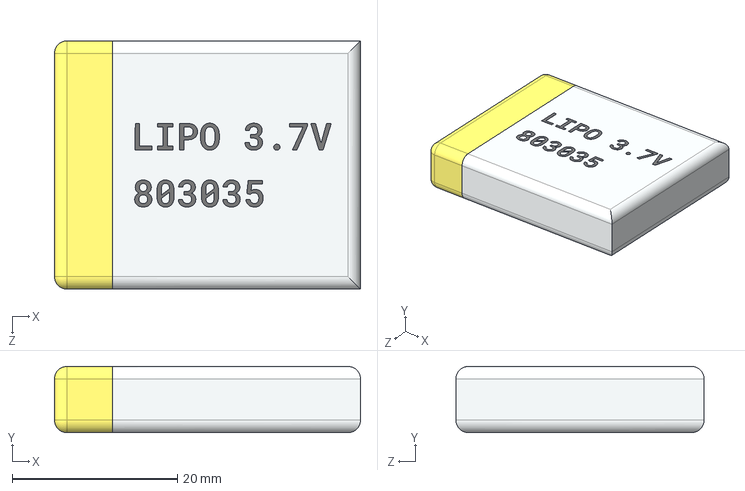
[picture p158: CAD file, 2025-09-22]
ASSETS/3D/BATTERY/LIPO_803035.STEP
37.0 x 8.01 x 30.0 mm
