dpmj/Bachelor_Thesis_TIK_Handheld_Device/ASSETS/3D/FEMALE HEADER PIN ARRAY/ROW HEADER low 5mm 1X4PIN.STEP

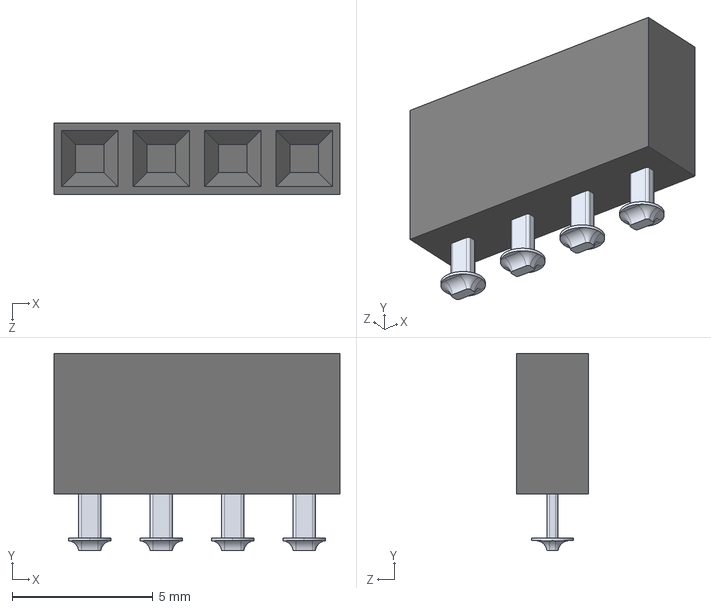
[picture p159: CAD file, 2025-09-22]
ASSETS/3D/FEMALE HEADER PIN ARRAY/ROW HEADER low 5mm 1X4PIN.STEP
10.2 x 7.00 x 2.54 mm
