dpmj/Bachelor_Thesis_TIK_Handheld_Device/ASSETS/3D/MALE HEADER PIN ARRAY/8PIN.SLDPRT

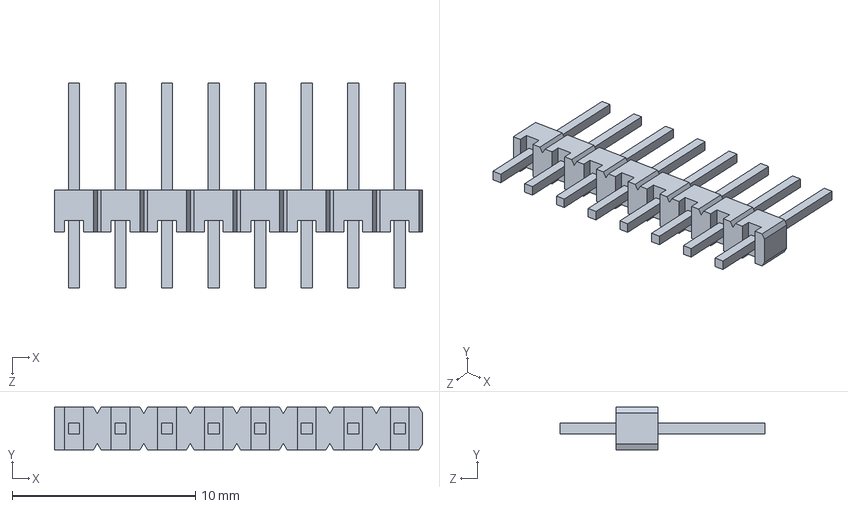
[picture p160: CAD file, 2025-09-22]
ASSETS/3D/MALE HEADER PIN ARRAY/8PIN.SLDPRT
20.1 x 2.34 x 11.2 mm
