dpmj/Bachelor_Thesis_TIK_Handheld_Device/ASSETS/3D/THREADED INSERT/F2-B-M3-Pressfit.STEP

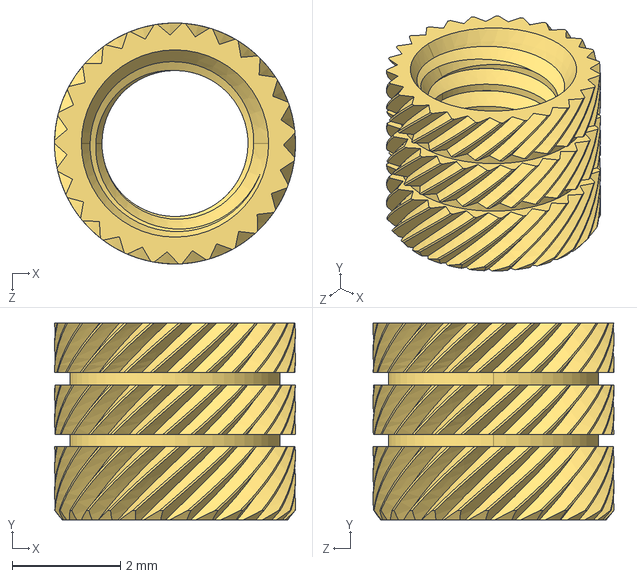
[picture p162: CAD file, 2025-09-22]
ASSETS/3D/THREADED INSERT/F2-B-M3-Pressfit.STEP
4.45 x 3.63 x 4.45 mm
