dpmj/Bachelor_Thesis_TIK_Handheld_Device/ASSETS/TIK_CASE/EXPORT/GCODE/CE3PRO_buttons3.3mf

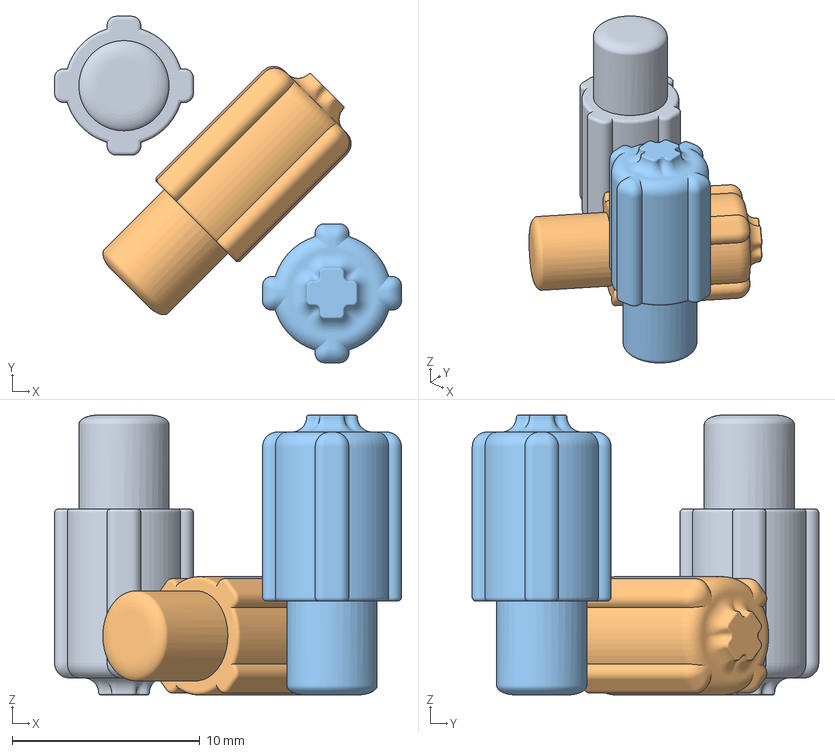
[picture p163: CAD file, 2025-09-22]
ASSETS/TIK_CASE/EXPORT/GCODE/CE3PRO_buttons3.3mf
18.5 x 18.5 x 14.9 mm
BUTTON.STL
BUTTON.STL(1)
BUTTON.STL(2)
