dpmj/Bachelor_Thesis_TIK_Handheld_Device/ASSETS/TIK_CASE/FUTURE/SCREEN.SLDPRT

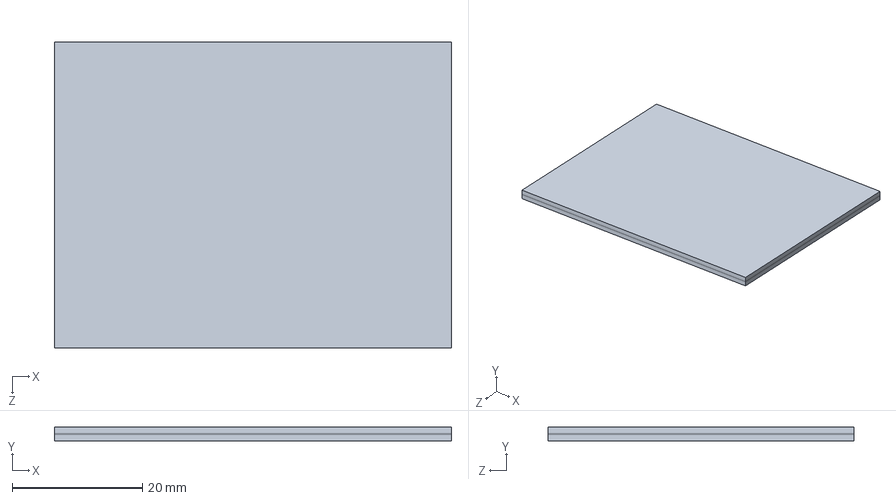
[picture p164: CAD file, 2025-09-22]
ASSETS/TIK_CASE/FUTURE/SCREEN.SLDPRT
61.0 x 2.10 x 47.0 mm
