dpmj/Bachelor_Thesis_TIK_Handheld_Device/ASSETS/3D/FEMALE HEADER PIN ARRAY/ROW HEADER Parametric_5mm.SLDPRT

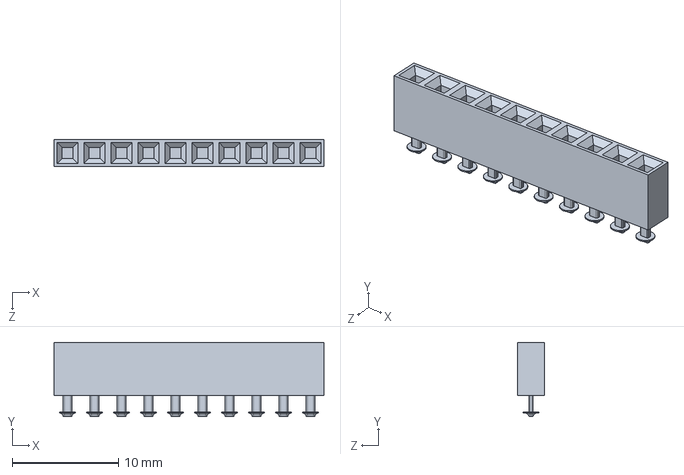
[picture p165: CAD file, 2025-09-22]
ASSETS/3D/FEMALE HEADER PIN ARRAY/ROW HEADER Parametric_5mm.SLDPRT
25.4 x 7.00 x 2.54 mm
