dpmj/Bachelor_Thesis_TIK_Handheld_Device/ASSETS/TIK_CASE/CASE_PARTS/BUTTON_FIX.SLDPRT

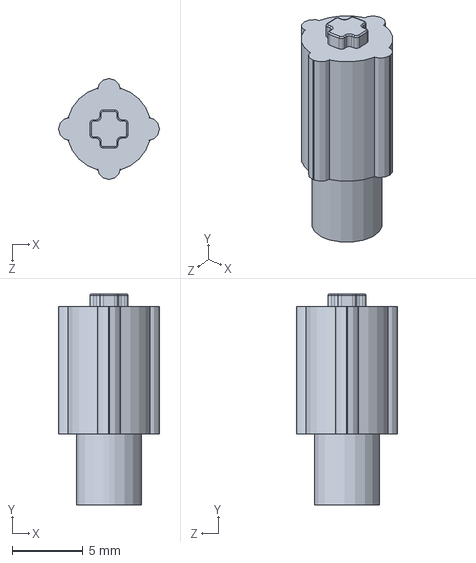
[picture p167: CAD file, 2025-09-22]
ASSETS/TIK_CASE/CASE_PARTS/BUTTON_FIX.SLDPRT
7.10 x 14.9 x 7.10 mm
