dpmj/Bachelor_Thesis_TIK_Handheld_Device/ASSETS/TIK_CASE/EXPORT/GCODE/buttons.3mf

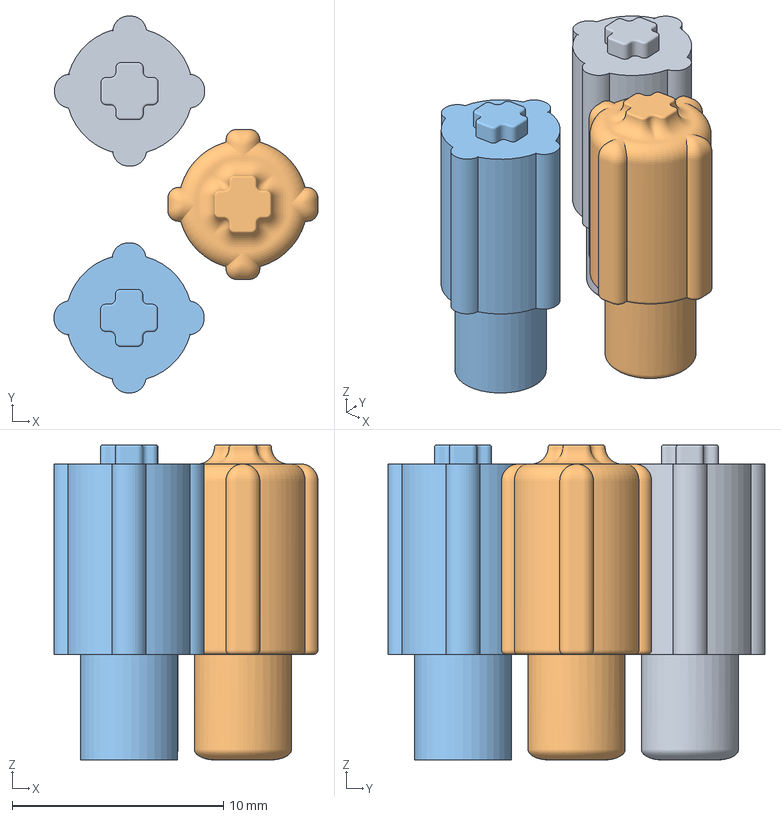
[picture p168: CAD file, 2025-09-22]
ASSETS/TIK_CASE/EXPORT/GCODE/buttons.3mf
12.5 x 17.8 x 14.9 mm
BUTTON_FIX2.STL
BUTTON_FIX.STL
BUTTON_FIX3.STL
