dpmj/Bachelor_Thesis_TIK_Handheld_Device/ASSETS/TIK_CASE/FUTURE/micro.SLDPRT

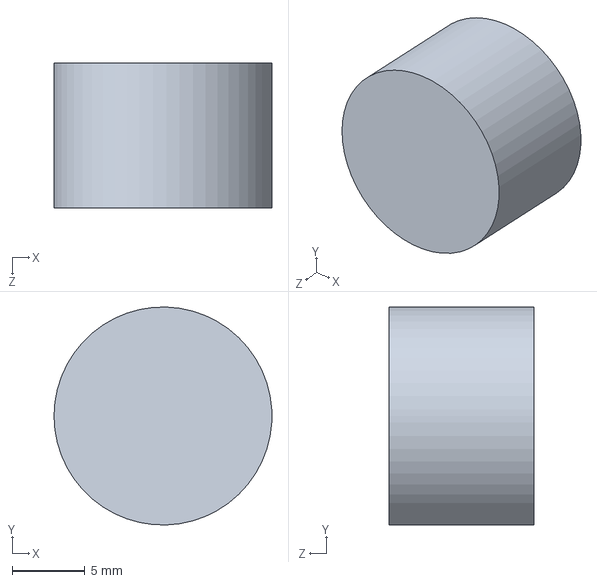
[picture p169: CAD file, 2025-09-22]
ASSETS/TIK_CASE/FUTURE/micro.SLDPRT
15.0 x 15.0 x 10.0 mm
