dpmj/Bachelor_Thesis_TIK_Handheld_Device/ASSETS/TIK_CASE/PROTO/CASE_PROTO.SLDPRT

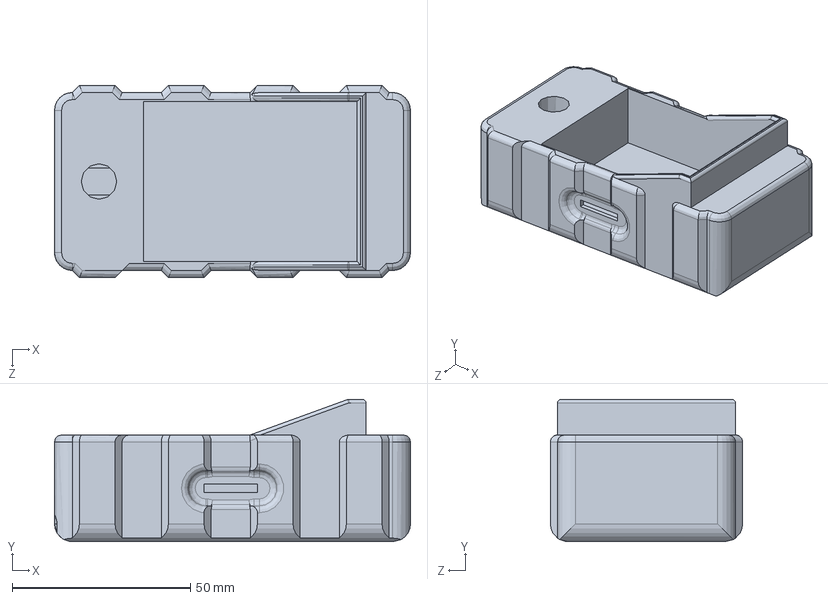
[picture p170: CAD file, 2025-09-22]
ASSETS/TIK_CASE/PROTO/CASE_PROTO.SLDPRT
100.0 x 40.0 x 54.0 mm
