dpmj/Bachelor_Thesis_TIK_Handheld_Device/ASSETS/TIK_CASE/EXPORT/GCODE/CE3PRO_TOP_COVER_AVELLANADA.3mf

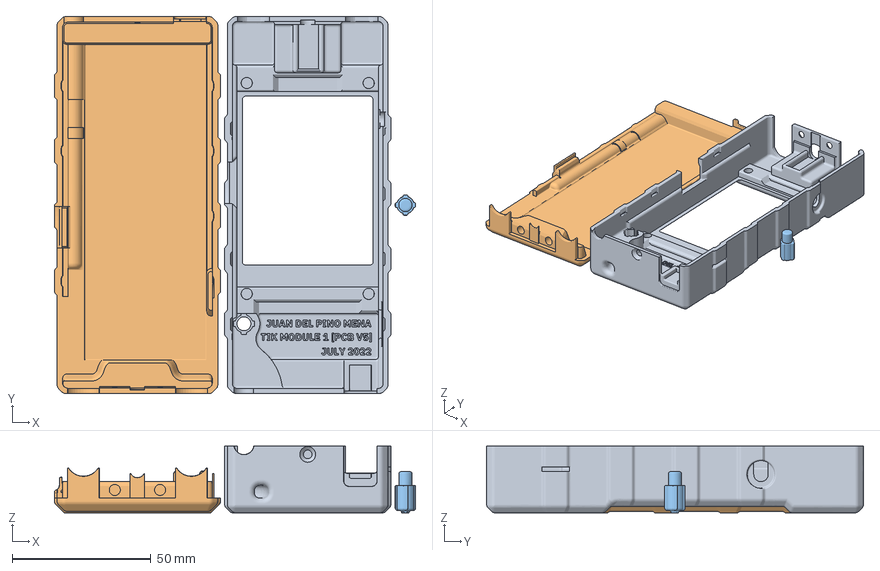
[picture p173: CAD file, 2025-09-22]
ASSETS/TIK_CASE/EXPORT/GCODE/CE3PRO_TOP_COVER_AVELLANADA.3mf
130.4 x 136.0 x 24.1 mm
TOP_COVER_AVELLANADA.STL
BOTTOM_COVER.STL
BUTTON.STL
