dpmj/Bachelor_Thesis_TIK_Handheld_Device/ASSETS/TIK_CASE/EXPORT/STL/BUTTON_FIX2.STL

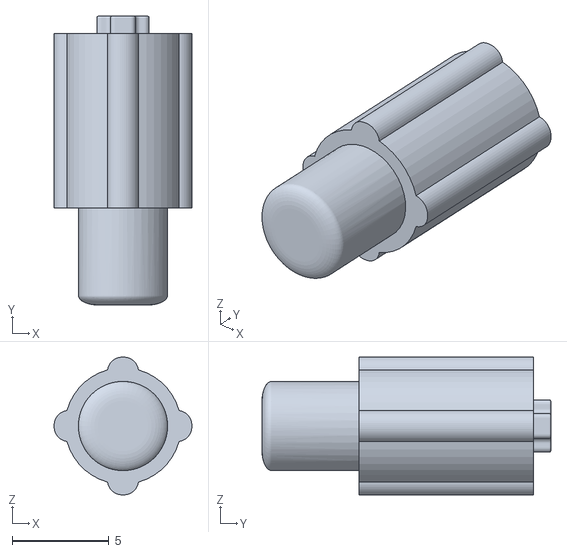
[picture p174: CAD file, 2025-09-22]
ASSETS/TIK_CASE/EXPORT/STL/BUTTON_FIX2.STL
7.10 x 14.9 x 7.10
