dpmj/Bachelor_Thesis_TIK_Handheld_Device/ASSETS/TIK_CASE/FUTURE/embolo.SLDPRT

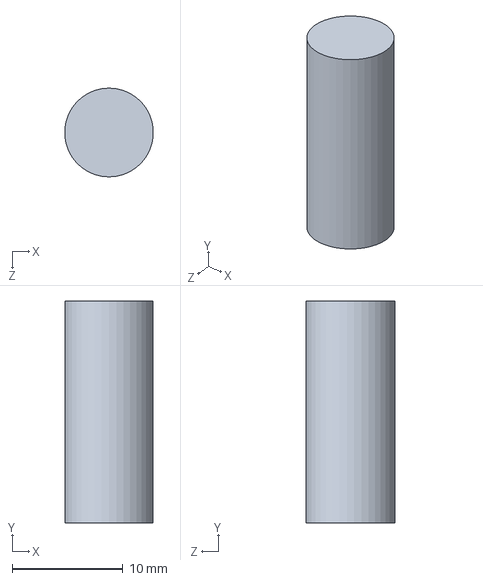
[picture p175: CAD file, 2025-09-22]
ASSETS/TIK_CASE/FUTURE/embolo.SLDPRT
7.97 x 20.0 x 8.00 mm
