dpmj/Bachelor_Thesis_TIK_Handheld_Device/ASSETS/TIK_CASE/PROTO/boton.SLDPRT

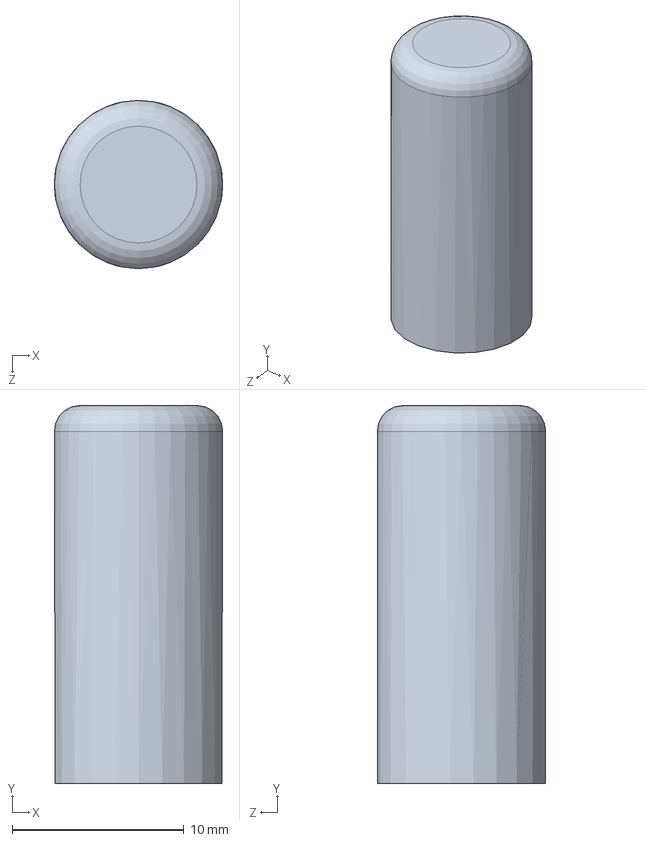
[picture p176: CAD file, 2025-09-22]
ASSETS/TIK_CASE/PROTO/boton.SLDPRT
9.80 x 22.0 x 9.80 mm
