dpmj/Bachelor_Thesis_TIK_Handheld_Device/ASSETS/3D/BATTERY/1100mAh lipo v8.step

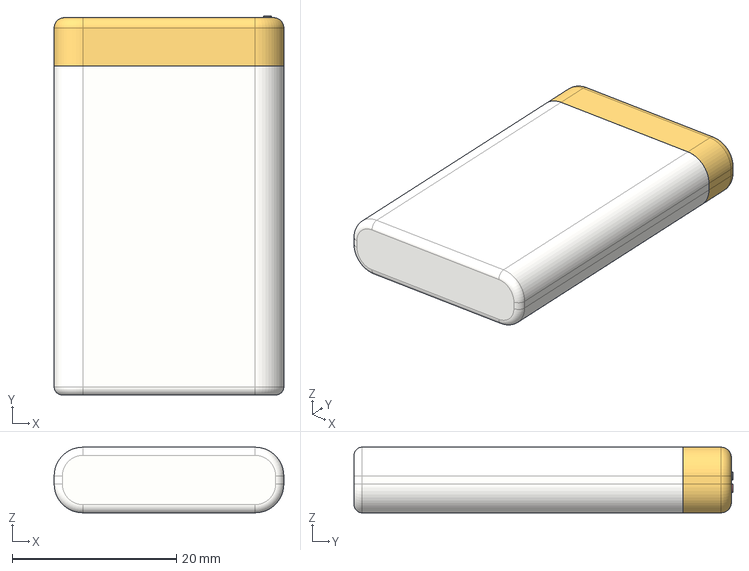
[picture p177: CAD file, 2025-09-22]
ASSETS/3D/BATTERY/1100mAh lipo v8.step
28.0 x 46.2 x 8.00 mm
