dpmj/Bachelor_Thesis_TIK_Handheld_Device/ASSETS/3D/FEMALE HEADER PIN ARRAY/FEMALE_THT_11X2_Names.STEP

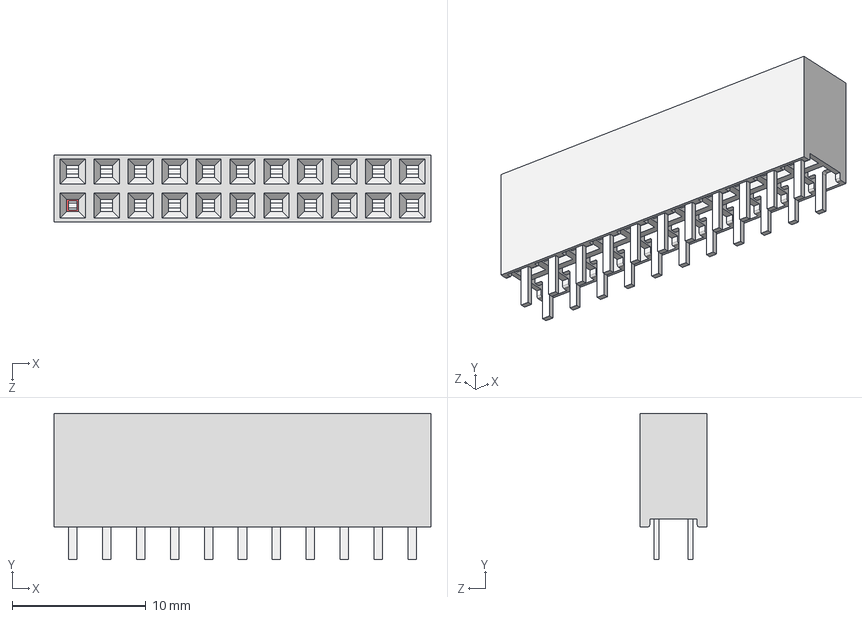
[picture p178: CAD file, 2025-09-22]
ASSETS/3D/FEMALE HEADER PIN ARRAY/FEMALE_THT_11X2_Names.STEP
28.2 x 10.9 x 5.00 mm
