dpmj/Bachelor_Thesis_TIK_Handheld_Device/ASSETS/TIK_CASE/CASE_PARTS/BOTTOM_COVER.SLDPRT

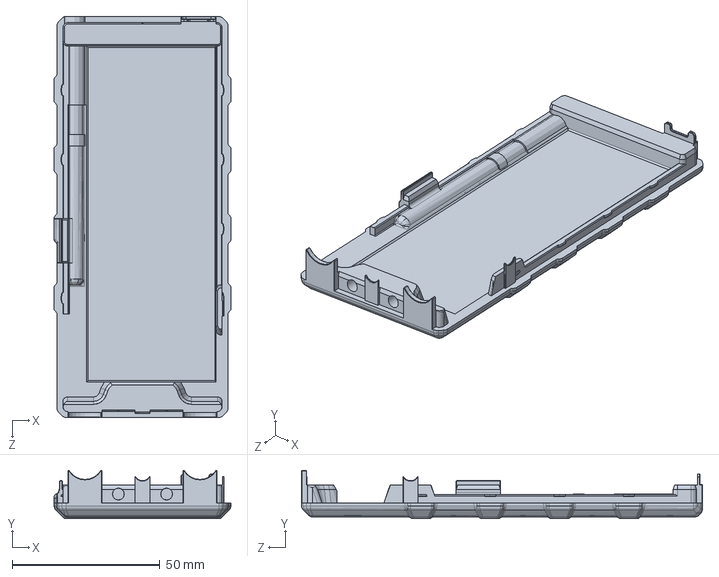
[picture p180: CAD file, 2025-09-22]
ASSETS/TIK_CASE/CASE_PARTS/BOTTOM_COVER.SLDPRT
60.0 x 16.3 x 136.0 mm
