dpmj/Bachelor_Thesis_TIK_Handheld_Device/ASSETS/3D/BATTERY/Li Bat 503035P.step

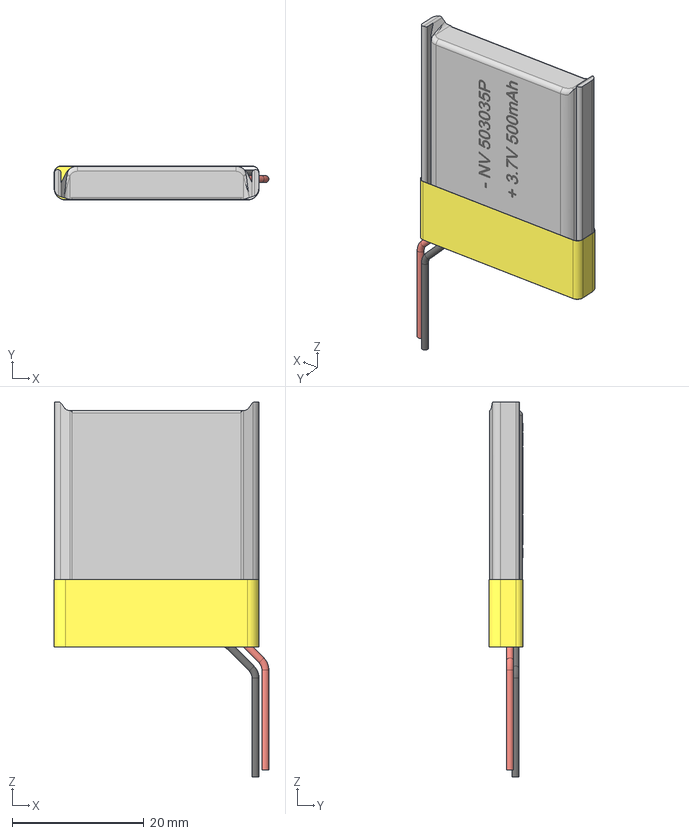
[picture p181: CAD file, 2025-09-22]
ASSETS/3D/BATTERY/Li Bat 503035P.step
32.6 x 5.17 x 56.9 mm
Kapton Tape
Battery Cell
Board Part 1
PCB
Positive
Negative
Board Part 2
