dpmj/Bachelor_Thesis_TIK_Handheld_Device/ASSETS/TIK_CASE/FUTURE/BUTTON.SLDPRT

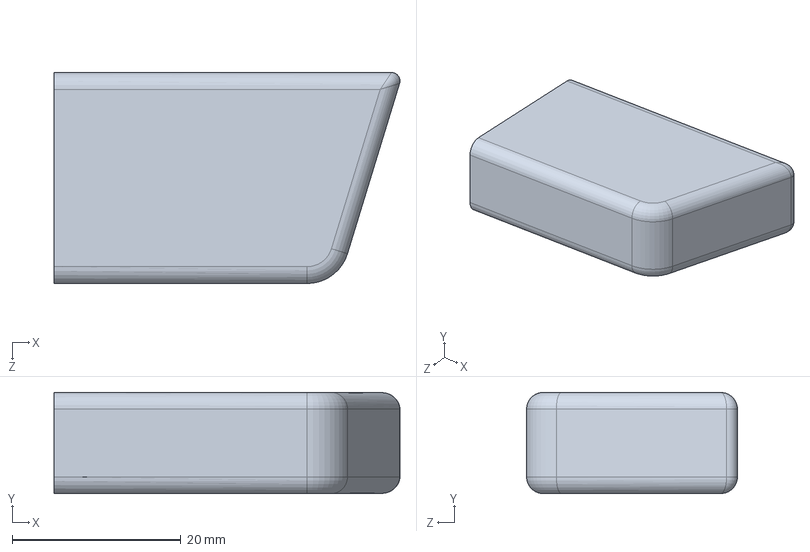
[picture p184: CAD file, 2025-09-22]
ASSETS/TIK_CASE/FUTURE/BUTTON.SLDPRT
41.0 x 12.0 x 25.0 mm
