dpmj/Bachelor_Thesis_TIK_Handheld_Device/ASSETS/TIK_CASE/PROTO/CUI_DEVICES_SJ-43516-SMT-TR.step

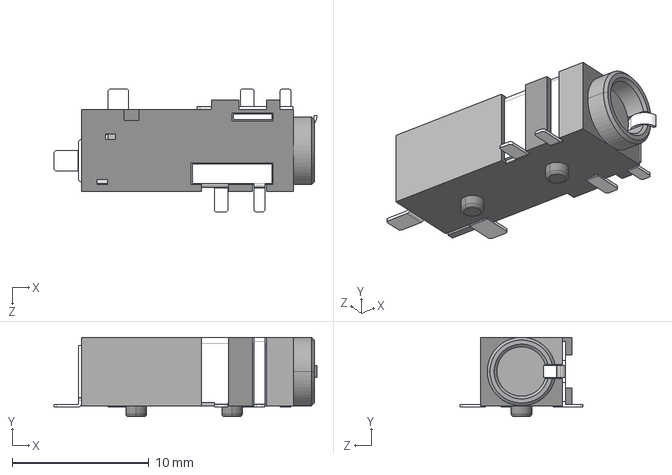
[picture p185: CAD file, 2025-09-22]
ASSETS/TIK_CASE/PROTO/CUI_DEVICES_SJ-43516-SMT-TR.step
19.2 x 5.80 x 9.00 mm
