dpmj/Bachelor_Thesis_TIK_Handheld_Device/ASSETS/3D/FEMALE HEADER PIN ARRAY/FEMALE_THT_9X2_names.stp

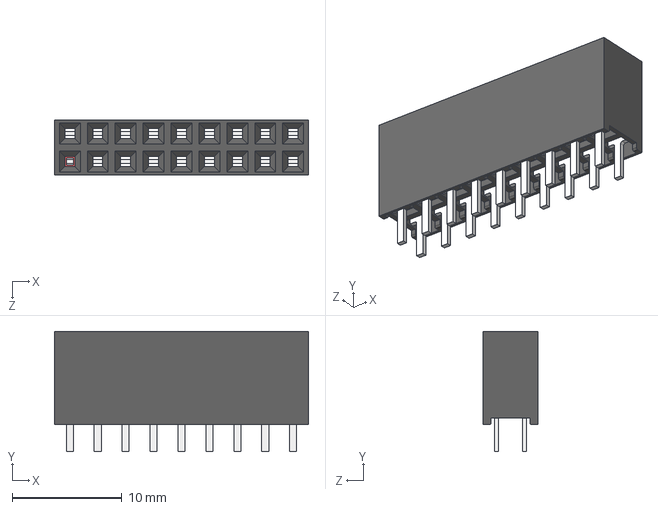
[picture p188: CAD file, 2025-09-22]
ASSETS/3D/FEMALE HEADER PIN ARRAY/FEMALE_THT_9X2_names.stp
23.1 x 10.9 x 5.00 mm
