dpmj/Bachelor_Thesis_TIK_Handheld_Device/ASSETS/3D/FEMALE HEADER PIN ARRAY/ROW HEADER 1X14PIN.STEP

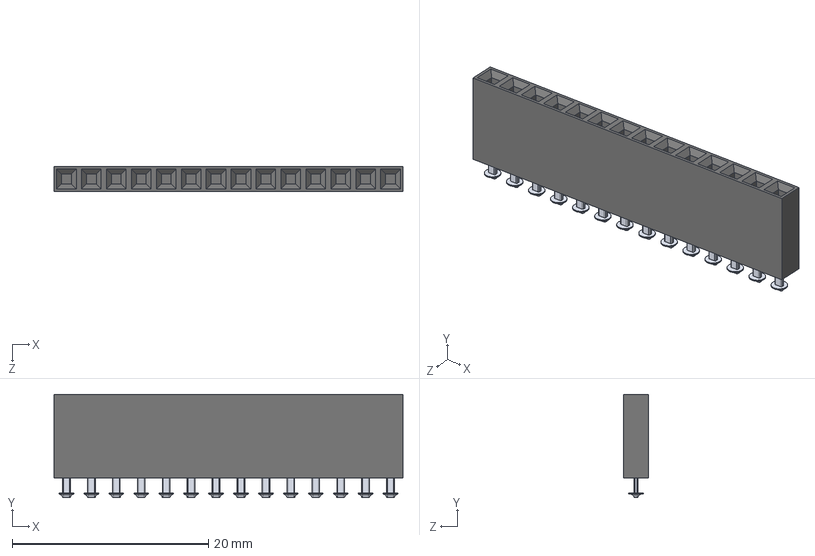
[picture p190: CAD file, 2025-09-22]
ASSETS/3D/FEMALE HEADER PIN ARRAY/ROW HEADER 1X14PIN.STEP
35.6 x 10.5 x 2.54 mm
