dpmj/Bachelor_Thesis_TIK_Handheld_Device/ASSETS/3D/FEMALE HEADER PIN ARRAY/ROW HEADER low 5mm 1X14PIN.STEP

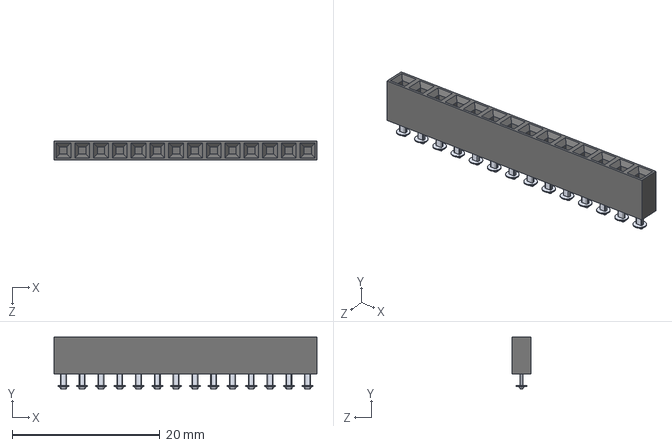
[picture p192: CAD file, 2025-09-22]
ASSETS/3D/FEMALE HEADER PIN ARRAY/ROW HEADER low 5mm 1X14PIN.STEP
35.6 x 7.00 x 2.54 mm
