dpmj/Bachelor_Thesis_TIK_Handheld_Device/ASSETS/3D/SPACER/Standoff mf - M4 x 75 across flats 7mm.step

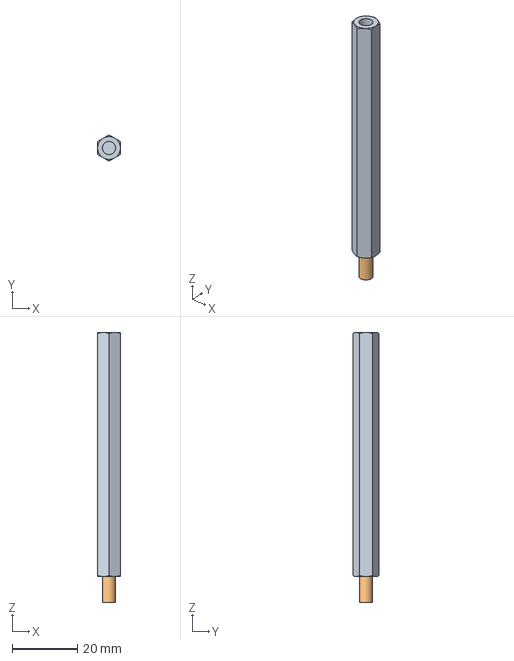
[picture p194: CAD file, 2025-09-22]
ASSETS/3D/SPACER/Standoff mf - M4 x 75 across flats 7mm.step
7.00 x 8.08 x 83.0 mm
