dpmj/Bachelor_Thesis_TIK_Handheld_Device/ASSETS/3D/SPACER/Standoff mf - M3 x 45 across flats 5.5mm.step

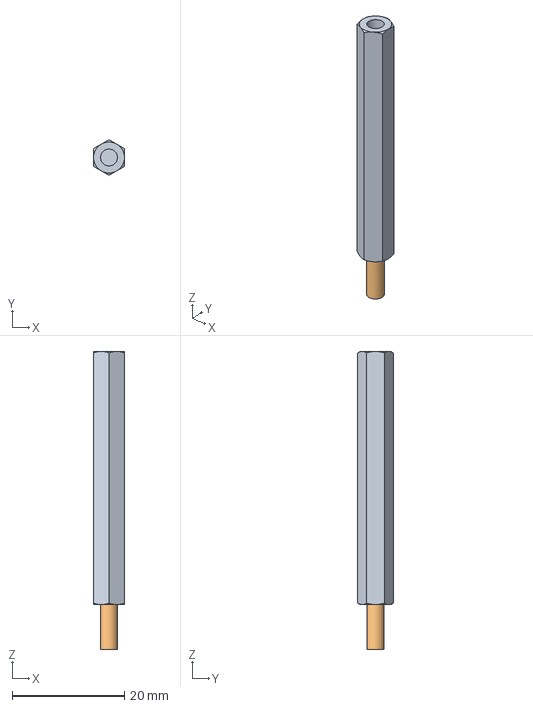
[picture p200: CAD file, 2025-09-22]
ASSETS/3D/SPACER/Standoff mf - M3 x 45 across flats 5.5mm.step
5.50 x 6.35 x 53.0 mm
