dpmj/Bachelor_Thesis_TIK_Handheld_Device/ASSETS/3D/SPACER/Standoff mf - M2.5 x 60 across flats 5mm.step

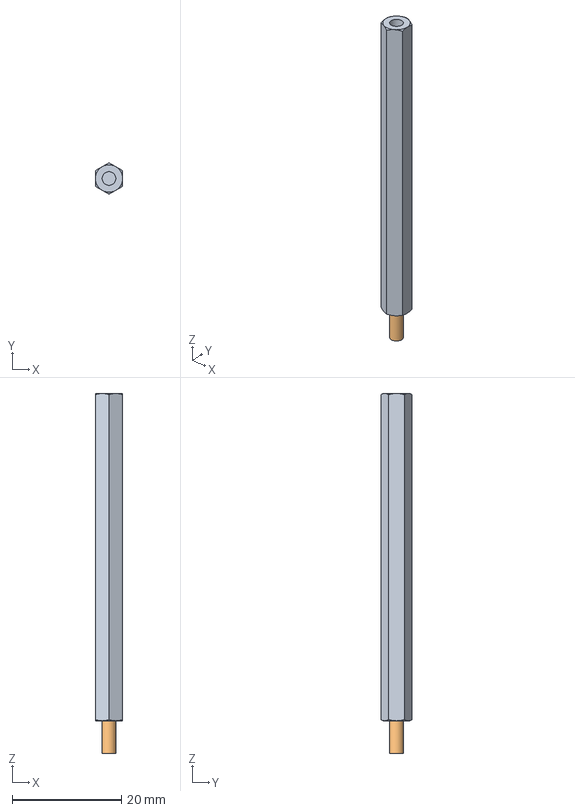
[picture p206: CAD file, 2025-09-22]
ASSETS/3D/SPACER/Standoff mf - M2.5 x 60 across flats 5mm.step
5.00 x 5.77 x 66.0 mm
