dpmj/Bachelor_Thesis_TIK_Handheld_Device/ASSETS/3D/SPACER/Standoff mf - M3 x 50 across flats 5mm.step

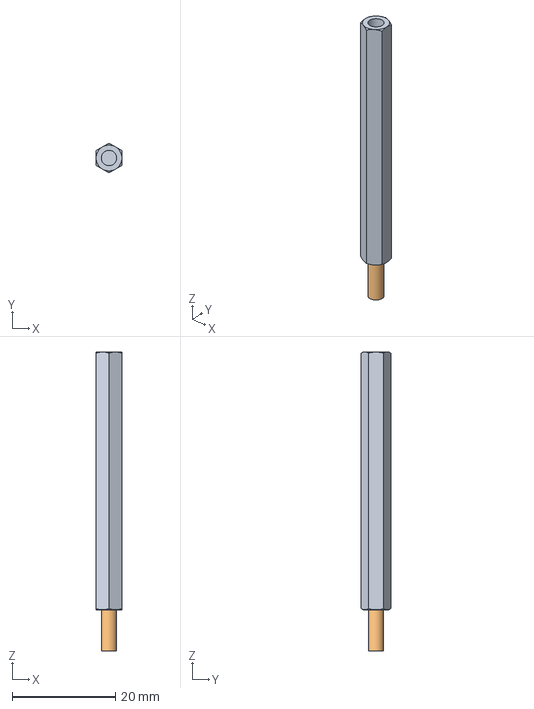
[picture p218: CAD file, 2025-09-22]
ASSETS/3D/SPACER/Standoff mf - M3 x 50 across flats 5mm.step
5.00 x 5.77 x 58.0 mm
