dpmj/Bachelor_Thesis_TIK_Handheld_Device/ASSETS/3D/SPACER/Standoff mf - M6 x 45 across flats 10mm.step

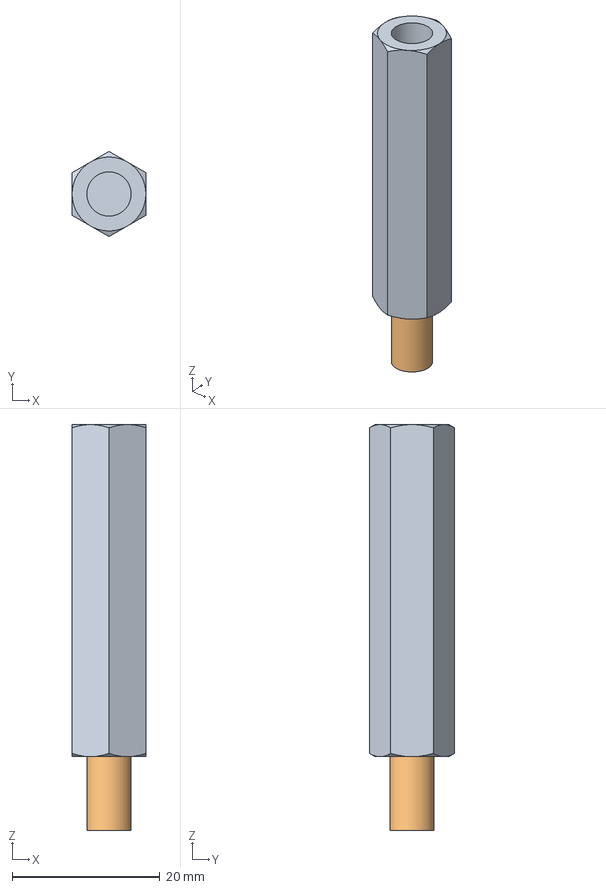
[picture p219: CAD file, 2025-09-22]
ASSETS/3D/SPACER/Standoff mf - M6 x 45 across flats 10mm.step
10.0 x 11.5 x 55.0 mm
