dpmj/Bachelor_Thesis_TIK_Handheld_Device/ASSETS/3D/SPACER/Standoff mf - M2.5 x 18 across flats 5mm.step

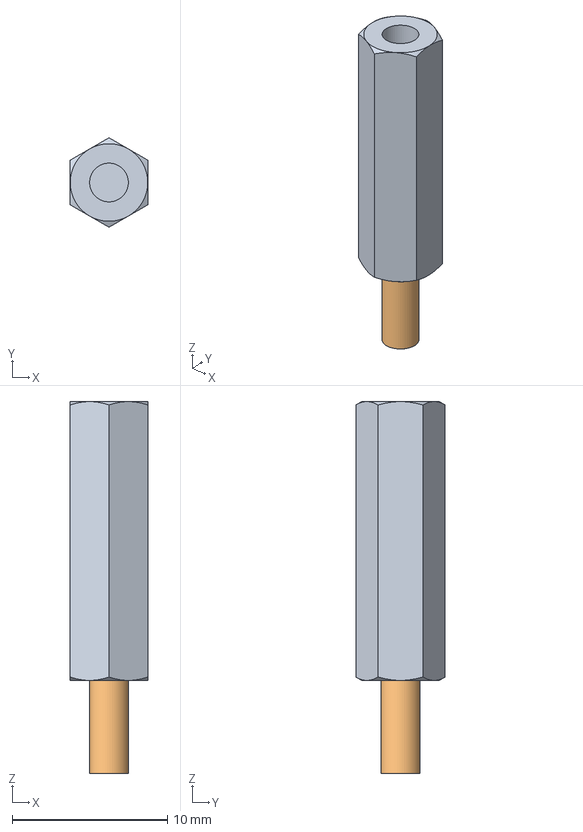
[picture p221: CAD file, 2025-09-22]
ASSETS/3D/SPACER/Standoff mf - M2.5 x 18 across flats 5mm.step
5.00 x 5.77 x 24.0 mm
