dpmj/Bachelor_Thesis_TIK_Handheld_Device/ASSETS/3D/SPACER/Standoff mf - M2.5 x 25 across flats 4mm.step

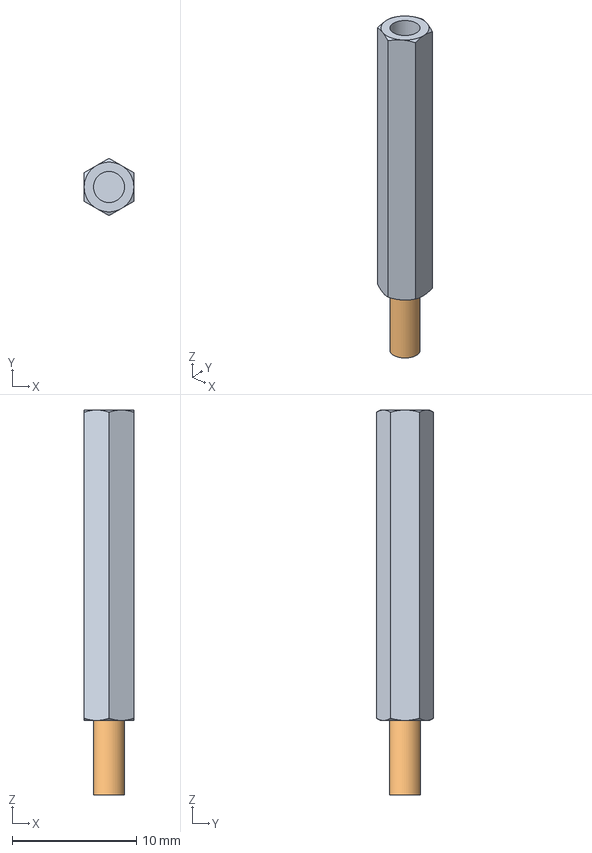
[picture p223: CAD file, 2025-09-22]
ASSETS/3D/SPACER/Standoff mf - M2.5 x 25 across flats 4mm.step
4.00 x 4.62 x 31.0 mm
