dpmj/Bachelor_Thesis_TIK_Handheld_Device/ASSETS/3D/SPACER/Standoff mf - M3 x 20 across flats 5mm.step

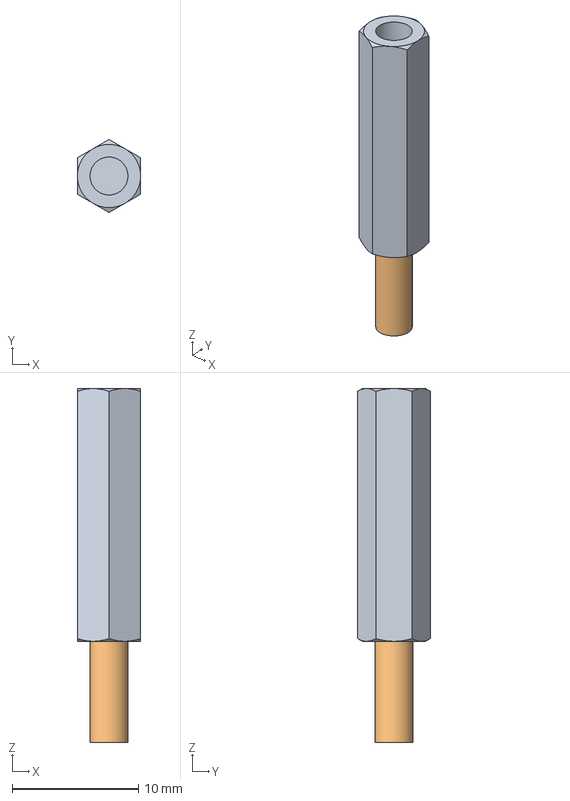
[picture p227: CAD file, 2025-09-22]
ASSETS/3D/SPACER/Standoff mf - M3 x 20 across flats 5mm.step
5.00 x 5.77 x 28.0 mm
