dpmj/Bachelor_Thesis_TIK_Handheld_Device/ASSETS/TIK_CASE/DRAWINGS/CASE_ASSEMBLED_W_PCB_color_collapsed.png

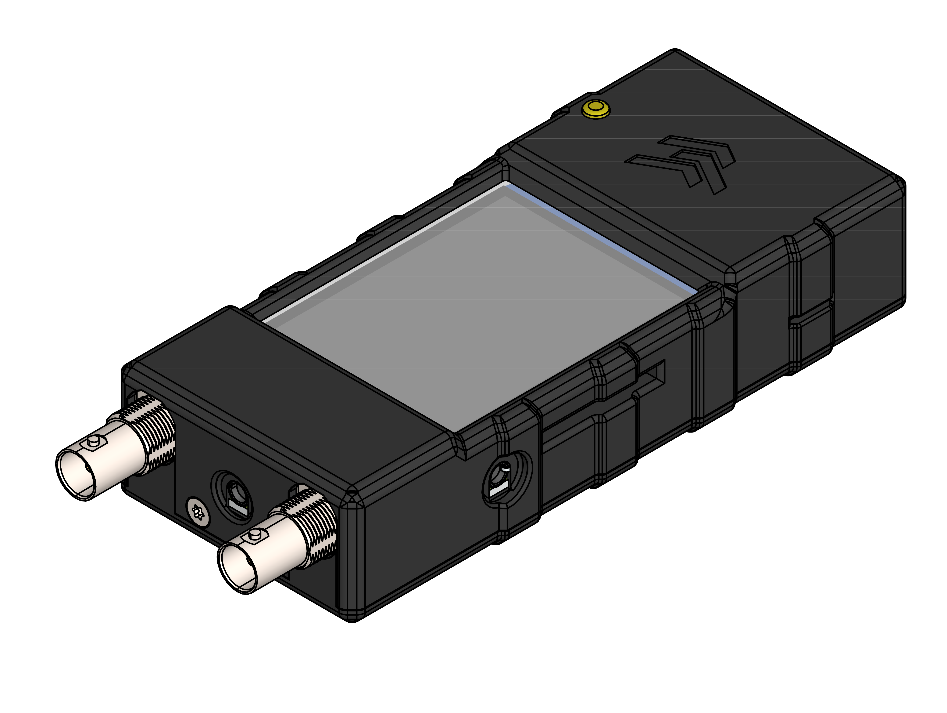
ASSETS/TIK_CASE/DRAWINGS/CASE_ASSEMBLED_W_PCB_color_collapsed.png
