dpmj/Bachelor_Thesis_TIK_Handheld_Device/ASSETS/IMAGES/PARTS/TFT LCD/measures.png

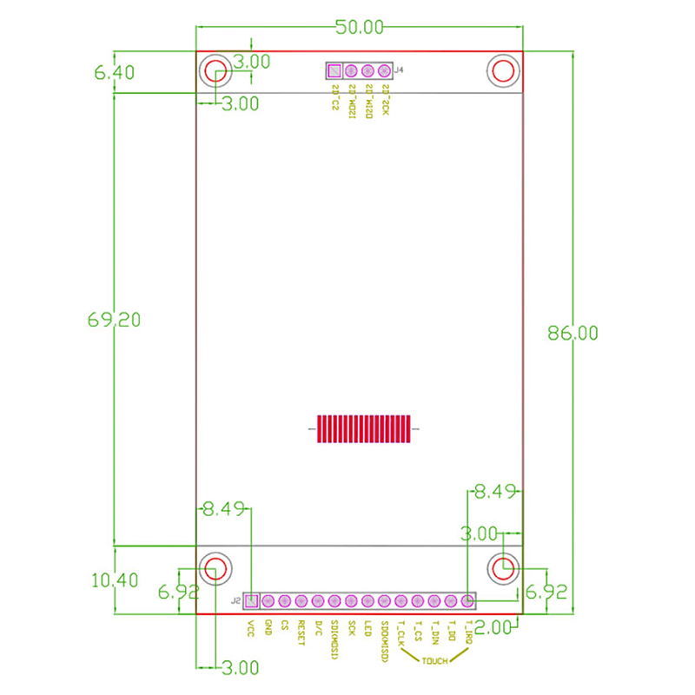
ASSETS/IMAGES/PARTS/TFT LCD/measures.png
