dpmj/Bachelor_Thesis_TIK_Handheld_Device/OUTPUT/PDF/DRAFTSMAN_ONLY.PDF

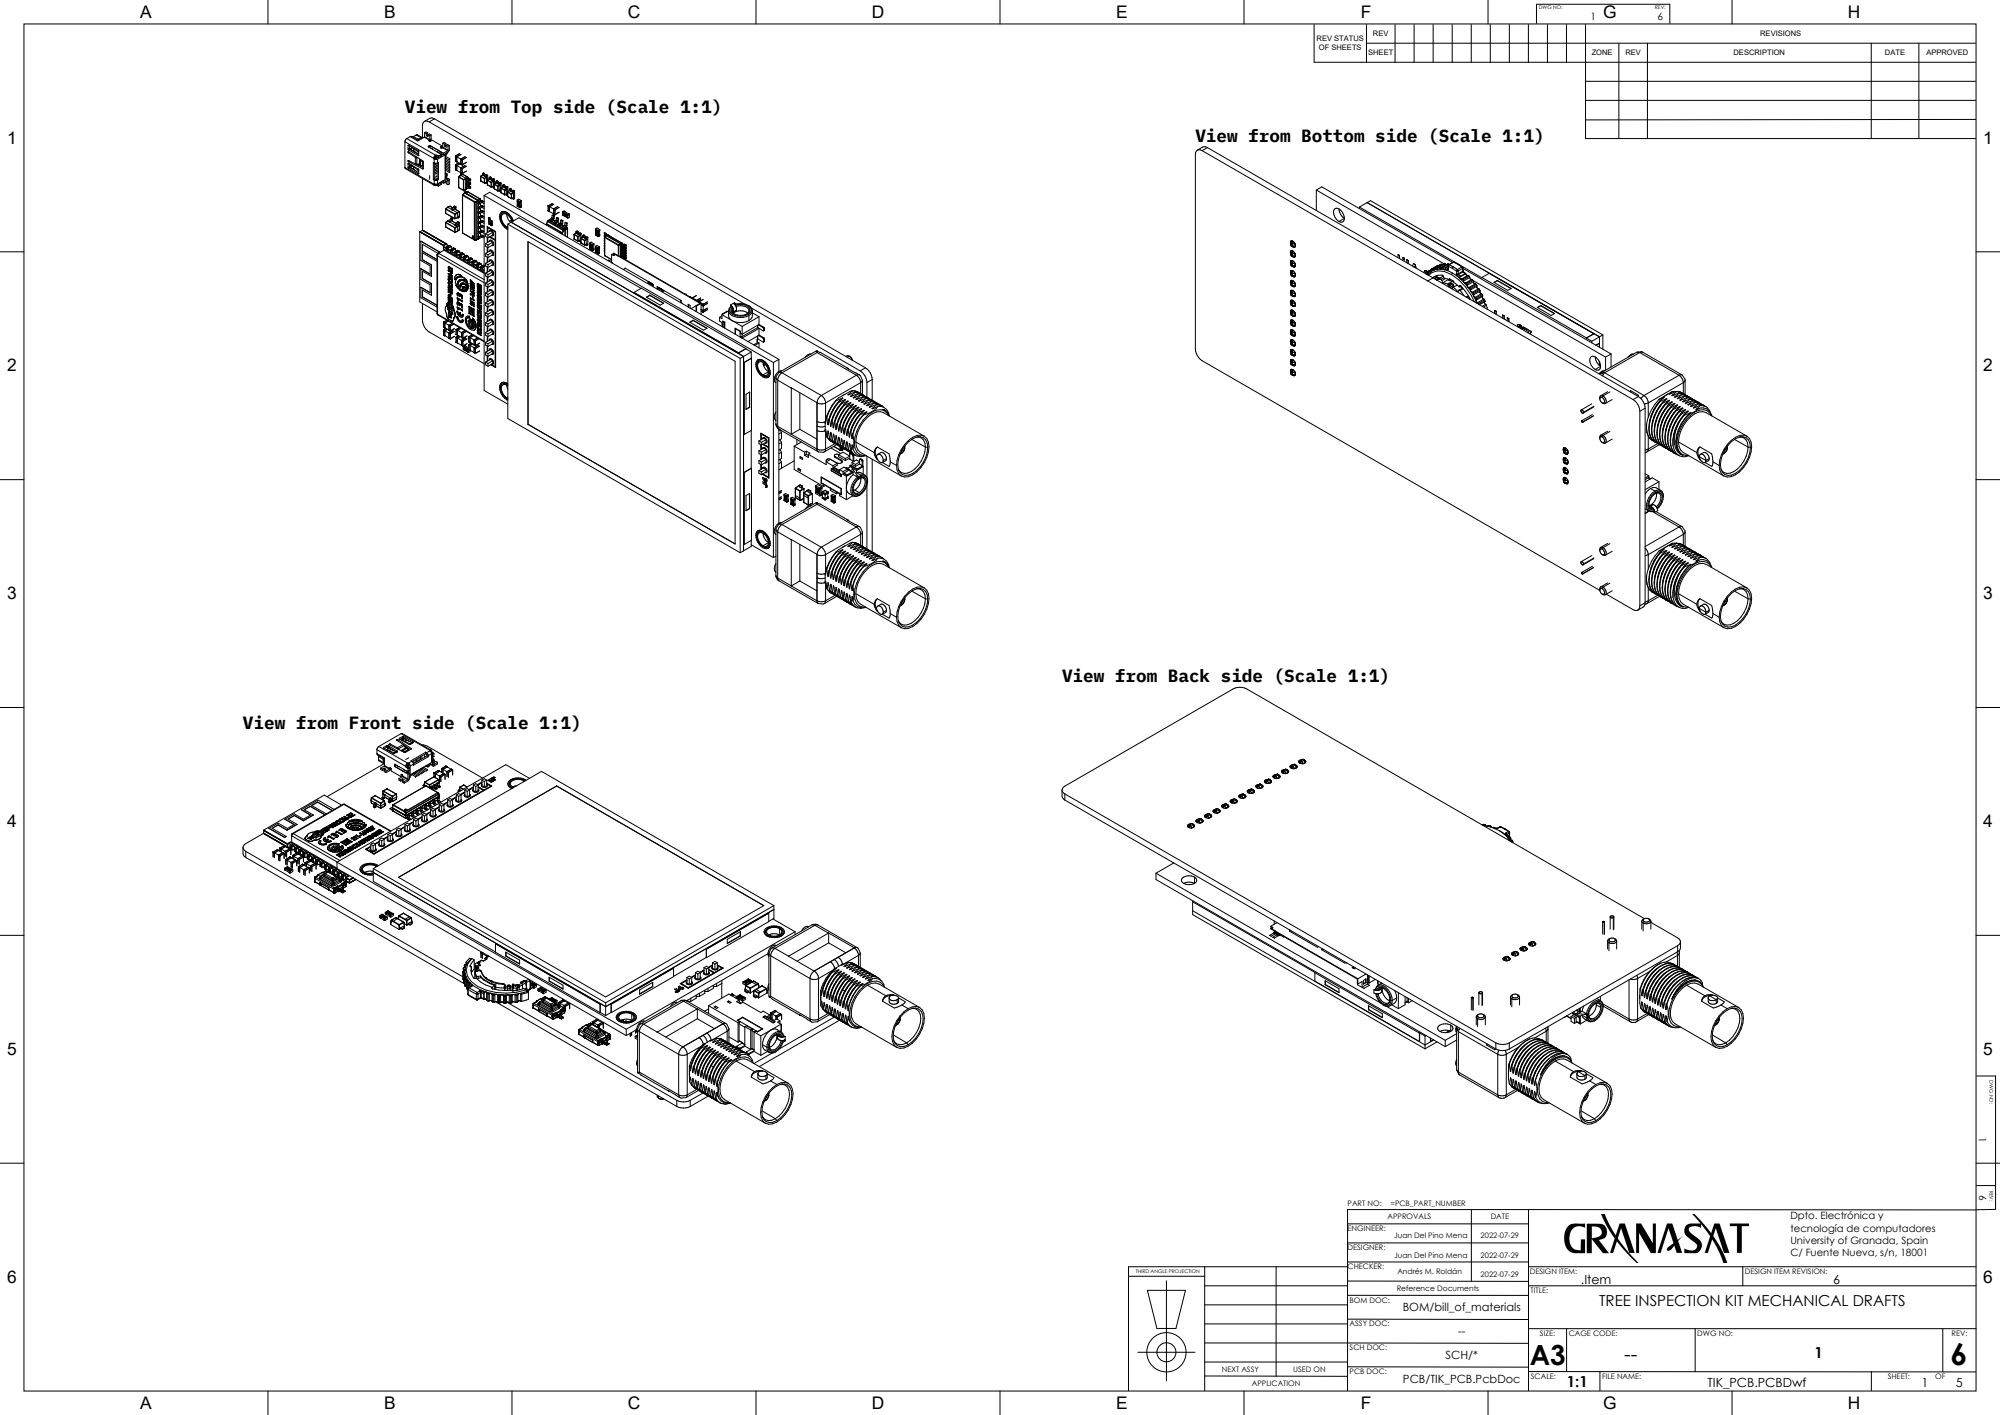
[picture p237: page 1]

View from Top side (Scale 1:1)

View from Bottom side (Scale 1:1)

View from Back side (Scale 1:1)

View from Front side (Scale 1:1)

APPROVALS | DATE

Dpto. Electrónica y
tecnología de computadores
University of Granada, Spain
C/ Fuente Nueva, s/n, 18001

ENGINEER: Juan Del Pino Mena | 2022-07-29

DESIGNER: Juan Del Pino Mena | 2022-07-29

THIRD ANGLE PROJECTION

CHECKER: Andrés M. Roldán | 2022-07-29

SCH DOC: SCH/*

NEXT ASSY | USED ON

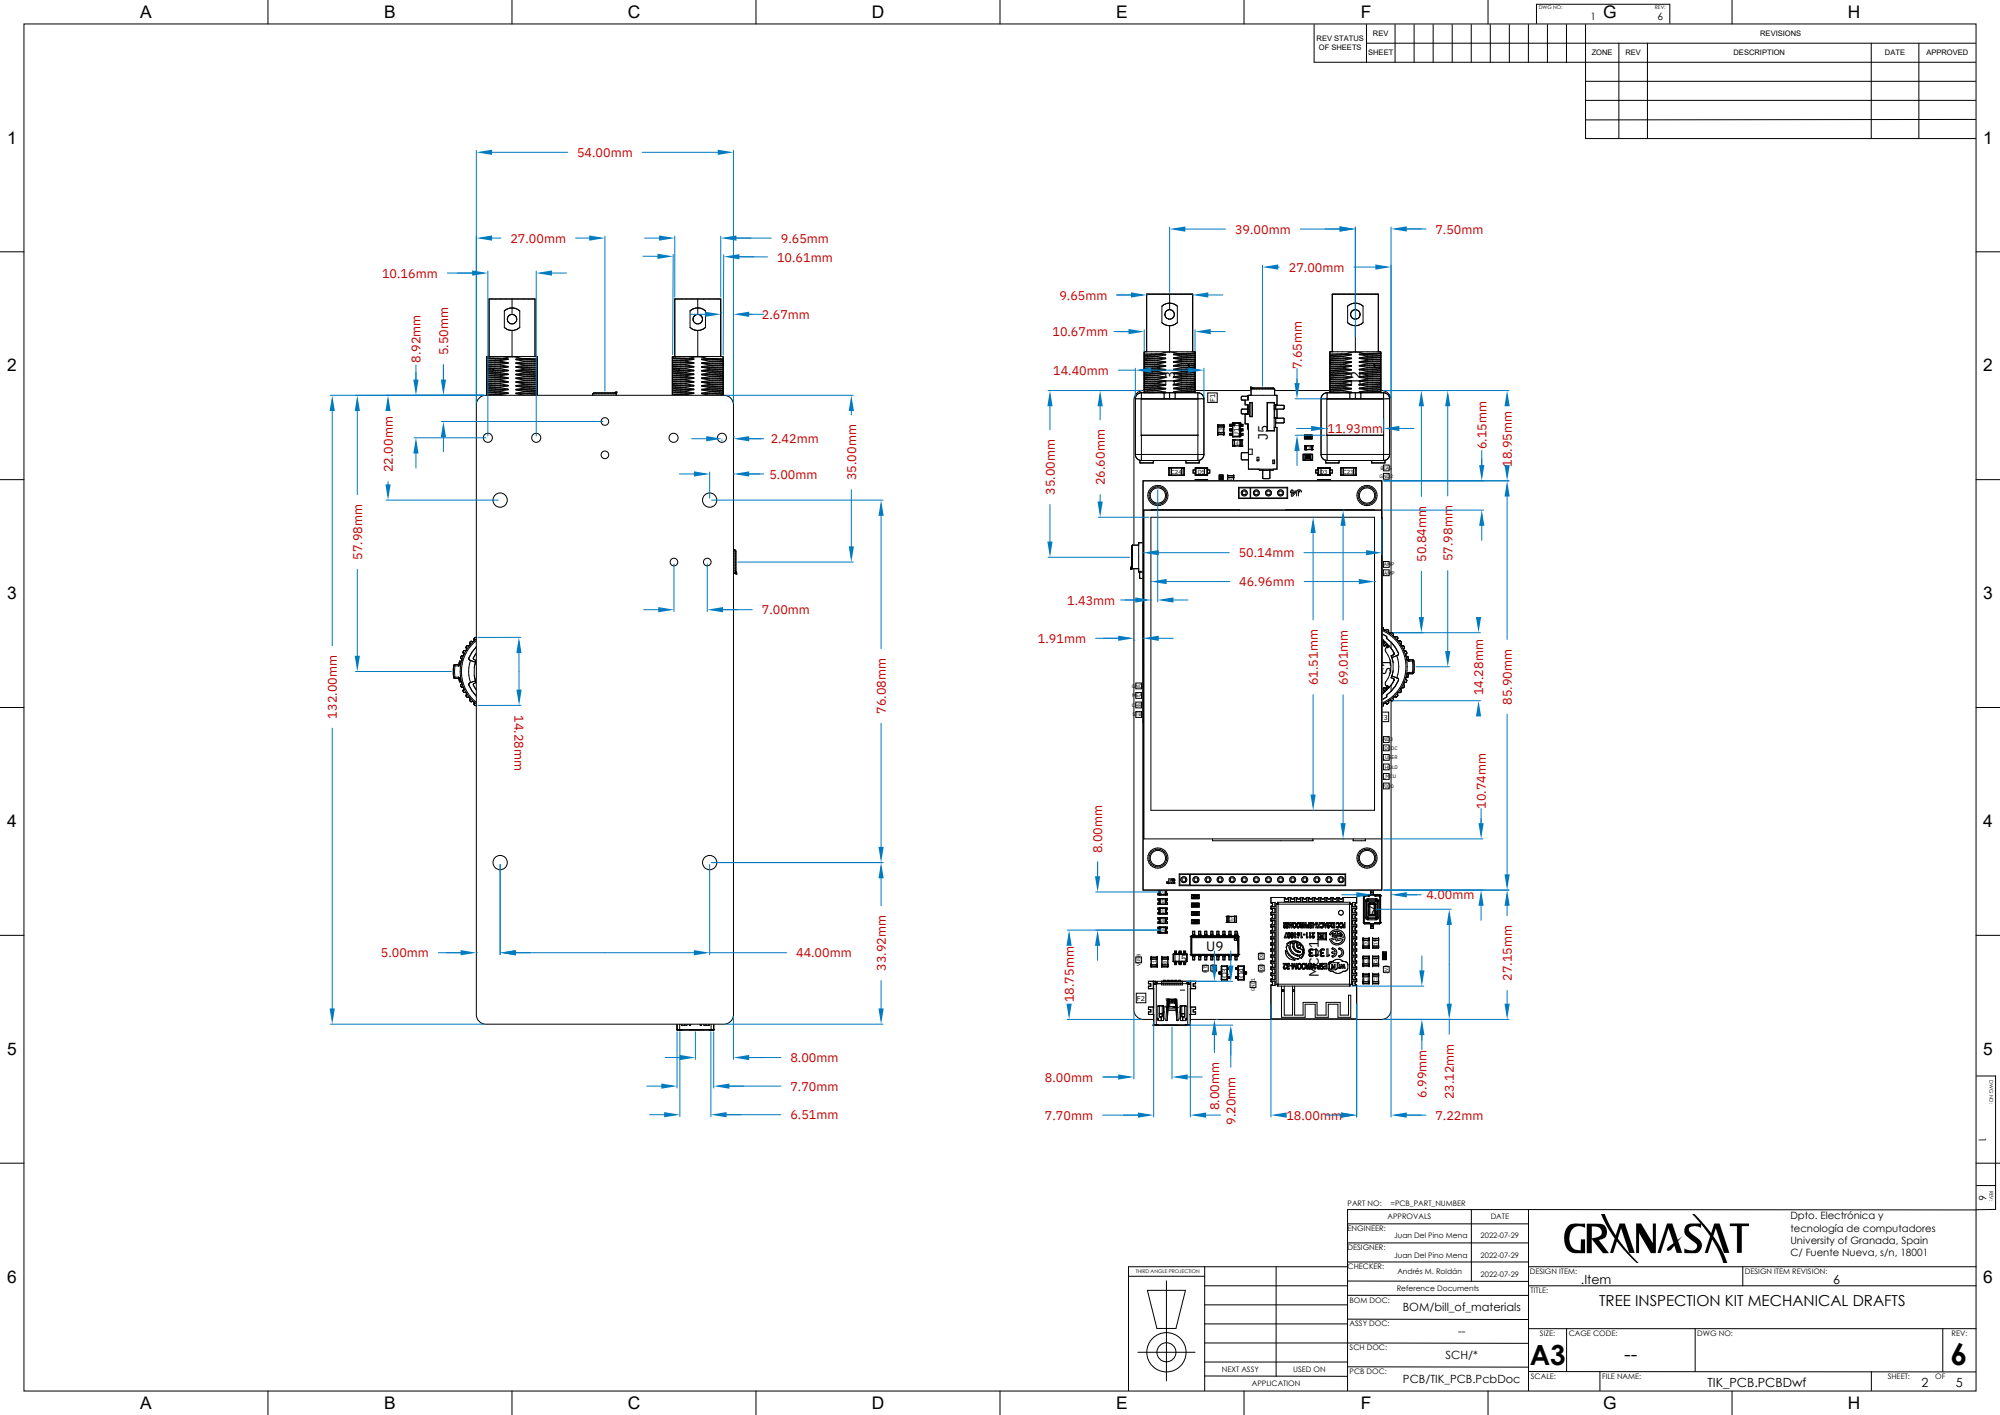
[picture p238: page 2]

APPROVALS | DATE

Dpto. Electrónica y
tecnología de computadores
University of Granada, Spain
C/ Fuente Nueva, s/n, 18001

ENGINEER: Juan Del Pino Mena | 2022-07-29

DESIGNER: Juan Del Pino Mena | 2022-07-29

THIRD ANGLE PROJECTION

CHECKER: Andrés M. Roldán | 2022-07-29

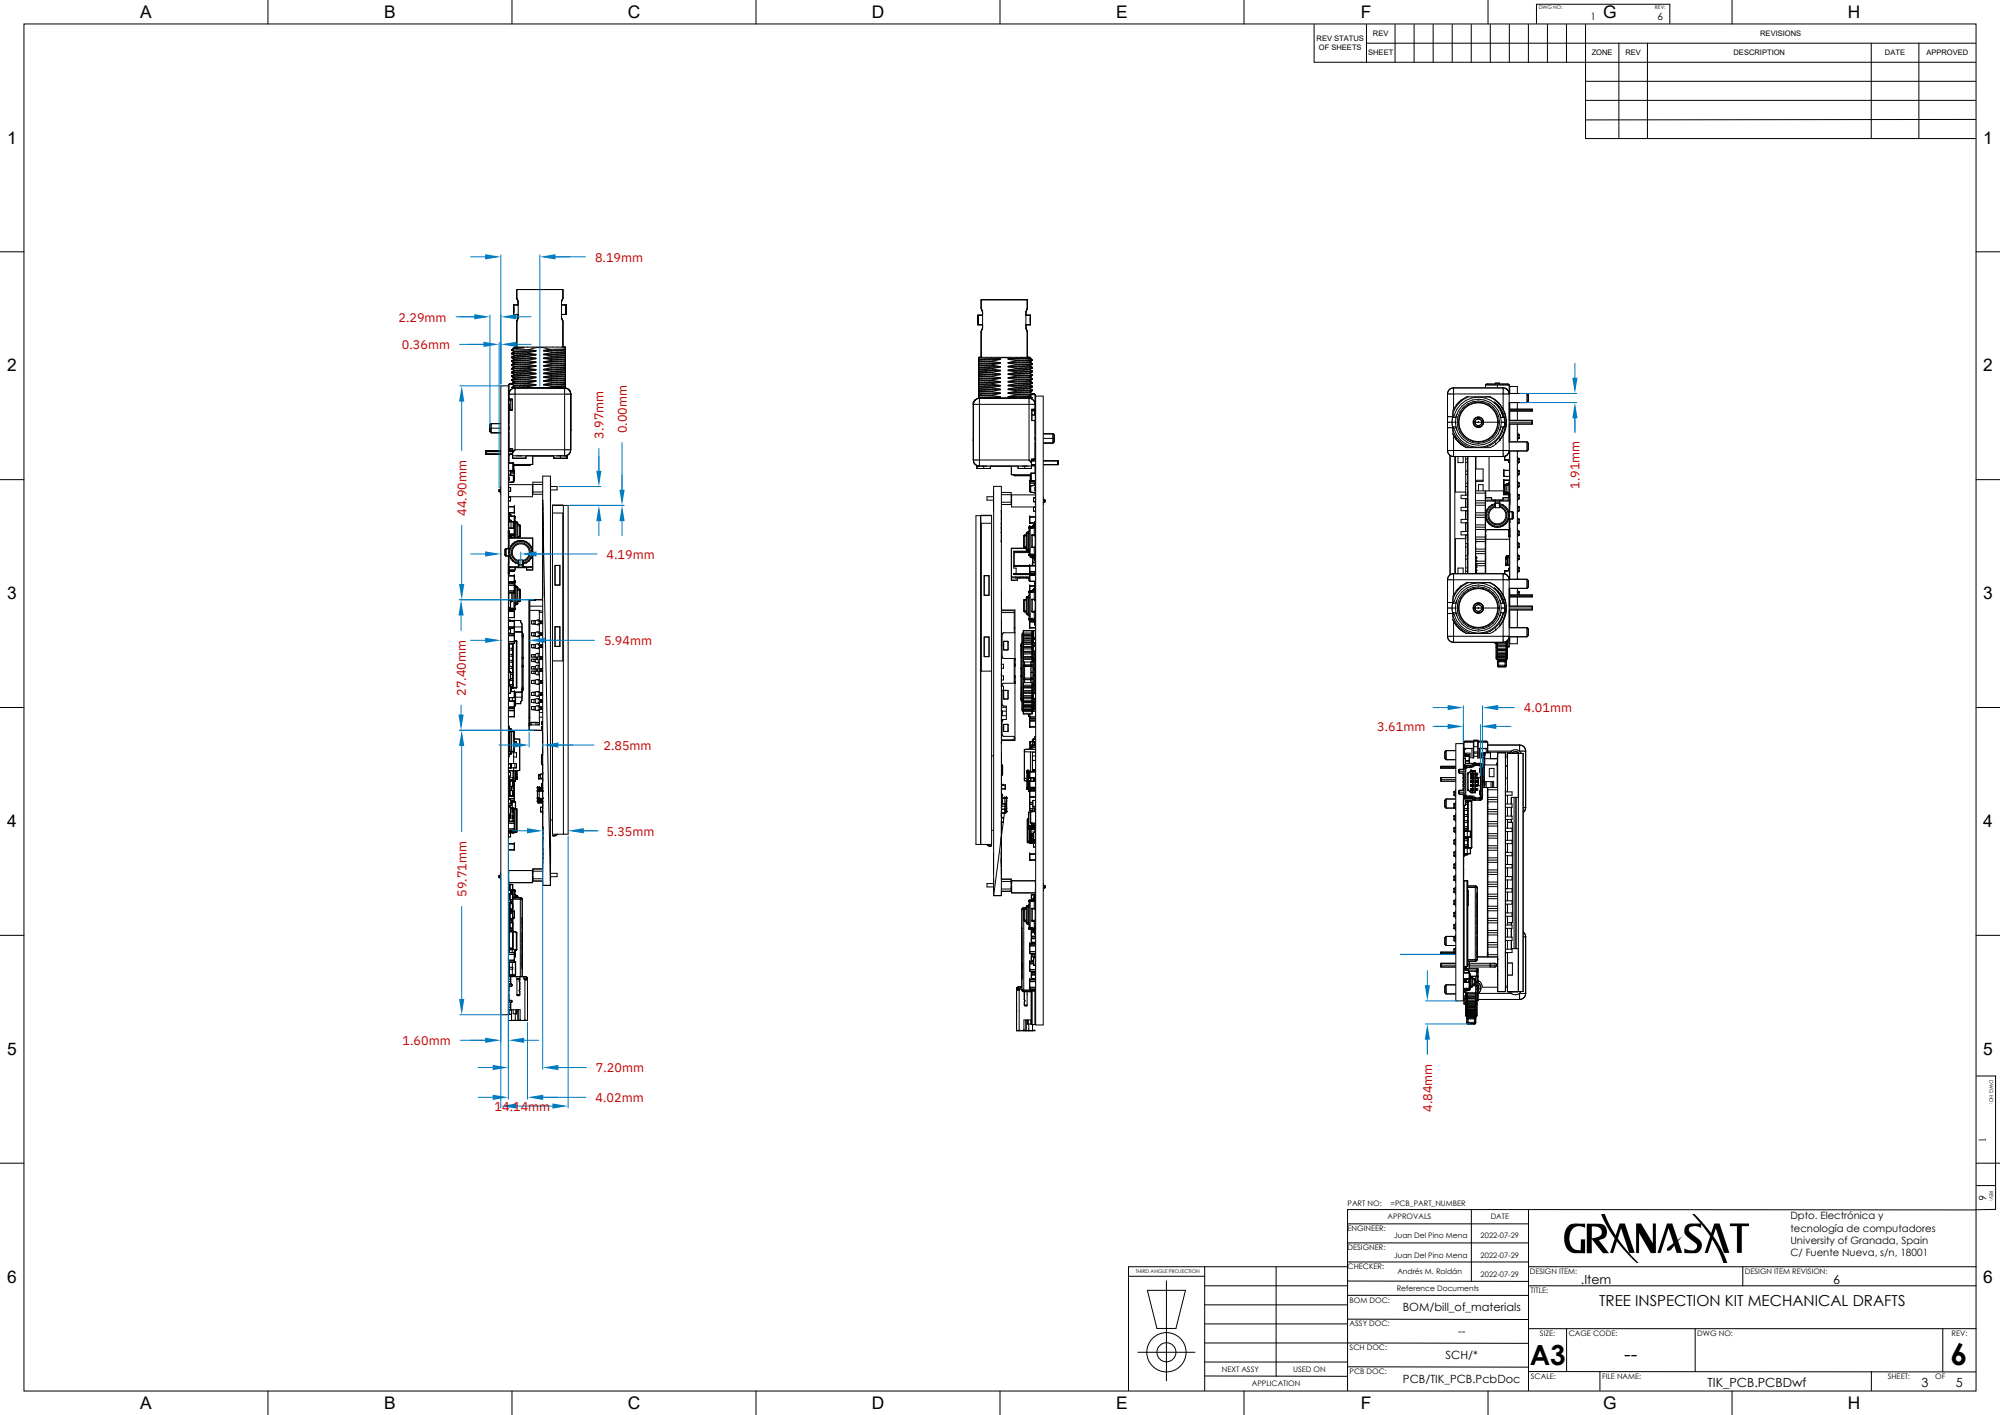
[picture p239: page 3]

APPROVALS | DATE

Dpto. Electrónica y
tecnología de computadores
University of Granada, Spain
C/ Fuente Nueva, s/n, 18001

ENGINEER: Juan Del Pino Mena | 2022-07-29

DESIGNER: Juan Del Pino Mena | 2022-07-29

THIRD ANGLE PROJECTION

CHECKER: Andrés M. Roldán | 2022-07-29

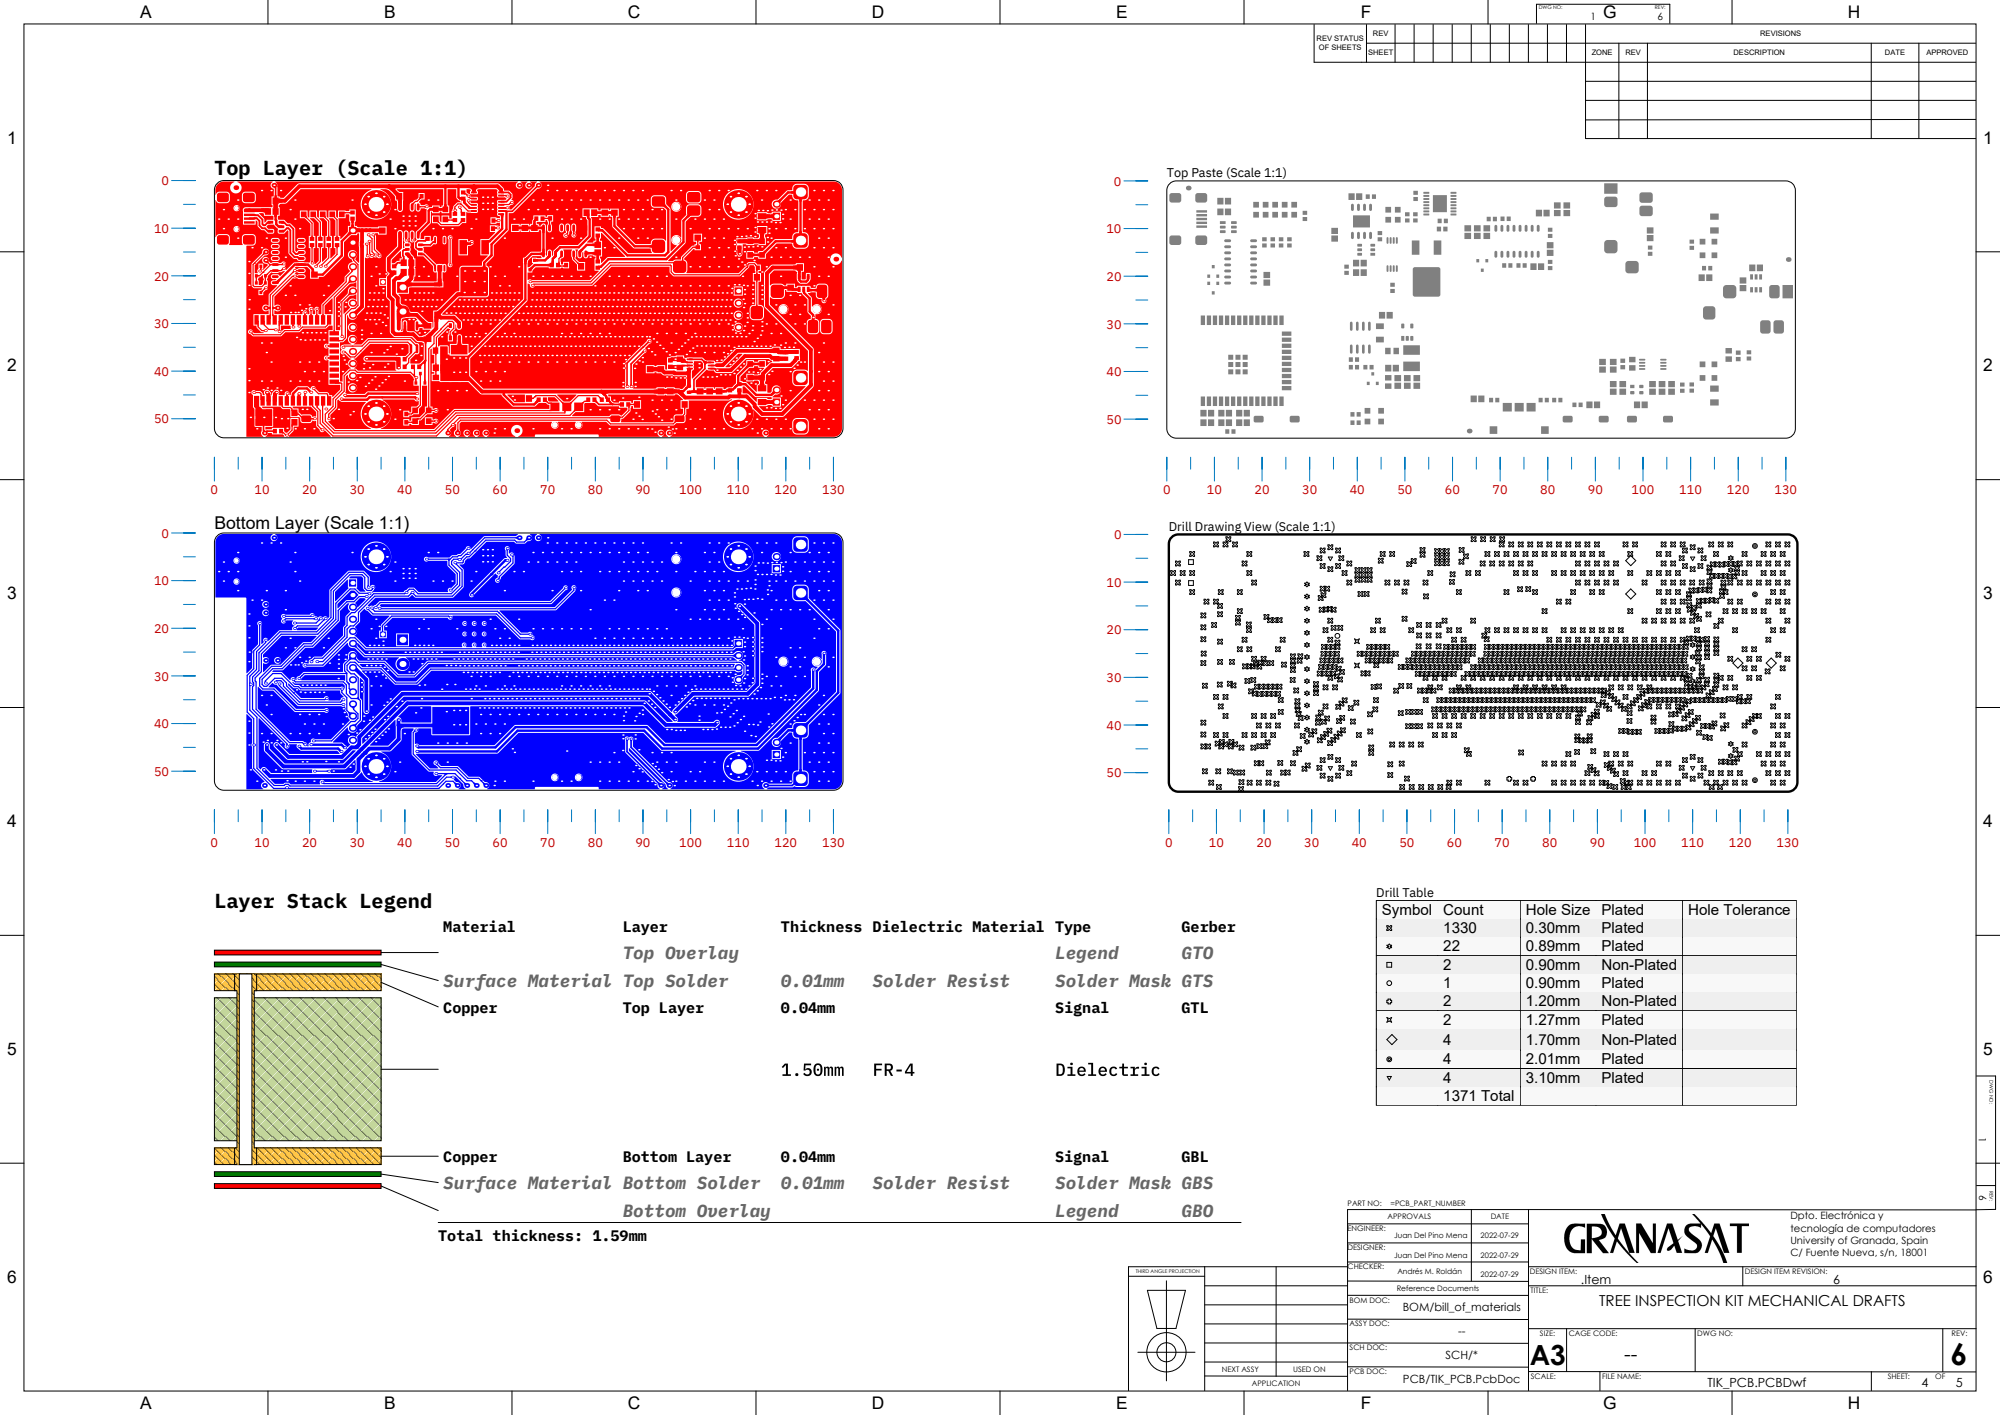
[picture p240: page 4]

Drill Drawing View (Scale 1:1)

APPROVALS | DATE

Dpto. Electrónica y
tecnología de computadores
University of Granada, Spain
C/ Fuente Nueva, s/n, 18001

ENGINEER: Juan Del Pino Mena | 2022-07-29

DESIGNER: Juan Del Pino Mena | 2022-07-29

THIRD ANGLE PROJECTION

CHECKER: Andrés M. Roldán | 2022-07-29

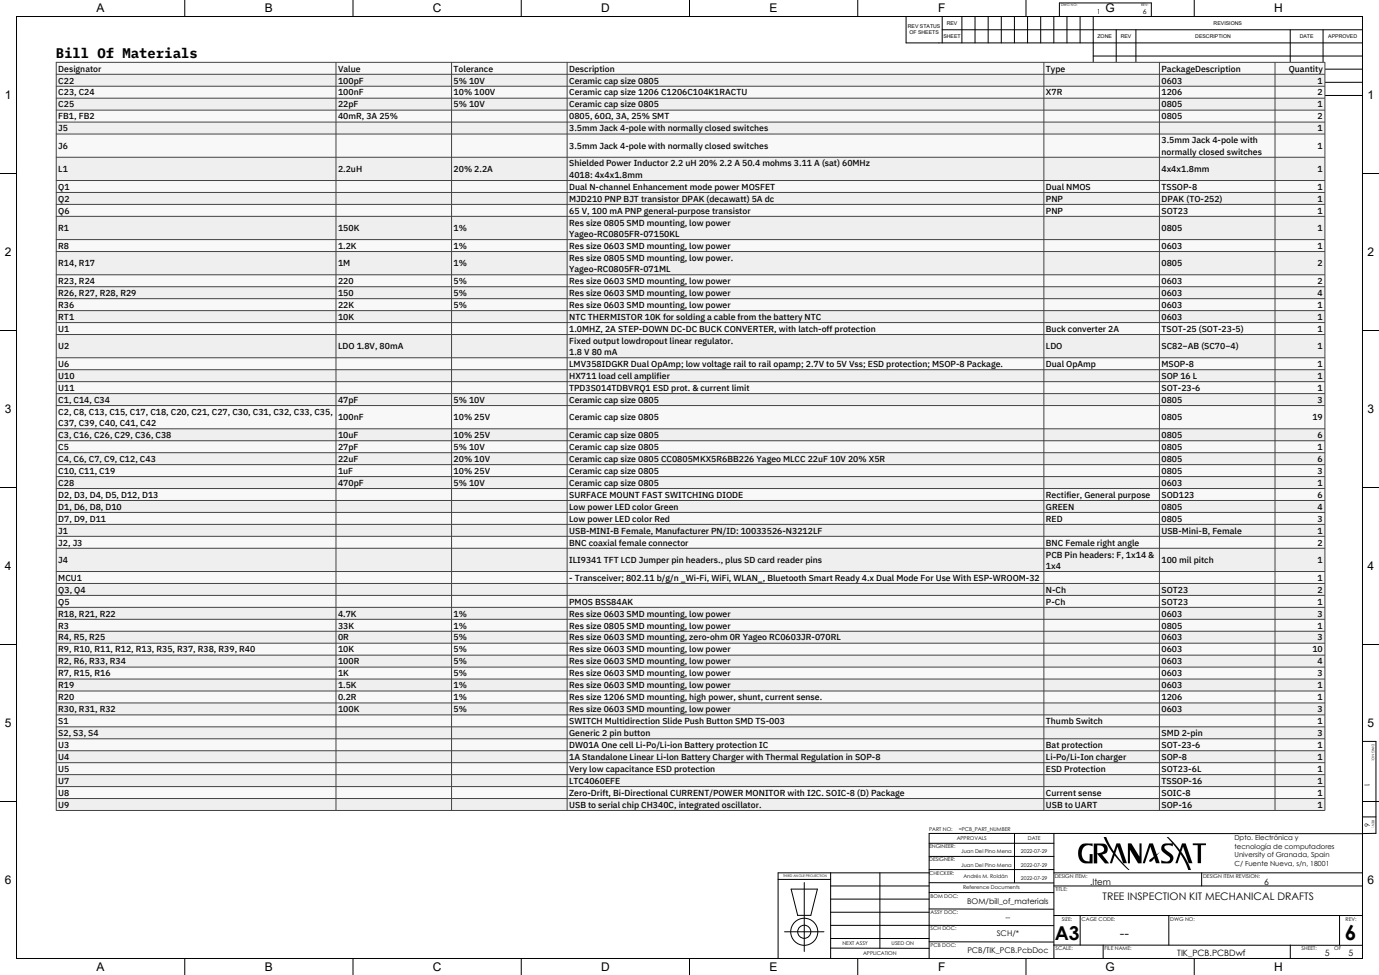
[picture p241: page 5]

Designator | Value | Tolerance | Description | Type | PackageDescription | | Quantity
C22 | 100pF | 5% 10V | Ceramic cap size 0805 | | 0603 | | 1
C23, C24 | 100nF | 10% 100V | Ceramic cap size 1206 C1206C104K1RACTU | X7R | 1206 | | 2
C25 | 22pF | 5% 10V | Ceramic cap size 0805 | | 0805 | 1
FB1, FB2 | 40mR, 3A 25% | | 0805, 60Ω, 3A, 25% SMT | | 0805 | 2
J5 | | | 3.5mm Jack 4-pole with normally closed switches | | | 1
J6 | | | 3.5mm Jack 4-pole with normally closed switches | | 3.5mm Jack 4-pole with normally closed switches | 1

L1 | 2.2uH | 20% 2.2A | Shielded Power Inductor 2.2 uH 20% 2.2 A 50.4 mohms 3.11 A (sat) 60MHz 4018: 4x4x1.8mm | | 4x4x1.8mm | 1

Q1 | | | Dual N-channel Enhancement mode power MOSFET | Dual NMOS | TSSOP-8 | 1
Q2 | | | MJD210 PNP BJT transistor DPAK (decawatt) 5A dc | PNP | DPAK (TO-252) | 1
Q6 | | | 65 V, 100 mA PNP general-purpose transistor | PNP | SOT23 | 1
R1 | 150K | 1% | Res size 0805 SMD mounting, low power Yageo-RC0805FR-07150KL | | 0805 | 1

R8 | 1.2K | 1% | Res size 0603 SMD mounting, low power | | 0603 | 1
R14, R17 | 1M | 1% | Res size 0805 SMD mounting, low power. Yageo-RC0805FR-071ML | | 0805 | 2

R23, R24 | 220 | 5% | Res size 0603 SMD mounting, low power | | 0603 | 2
R26, R27, R28, R29 | 150 | 5% | Res size 0603 SMD mounting, low power | | 0603 | 4
R36 | 22K | 5% | Res size 0603 SMD mounting, low power | | 0603 | 1
RT1 | 10K | | NTC THERMISTOR 10K for solding a cable from the battery NTC | | 0603 | 1
U1 | | | 1.0MHZ, 2A STEP-DOWN DC-DC BUCK CONVERTER, with latch-off protection | Buck converter 2A | TSOT-25 (SOT-23-5) | 1
U2 | LDO 1.8V, 80mA | | Fixed output lowdropout linear regulator. 1.8 V 80 mA | LDO | SC82−AB (SC70−4) | 1

U6 | | | LMV358IDGKR Dual OpAmp; low voltage rail to rail opamp; 2.7V to 5V Vss; ESD protection; MSOP-8 Package. | Dual OpAmp | MSOP-8 | 1
U10 | | | HX711 load cell amplifier | | SOP 16 L | 1
U11 | | | TPD3S014TDBVRQ1 ESD prot. & current limit | | SOT-23-6 | 1
C1, C14, C34 | 47pF | 5% 10V | Ceramic cap size 0805 | | 0805 | 3
C2, C8, C13, C15, C17, C18, C20, C21, C27, C30, C31, C32, C33, C35, C37, C39, C40, C41, C42 | 100nF | 10% 25V | Ceramic cap size 0805 | | 0805 | 19

C3, C16, C26, C29, C36, C38 | 10uF | 10% 25V | Ceramic cap size 0805 | | 0805 | 6
C5 | 27pF | 5% 10V | Ceramic cap size 0805 | | 0805 | 1
C4, C6, C7, C9, C12, C43 | 22uF | 20% 10V | Ceramic cap size 0805 CC0805MKX5R6BB226 Yageo MLCC 22uF 10V 20% X5R | | 0805 | 6
C10, C11, C19 | 1uF | 10% 25V | Ceramic cap size 0805 | | 0805 | 3
C28 | 470pF | 5% 10V | Ceramic cap size 0805 | | 0603 | 1
D2, D3, D4, D5, D12, D13 | | | SURFACE MOUNT FAST SWITCHING DIODE | Rectifier, General purpose | SOD123 | 6
D1, D6, D8, D10 | | | Low power LED color Green | GREEN | 0805 | 4
D7, D9, D11 | | | Low power LED color Red | RED | 0805 | 3
J1 | | | USB-MINI-B Female, Manufacturer PN/ID: 10033526-N3212LF | | USB-Mini-B, Female | 1
J2, J3 | | | BNC coaxial female connector | BNC Female right angle | | 2
J4 | | | ILI9341 TFT LCD Jumper pin headers., plus SD card reader pins | PCB Pin headers: F, 1x14 & 1x4 | 100 mil pitch | 1

MCU1 | | | - Transceiver; 802.11 b/g/n _Wi-Fi, WiFi, WLAN_, Bluetooth Smart Ready 4.x Dual Mode For Use With ESP-WROOM-32 | | | 1
Q3, Q4 | | | | N-Ch | SOT23 | 2
Q5 | | | PMOS BSS84AK | P-Ch | SOT23 | 1
R18, R21, R22 | 4.7K | 1% | Res size 0603 SMD mounting, low power | | 0603 | 3
R3 | 33K | 1% | Res size 0805 SMD mounting, low power | | 0805 | 1
R4, R5, R25 | 0R | 5% | Res size 0603 SMD mounting, zero-ohm 0R Yageo RC0603JR-070RL | | 0603 | 3
R9, R10, R11, R12, R13, R35, R37, R38, R39, R40 | 10K | 5% | Res size 0603 SMD mounting, low power | | 0603 | 10
R2, R6, R33, R34 | 100R | 5% | Res size 0603 SMD mounting, low power | | 0603 | 4
R7, R15, R16 | 1K | 5% | Res size 0603 SMD mounting, low power | | 0603 | 3
R19 | 1.5K | 1% | Res size 0603 SMD mounting, low power | | 0603 | 1
R20 | 0.2R | 1% | Res size 1206 SMD mounting, high power, shunt, current sense. | | 1206 | 1
R30, R31, R32 | 100K | 5% | Res size 0603 SMD mounting, low power | | 0603 | 3
S1 | | | SWITCH Multidirection Slide Push Button SMD TS-003 | Thumb Switch | | 1
S2, S3, S4 | | | Generic 2 pin button | | SMD 2-pin | 3
U3 | | | DW01A One cell Li-Po/Li-ion Battery protection IC | Bat protection | SOT-23-6 | 1
U4 | | | 1A Standalone Linear Li-lon Battery Charger with Thermal Regulation in SOP-8 | Li-Po/Li-Ion charger | SOP-8 | 1
U5 | | | Very low capacitance ESD protection | ESD Protection | SOT23-6L | 1
U7 | | | LTC4060EFE | | TSSOP-16 | 1
U8 | | | Zero-Drift, Bi-Directional CURRENT/POWER MONITOR with I2C. SOIC-8 (D) Package | Current sense | SOIC-8 | 1
U9 | | | USB to serial chip CH340C, integrated oscillator. | USB to UART | SOP-16 | 1

APPROVALS | DATE

Dpto. Electrónica y
tecnología de computadores
University of Granada, Spain
C/ Fuente Nueva, s/n, 18001

ENGINEER: Juan Del Pino Mena | 2022-07-29

DESIGNER: Juan Del Pino Mena | 2022-07-29

THIRD ANGLE PROJECTION

CHECKER: Andrés M. Roldán | 2022-07-29
