dpmj/Bachelor_Thesis_TIK_Handheld_Device/ASSETS/TIK_CASE/PROTO/PROTO_ASM.pdf

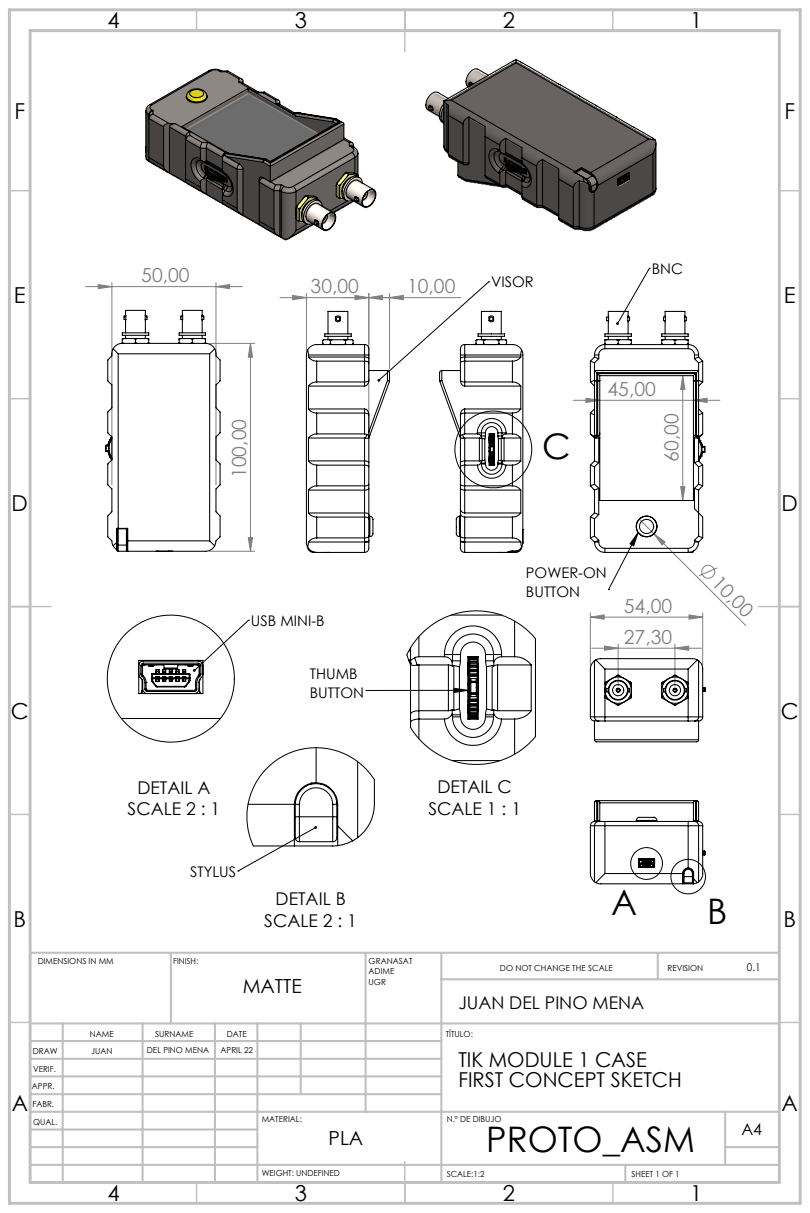
[picture p242: page 1]
VISOR 50,00; DETAIL A SCALE 2 : 1; USB MINI-B; DETAIL B SCALE 2 : 1; DETAIL C SCALE 1 : 1; DIMENSIONS IN MM; FINISH:; GRANASAT; DO NOT CHANGE THE SCALE; REVISION; SCALE:1:2; SHEET 1 OF 1; WEIGHT: UNDEFINED

JUAN DEL PINO MENA

NAME | SURNAME | DATE | | | | TÍTULO: TIK MODULE 1 CASE FIRST CONCEPT SKETCH

DRAW | JUAN | DEL PINO MENA | APRIL 22
VERIF.
APPR.
FABR.
QUAL. | | | | MATERIAL: PLA | N.º DE DIBUJO PROTO_ASM | A4
