dpmj/Bachelor_Thesis_TIK_Handheld_Device/ASSETS/TIK_CASE/PROTO/PROTO_ASM2.pdf

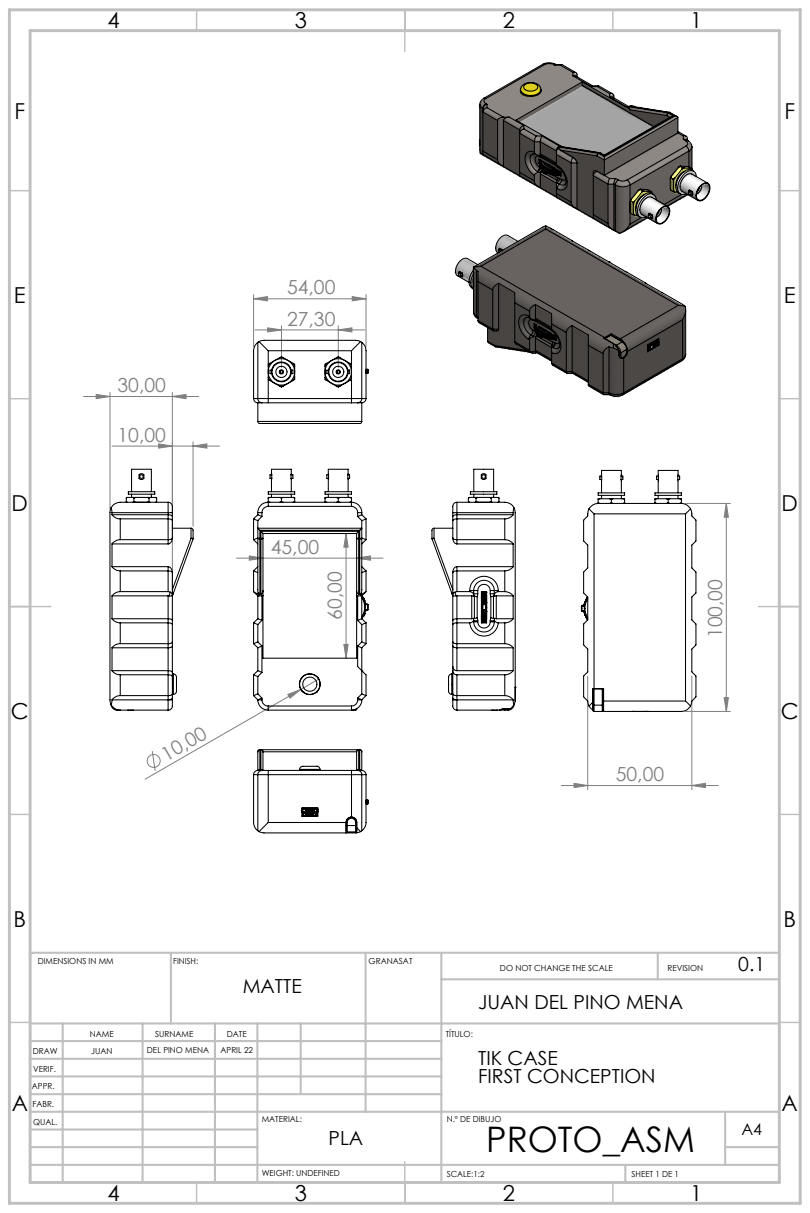
[picture p243: page 1]
DIMENSIONS IN MM; FINISH:; GRANASAT; DO NOT CHANGE THE SCALE; REVISION; SCALE:1:2; SHEET 1 DE 1; WEIGHT: UNDEFINED

JUAN DEL PINO MENA

NAME | SURNAME | DATE | | | | TÍTULO: TIK CASE FIRST CONCEPTION

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
