dpmj/Bachelor_Thesis_TIK_Handheld_Device/SIMULATIONS/TIK_SIMULATIONS/OUTPUT/PDF/sim_sch.pdf

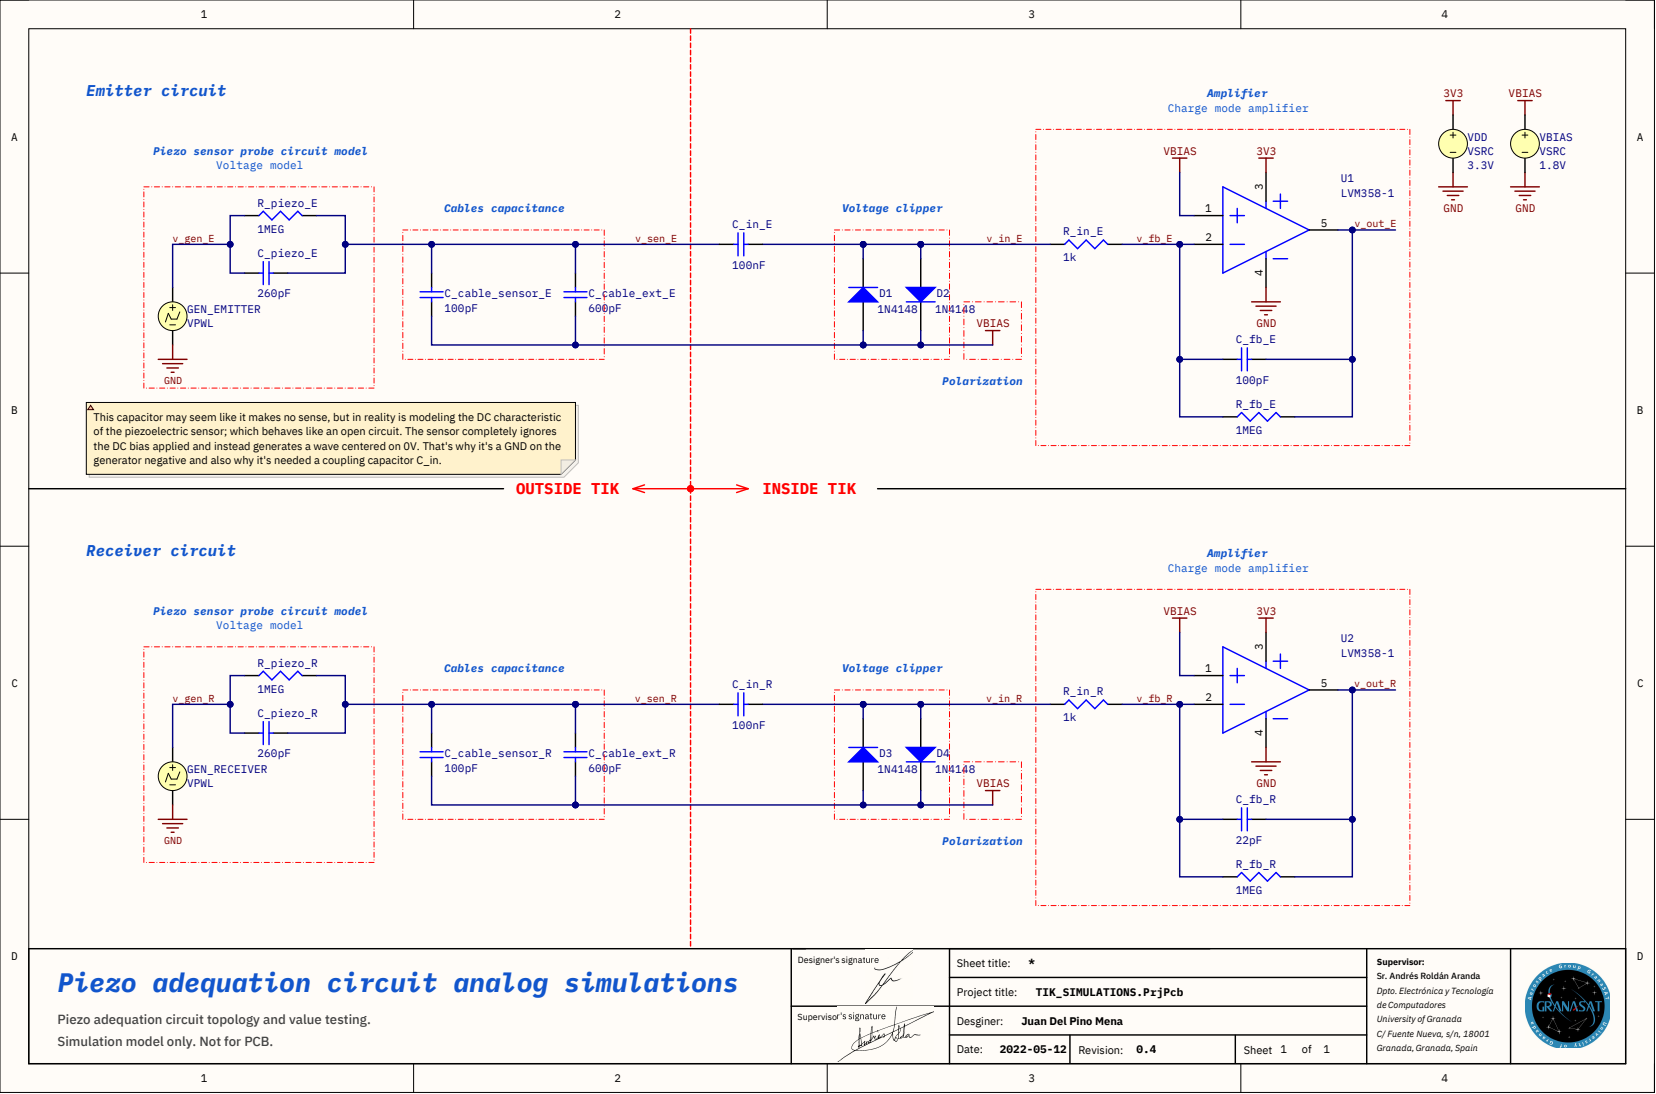
[picture p244: page 1]

Pi ezo sensor probe c i rcui t model

Cabl es capac i tance

This capacitor may seem like it makes no sense, but in reality is modeling the DC characteristic
of the piezoelectric sensor; which behaves like an open circuit. The sensor completely ignores
the DC bias applied and instead generates a wave centered on 0V. That's why it's a GND on the
generator negative and also why it's needed a coupling capacitor C_in.

Piezo adequation circuit anal og simul ations

Supervisor:
Sr. Andrés Roldán Aranda
Dpto. Electrónica y Tecnología
de Computadores
University of Granada
C/ Fuente Nueva, s/n, 18001
Granada, Granada, Spain

TI K_SI MUL ATI ONS. P rj P c b

Piezo adequation circuit topology and value testing.
Simulation model only. Not for PCB.

Supervisor's signature | Desginer: Juan Del Pino Mena

Date: 2022- 05- 12 | Revision: 0. 4 | Sheet 1 of 1
