dpmj/Bachelor_Thesis_TIK_Handheld_Device/OUTPUT/PDF/output.PDF

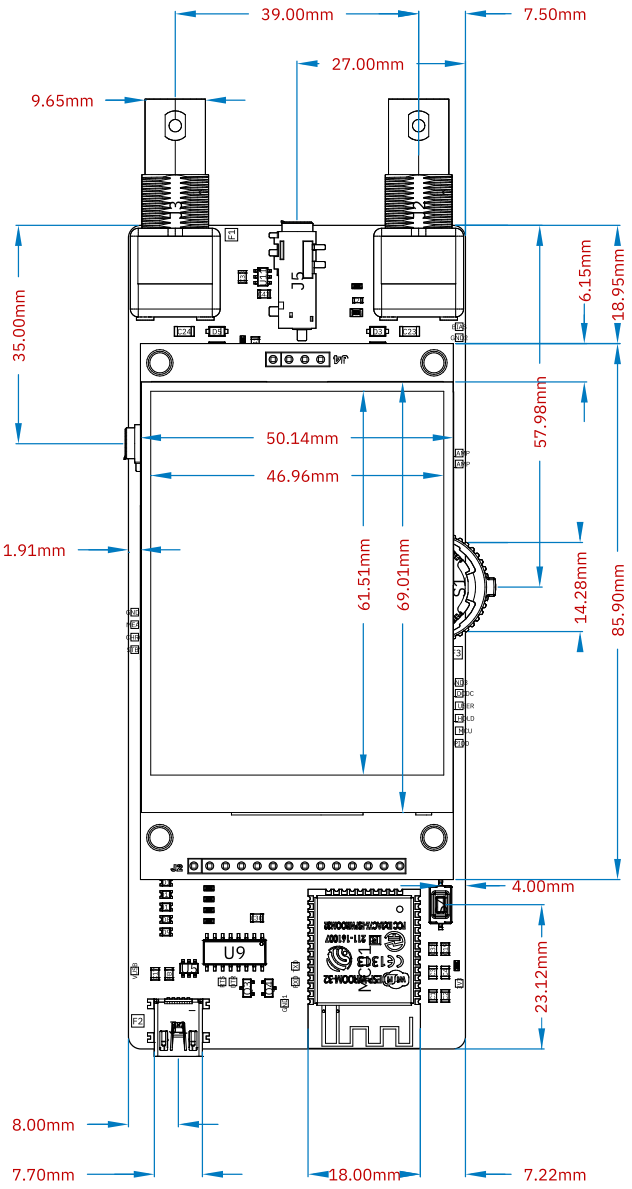
[picture p249: page 1]
