dpmj/Bachelor_Thesis_TIK_Handheld_Device/OUTPUT/PDF/TIK_HandheldSystem_SCH_v0_1.PDF

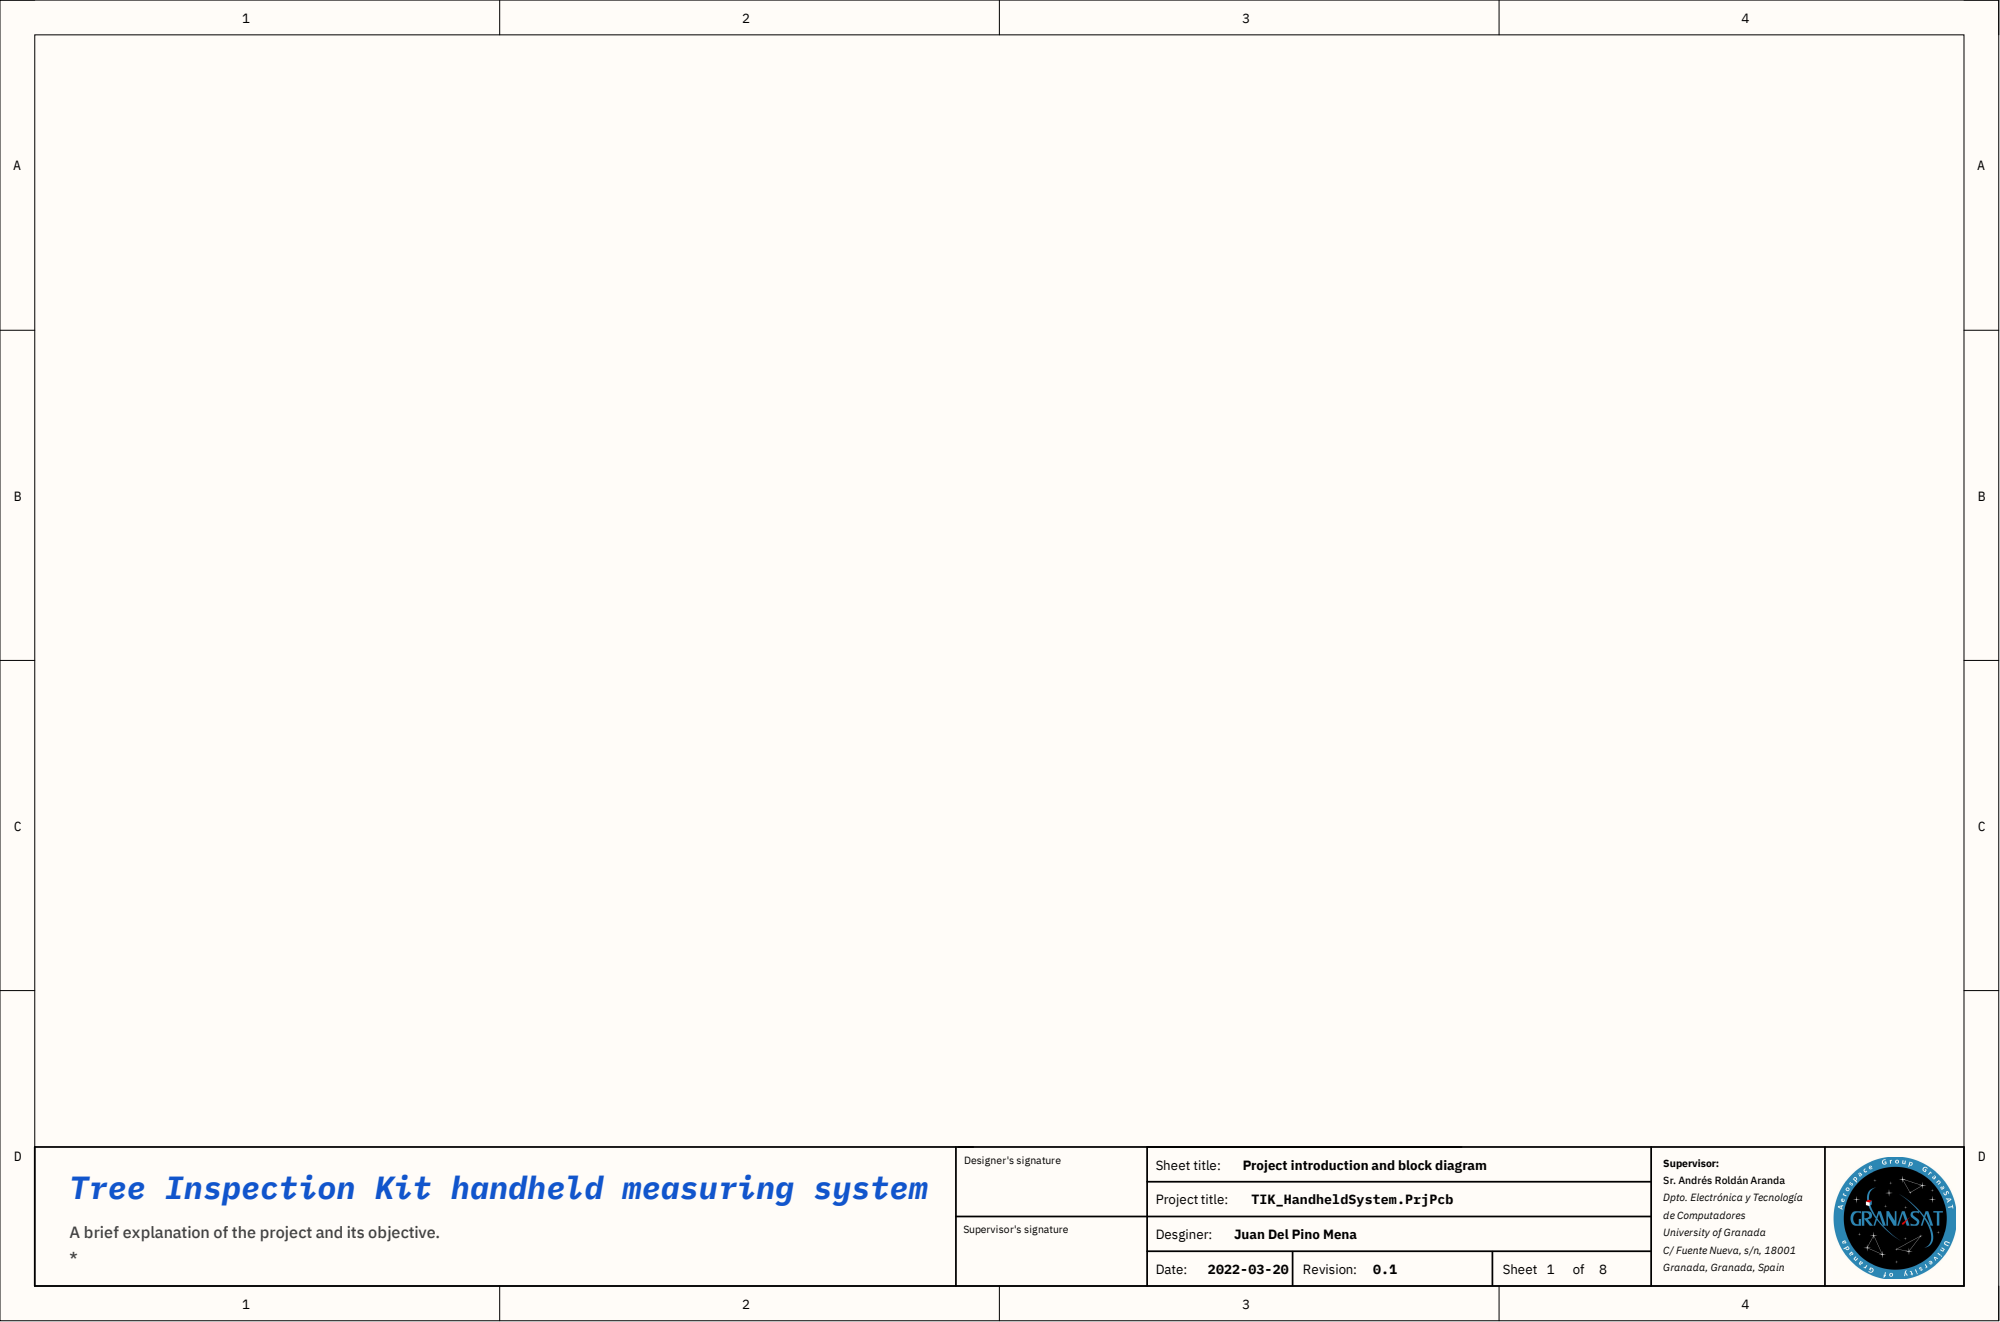
[picture p250: page 1]

Tree Inspection Kit handhel d measuring system

Project introduction and block diagram

Supervisor:
Sr. Andrés Roldán Aranda
Dpto. Electrónica y Tecnología
de Computadores
University of Granada
C/ Fuente Nueva, s/n, 18001
Granada, Granada, Spain

TI K_ H an dh el dSys tem. P rj P c b

A brief explanation of the project and its objective.

Supervisor's signature | Desginer: Juan Del Pino Mena

Date: 2022- 03- 20 | Revision: 0. 1 | Sheet 1 of 8

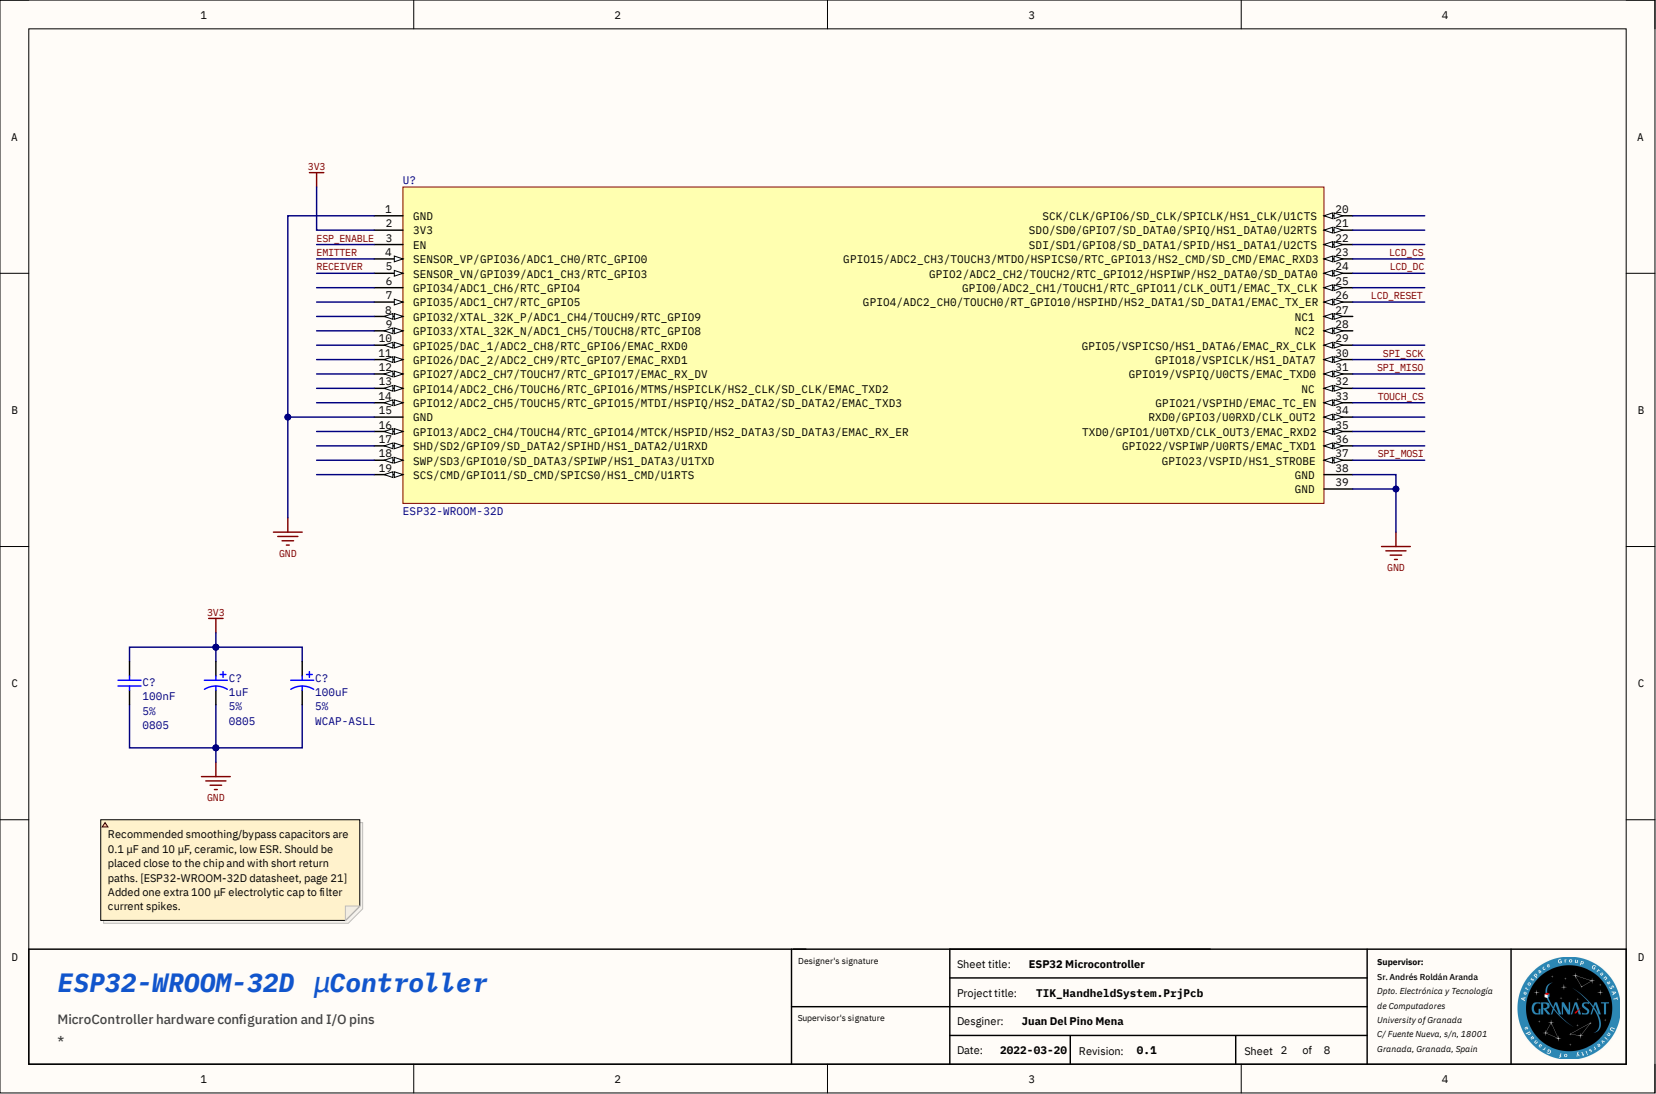
[picture p251: page 2]

ESP32 Microcontroller TI K_ H an dh el dSys te

S u pervi sor ' g | D esgine r : Juan Del Pi no Men

ate 2 0 -3 | R e v ision . 1 | She t 2 of

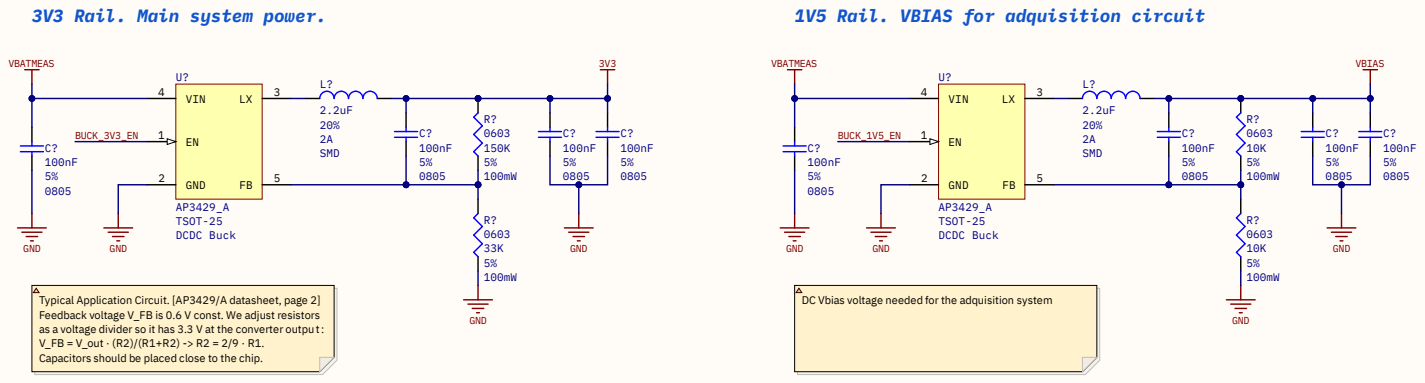
[picture p252: page 3]

attery DC/DC ste

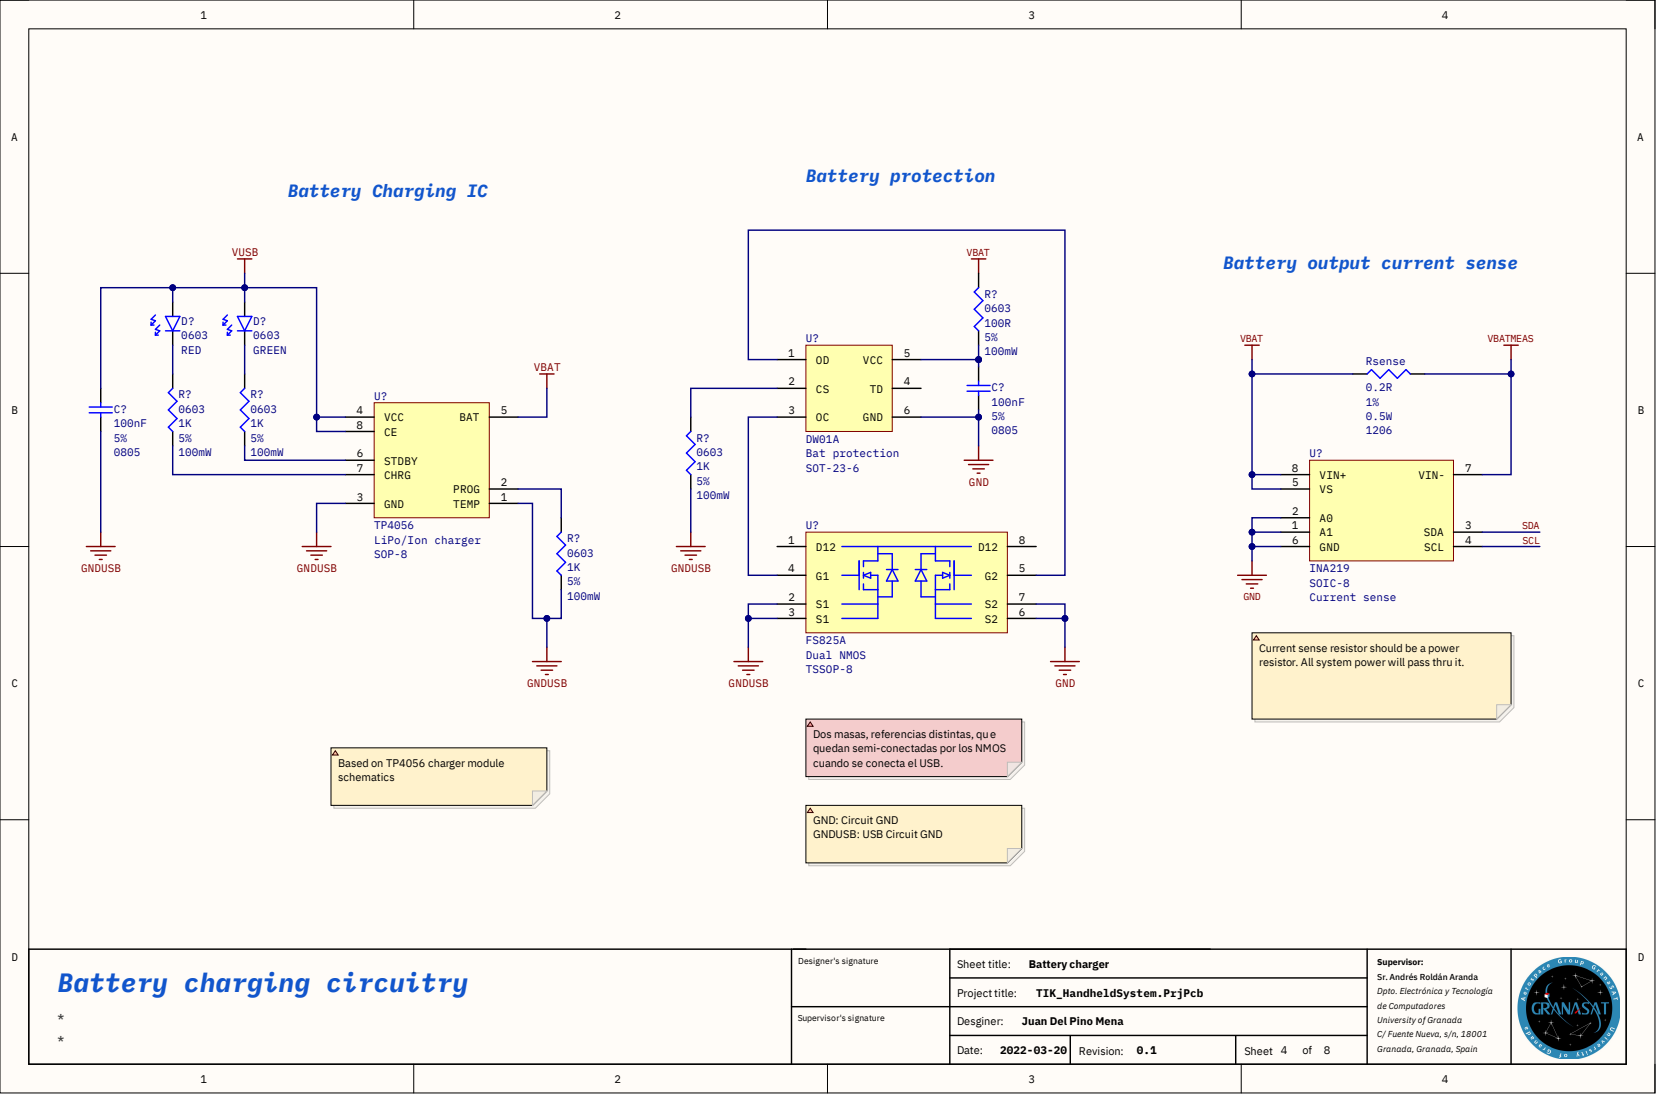
[picture p253: page 4]

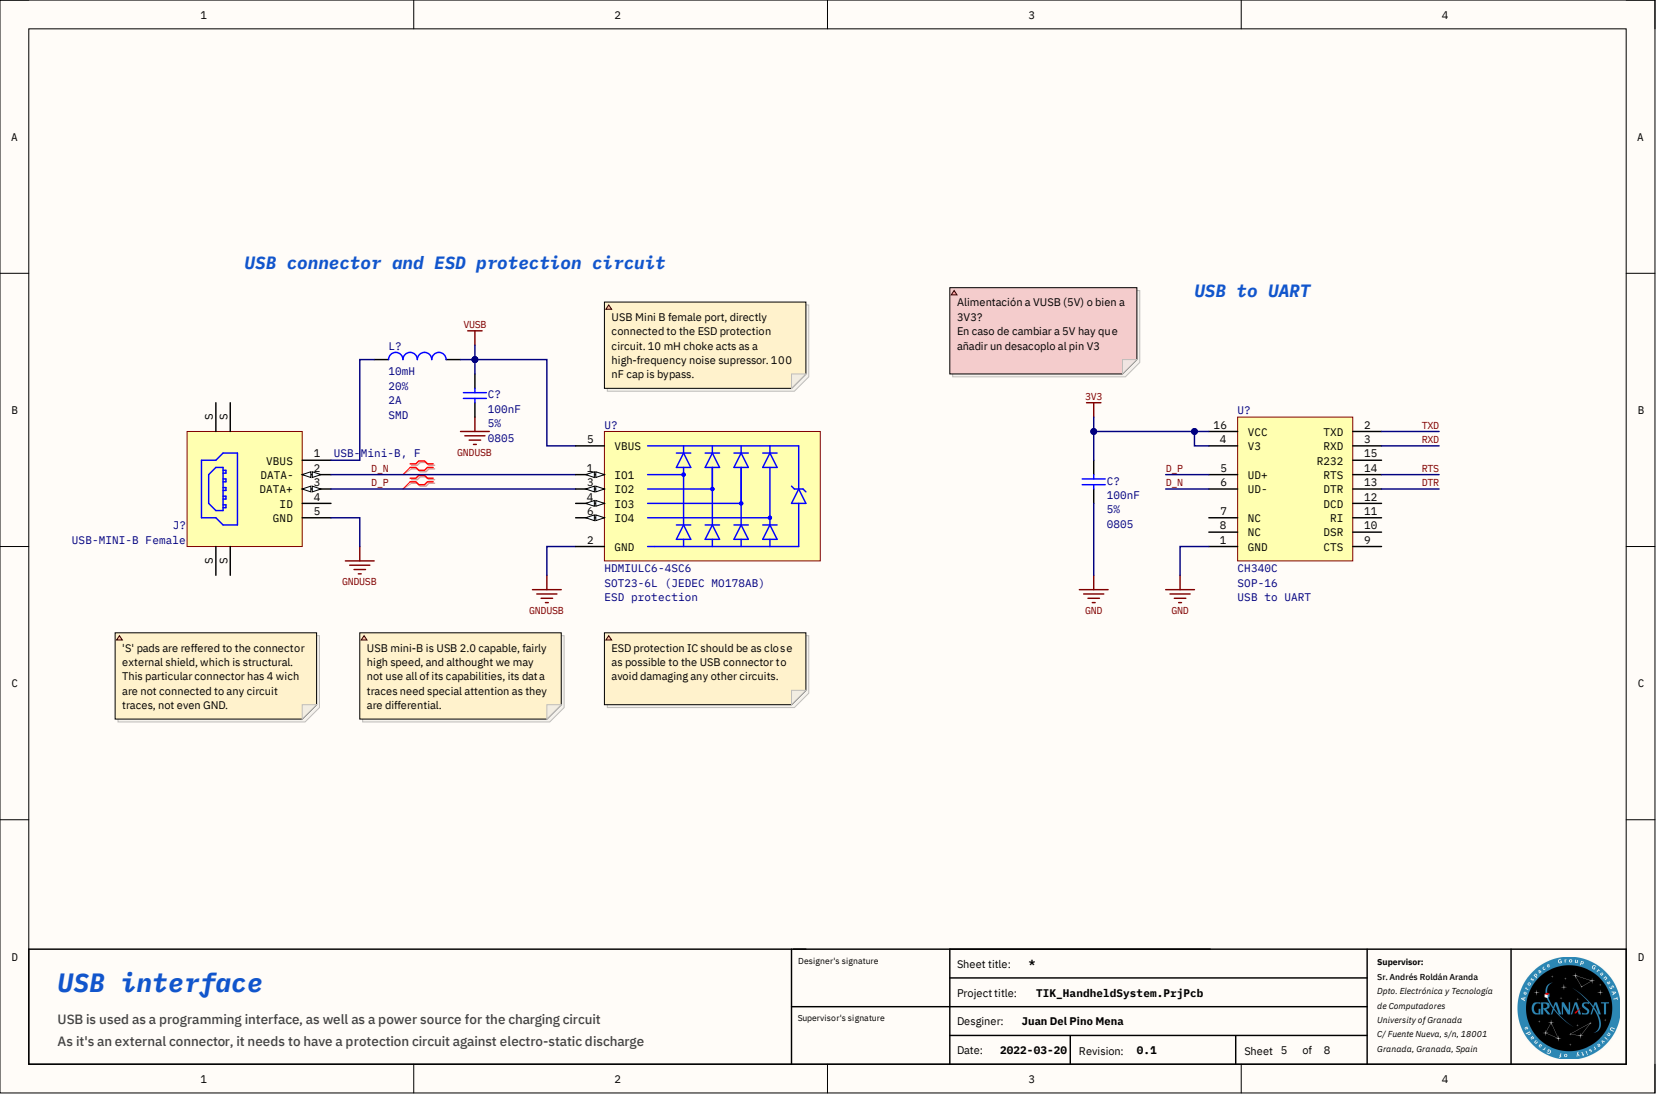
[picture p254: page 5]

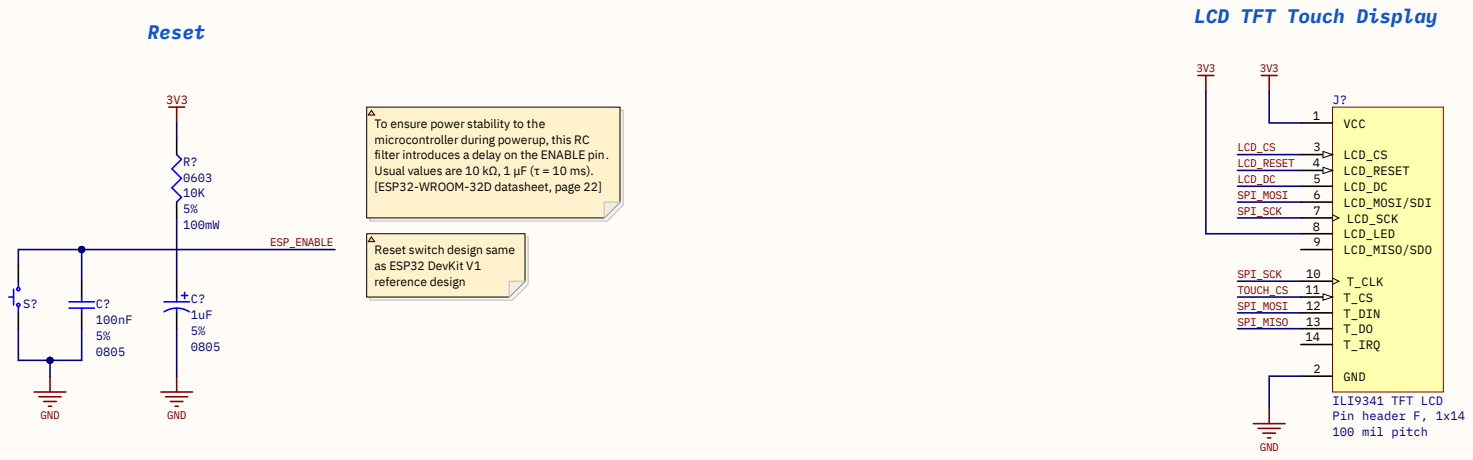
[picture p255: page 6]

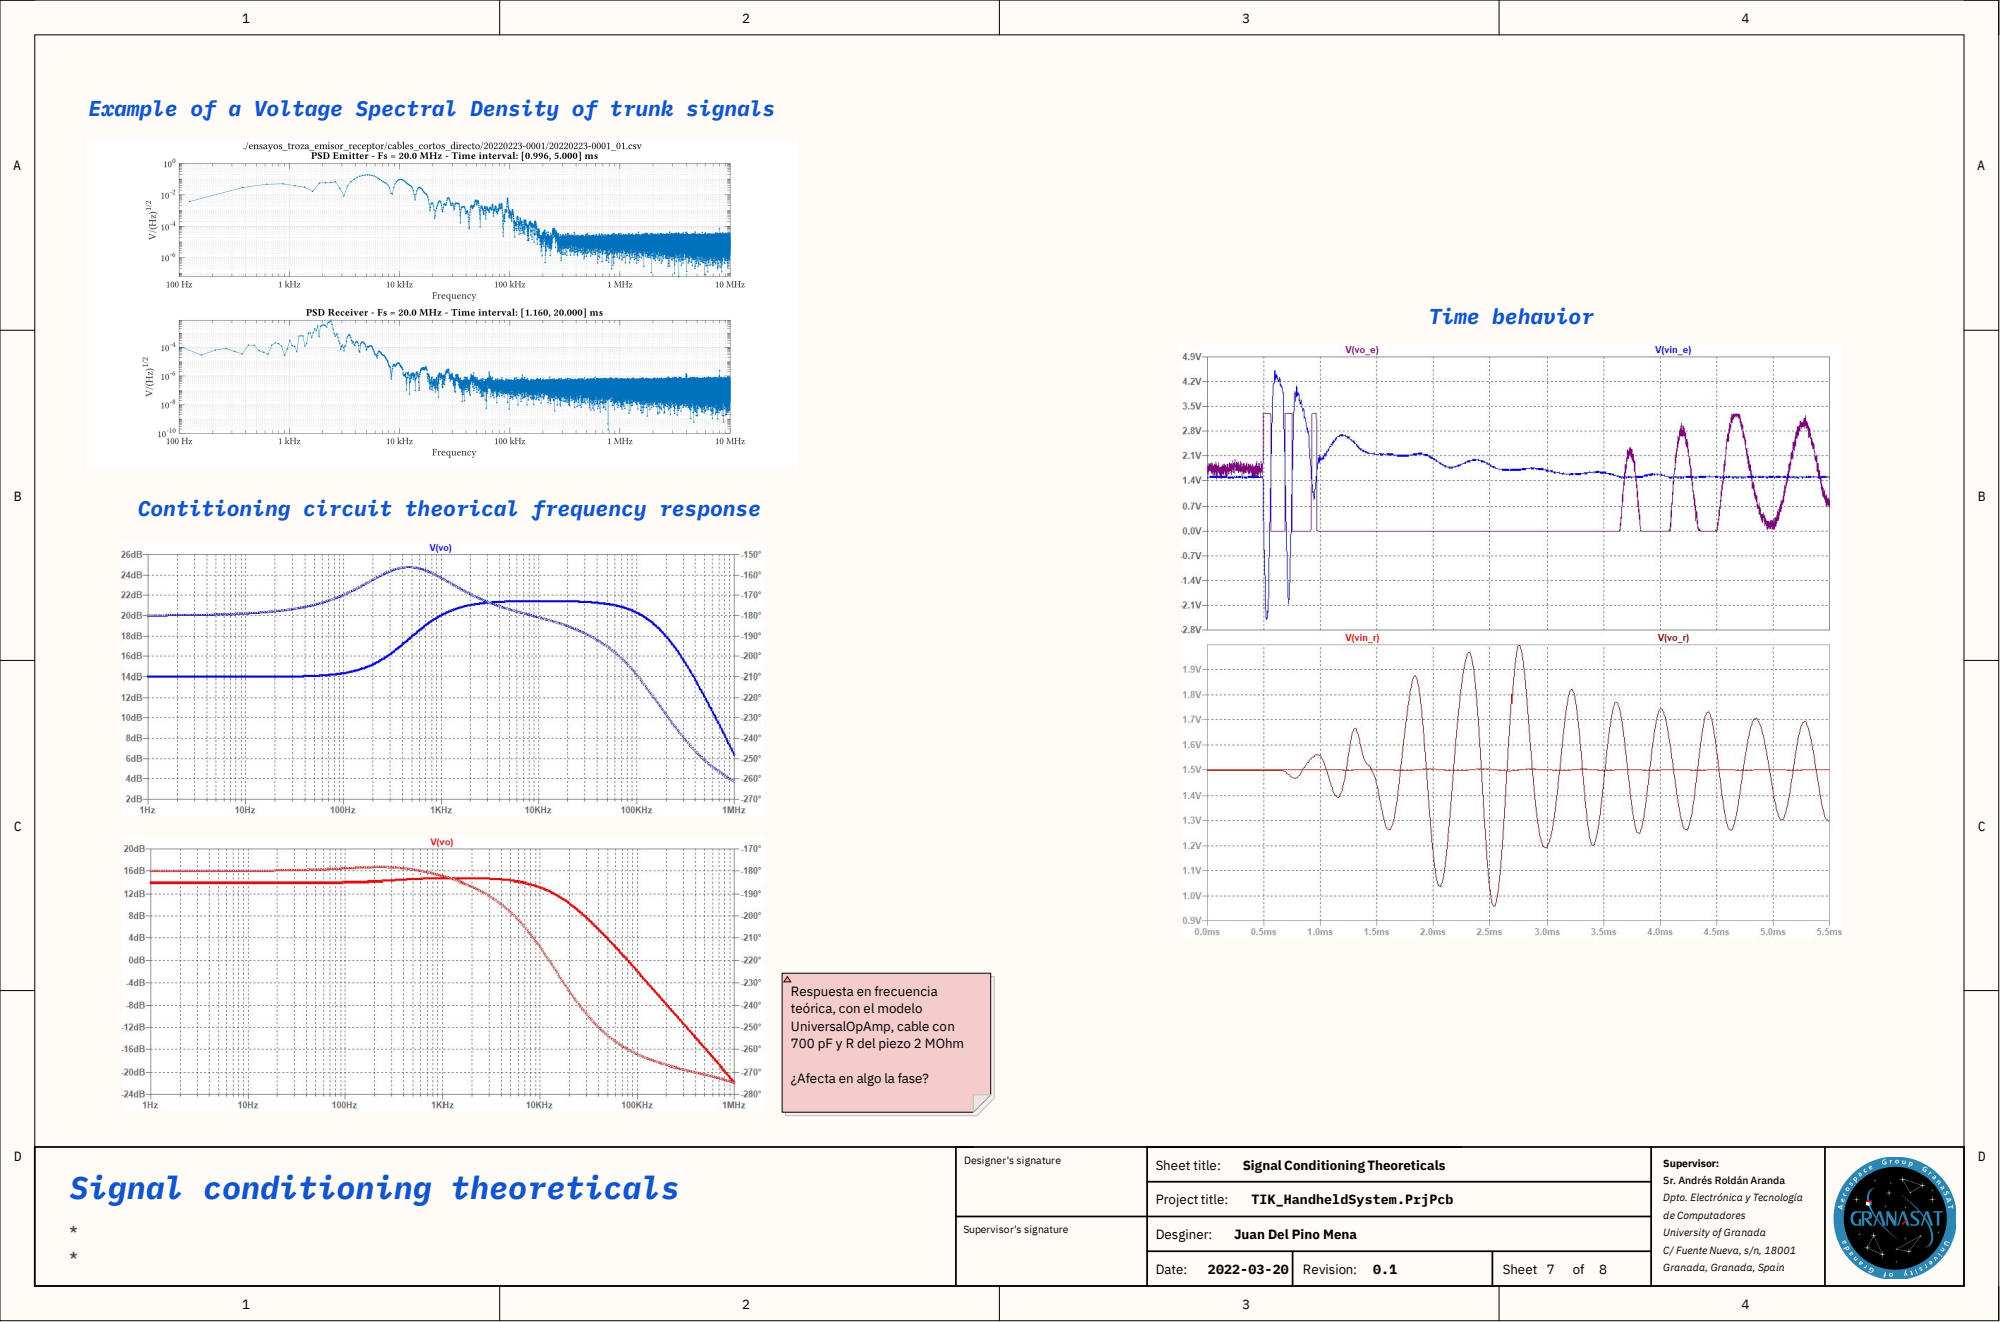
[picture p256: page 7]

Exampl e of a Vol tage Spectral Density of trunk signal s

Contitioning circuit theorical frequency response

Respuesta en frecuencia
teórica, con el modelo
UniversalOpAmp, cable con
700 pF y R del piezo 2 MOhm

¿Afecta en algo la fase?

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

TI K_ H an dh el dSys tem. P rj P c b

Supervisor's signature | Desginer: Juan Del Pino Mena

Date: 2022- 03- 20 | Revision: 0. 1 | Sheet 7 of 8

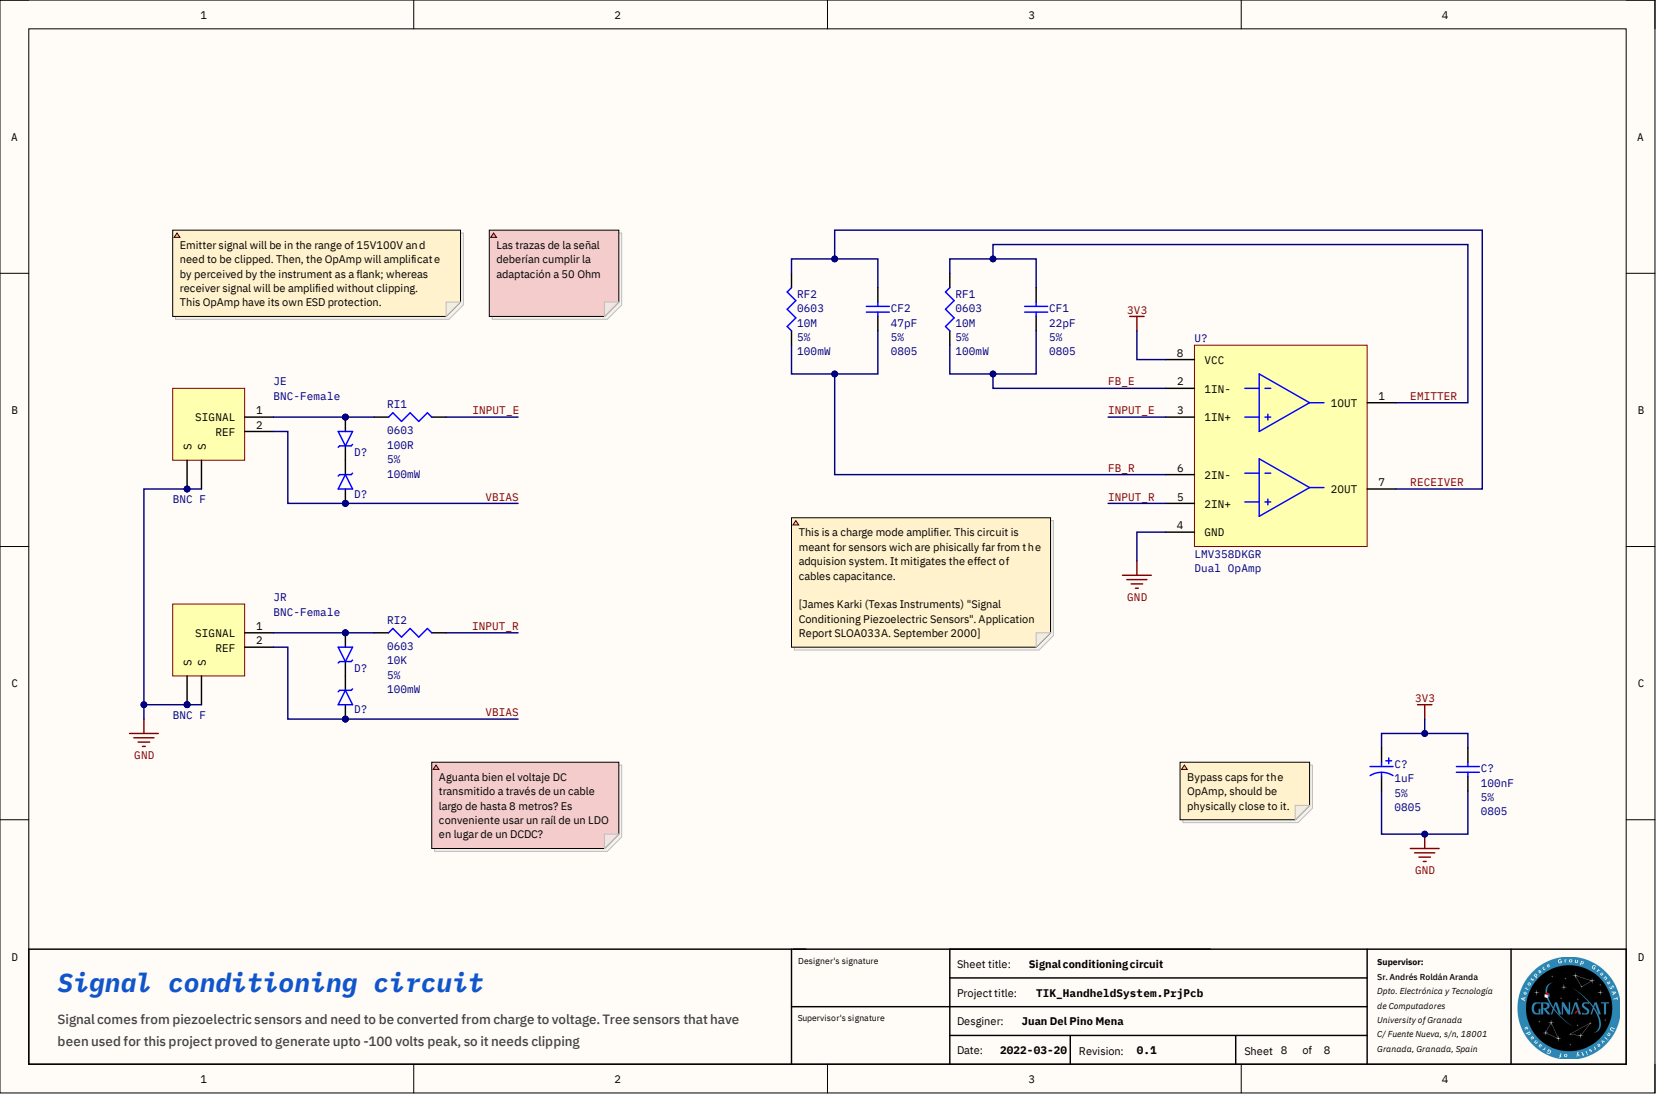
[picture p257: page 8]

quision system. It mitigates the
