dpmj/Bachelor_Thesis_TIK_Handheld_Device/ASSETS/TIK_CASE/FUTURE/future.pdf

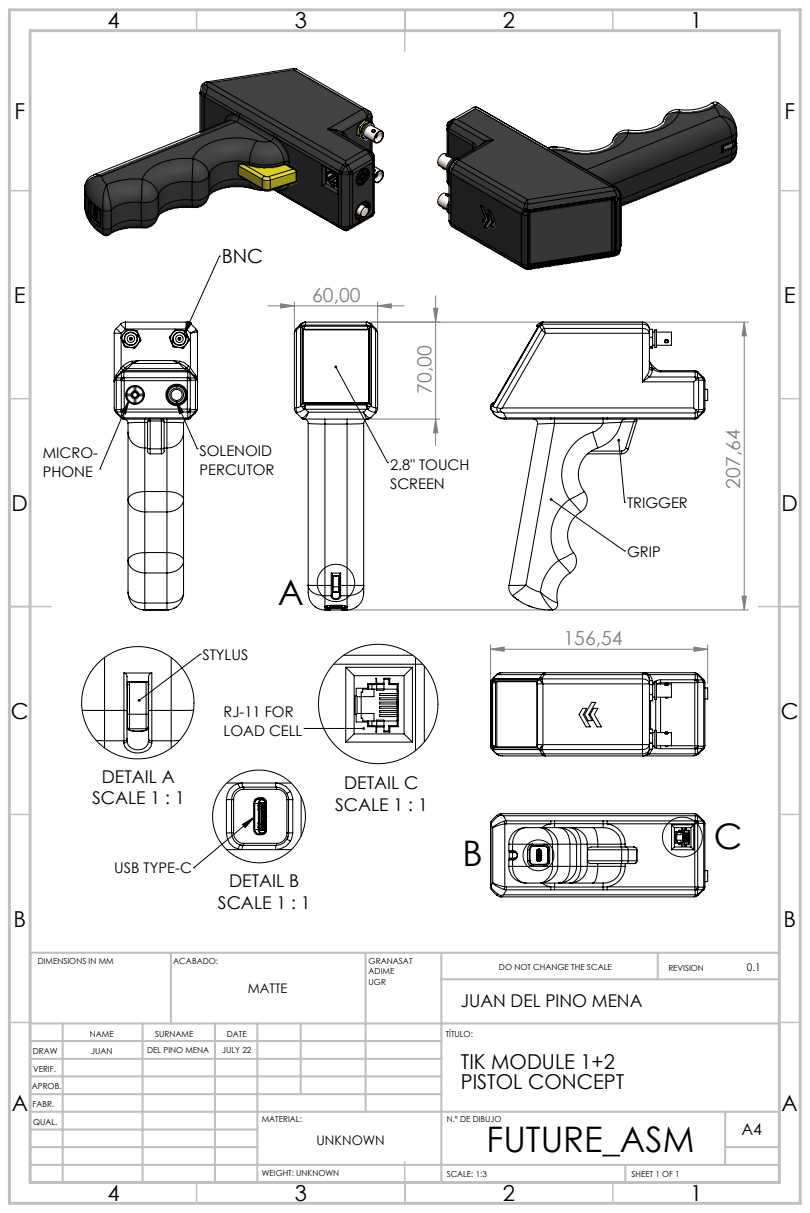
[picture p258: page 1]
2.8" TOUCH; DETAIL A SCALE 1 : 1; DETAIL B SCALE 1 : 1; USB TYPE-C; DETAIL C SCALE 1 : 1; RJ-11 FOR LOAD CELL; DIMENSIONS IN MM; ACABADO:; GRANASAT; DO NOT CHANGE THE SCALE; REVISION; SCALE: 1:3; SHEET 1 OF 1; WEIGHT: UNKNOWN

JUAN DEL PINO MENA

NAME | SURNAME | DATE | | | | TÍTULO: TIK MODULE 1+2 PISTOL CONCEPT

DRAW | JUAN | DEL PINO MENA | JULY 22
VERIF.
APROB.
FABR.
QUAL. | | | | MATERIAL: UNKNOWN | N.º DE DIBUJO FUTURE_ASM | A4
